alnwlsn/wc-80-archive/old-unknown/design-tables.xlsx

Sheet: io-addresses
Function | MEM | IO | 7 | 6 | 5 | 4 | 3 | 2 | 1 | 0 | 7 | 6 | 5 | 4 | 3 | 2 | 1 | 0 | value set on system reset boot
Disk Command/Status | 37EC | F0 |  |  |  |  |  |  |  |  |  |  |  |  |  |  |  |  | 0
Density Select | 37EC | F0 |  |  |  |  |  |  |  |  | 1 | 1 | 1 | 1 | 1 | x | x | DD | f8
Disk Track | 37ED | F1 |  |  |  |  |  |  |  |  |  |  |  |  |  |  |  |  | 0
Disk Sector | 37EE | F2 |  |  |  |  |  |  |  |  |  |  |  |  |  |  |  |  | 0
5/8 Select | 37EE | F2 |  |  |  |  |  |  |  |  | 1 | 8INCH | x | x | x | x | x | x | 80
Disk Data | 37EF | F3 |  |  |  |  |  |  |  |  |  |  |  |  |  |  |  |  | 0
Disk Select | 37E1 | F4 |  |  |  |  |  |  |  |  |  |  |  |  | DRV3 | DRV2 | DRV1 | DRV0 | 0
Model 3 Options | N/A | F4 |  |  |  |  |  |  |  |  | DD | x | WPRE | SIDE1 |  |  |  |  | 0
Interrupt Status | 37E0 | F6 | Clock | Disk |  |  |  |  |  |  |  |  |  |  |  |  |  |  | 0
WC80 Options | N/A | F6 |  |  |  |  |  |  |  |  |  |  |  |  | x | x | MOD3 | 2793 | 1
Printer | 37E8 | F8 |  |  |  |  |  |  |  |  |  |  |  |  |  |  |  |  | 0
mem bank 0 |  | 70 |  |  |  |  |  |  |  |  | !EXMEM 0000-3FFF |  | RAM !ROM
mem bank 1 |  | 71 |  |  |  |  |  |  |  |  | !EXMEM 4000-7FFF |  | RAM !ROM
mem bank 2 |  | 72 |  |  |  |  |  |  |  |  | !EXMEM 8000-BFFF |  | RAM !ROM
mem bank 3 |  | 73 |  |  |  |  |  |  |  |  | !EXMEM C000-FFFF |  | RAM !ROM
cpu display 4th char |  | 74
cpu display 3rd char |  | 75
cpu display 2nd char |  | 76
cpu display 1st char (left) |  | 77
sn76489 |  | a0 |  |  |  |  |  |  |  |  |  |  |  |  |  |  |  |  | 0
interrupt status |  | a0
ym2413 address |  | a2 |  |  |  |  |  |  |  |  |  |  |  |  |  |  |  |  | 1
ym2413 data |  | a3
ym2612 1-3 address |  | a4 |  |  |  |  |  |  |  |  |  |  |  |  |  |  |  |  | 2
ym2612 1-3 data |  | a5
ym2612 4-6 address |  | a6 |  |  |  |  |  |  |  |  |  |  |  |  |  |  |  |  | 3
ym2612 4-6 data |  | a7
ymf262 address0/status |  | a8 |  |  |  |  |  |  |  |  |  |  |  |  |  |  |  |  | 4
ymf262 data |  | a9
ymf262 address1 |  | aa |  |  |  |  |  |  |  |  |  |  |  |  |  |  |  |  | 5
orchestra 85 dac (!d7) |  | b5 |  |  |  |  |  |  |  |  |  |  |  |  |  |  |  |  | 0
orchestra 85 dac (!d7) |  | b9
orchestra 80 dac |  | bb
orchestra 80 dac |  | bc
sound options |  | bf
cassette port out |  | ff |  |  |  |  |  |  |  |  |  |  |  |  |  |  | v | v | 0
Keyboard option register |  | 78 |  |  |  |  |  |  |  |  | KEYM1 | KEYM0 | LED5 | LED4 | LED3 | LED2 | LED1 | LED0
CF card |  | 50
 |  | 51
 |  | 52
 |  | 53
 |  | 54
 |  | 55
 |  | 56
 |  | 57
vidstat |  | 5f |  |  |  |  | VS | HS | BTN | LPEN
vid options 1 |  | 5f |  |  |  |  |  |  |  |  | !RESET | DC2 | DC1 | DC0 | PL2 | PL1 | PL0 | CHIP | 0x72 reset | 0xf2 - 8x80 mode | 0xe6 - 64x6 mode
vid options 2 |  | 5e |  |  |  |  |  |  |  |  | ADR3 | ADR2 | ADR1 | ADR0 | MSK3 | MSK2 | MSK1 | MSK0
CRT controller data |  | 5d
CRT controller address |  | 5c
External hi-mem bank 0 |  | 7c
External hi-mem bank 1 |  | 7d
External hi-mem bank 2 |  | 7e
External hi-mem bank 3 |  | 7f
DSKY IO registers . . . |  | 60
. . . Read = key matrix |  | 61
. . . Write = display |  | 62
"" |  | 63
"" |  | 64
"" |  | 65
"" |  | 66
"" |  | 67
"" |  | 68
"" |  | 69
"" |  | 6a
"" |  | 6b
"" |  | 6c
"" |  | 6d
"" |  | 6e
* left most digit |  | 6f
KEYM = 0 keyboard | 3800-38ff
KEYM = 1 keyboard | ef00-efff
KEYM = 2 keyboard | f400-f4ff
KEYM = 3 keyboard | 7800-78ff

Sheet: memmap
Device |  | Main ROM / RAM | Keyboard Matrix | Arduino Board | Video Memory
 |  |  |  | Shared RAM and Extra RAM
IO Addr |  | 0x70-0x73 | 0x78 | 0x7c-0x7f | 0x5f
Memory Space | 0000 | Bank 0 0x70
 | 0400
 | 0800
 | 0C00
 | 1000
 | 1400
 | 1800
 | 1C00
 | 2000
 | 2400
 | 2800
 | 2C00
 | 3000 |  |  | 3000-33ff 1K dual port RAM
 | 3400
 | 3800 |  | 3800-38ff - TRS-80 model 1; KEYM = 0
 | 3C00 |  |  |  | IO 0x5e = 0x38 - TRS-80 64x16 Screen
 | 4000 | Bank 1 0x71
 | 4400
 | 4800
 | 4C00
 | 5000
 | 5400
 | 5800
 | 5C00
 | 6000
 | 6400
 | 6800
 | 6C00
 | 7000
 | 7400
 | 7800 |  | 7800-78ff - trs80 model 1 in slot 1; KEYM = 3
 | 7C00
 | 8000 | Bank 2 0x72 |  | HiMem Bank 0 0x7c
 | 8400
 | 8800
 | 8C00
 | 9000
 | 9400
 | 9800
 | 9C00
 | A000 |  |  | HiMem Bank 1 0x7d
 | A400
 | A800
 | AC00
 | B000
 | B400
 | B800
 | BC00
 | C000 | Bank 3 0x73 |  | HiMem Bank 2 0x7d
 | C400
 | C800
 | CC00
 | D000
 | D400
 | D800
 | DC00
 | E000 |  |  | HiMem Bank 3 0x7e
 | E400
 | E800
 | EC00 |  | EF00-EFFF; KEYM = 1
 | F000
 | F400 |  | F400-F4FF - trs-80 model 4; KEYM = 2
 | F800
 | FC00
Description/Notes |  | IO addresses 0x70-0x73 for each bank, select 1 of 32 banks in rom (0x00-0x20) or ram (0x20-0x40). 16K each | IO address 0x78 - Set bits 6:7 to select 1 of 4 keyboard memory locations | IO addresses 0x7c-0x7f for each bank, select 1 of 64 banks of RAM, 8K each | Ram can be aligned to any of the bold boxes above, and each of 4 1K sections can be masked or unmasked within.
 |  |  |  | If bit 7 is set on any of the 4 bank selections, the extra ram there will be removed and the address space open to be used by other devices | IO address 0x5e is used to set the location and mask: value = 0xam, where: nibble a is address location, and nibble m is the mask. Bits set to 0 will disable that section
 |  | EXMEM - clearing of bit 7 will enable other devices to override rom/ram in memory space |  | This HIMem area (0x8000 and above) corresponds to the memory stored in the Expansion Interface in a real TRS-80
 |  |  |  |  | example:
 |  |  |  |  | 0x38 - start at address 0x3000; mask all but section 3 (bit3 set) - provides 1K section at 0x3c00
 |  |  |  |  | 0x5F - start at address 0x5000, aand use all 4 sections provides 4K of ram at 0x5000-0x5fff

Sheet: memmap(old)
 |  | Main ROM / RAM | Keyboard Matrix | Hi-mem ram on Arduino board | Arduino Dual Port Shared RAM
 | IO Addr | 0x70-0x73 | 0x78 | 0x7c-0x7f
Memory Space | 0000 | Bank 0 0x70 |  |  |  | 1 | 1 | 100
 | 1000 |  |  |  |  | 2 | 2 | 200
 | 2000 |  |  |  |  | 3 | 3 | 300
 | 3000 |  | 3800-38ff - TRS-80 model 1 - KEYM = 0 | 3000-33ff 1K dual port RAM |  | 4 | 4 | 400
 | 4000 | Bank 1 0x71 |  |  |  | 5 | 5 | 500
 | 5000 |  |  |  |  | 6 | 6 | 600
 | 6000 |  |  |  |  | 7 | 7 | 700
 | 7000 |  | 7800-78ff - trs80 model 1 in slot 1 KEYM = 3 |  |  | 8 | 8 | 800
 | 8000 | Bank 2 0x72 |  | HiMem Bank 0 0x7c |  | 9 | 9 | 900
 | 9000 |  |  |  |  | 10 | A | A00
 | A000 |  |  | HiMem Bank 1 0x7d |  | 11 | B | B00
 | B000 |  |  |  |  | 12 | C | C00
 | C000 | Bank 3 0x73 |  | HiMem Bank 2 0x7d |  | 13 | D | D00
 | D000 |  |  |  |  | 14 | E | E00
 | E000 |  | EF00-EFFF KEYM = 1 | HiMem Bank 3 0x7e |  | 15 | F | F00
 | F000 |  | F400-F4FF - trs-80 model 4 KEYM = 2 |  |  | 16 | 10 | 1000
 |  |  |  |  |  | 17 | 11 | 1100
 |  |  |  |  |  | 18 | 12 | 1200
 |  | IO addresses 0x70-0x73 for each bank, select 1 of 32 banks in rom (0x00-0x20) or ram (0x20-0x40). 16K each | IO address 0x78 - Set bits 6:7 to select 1 of 4 keyboard memory locations | IO addresses 0x7c-0x7f for each bank, select 1 of 64 banks of RAM, 8K each |  | 19 | 13 | 1300
 |  |  |  | If bit 7 is set on any of the 4 bank selections, the extra ram there will be removed and the address space open to be used by other devices |  | 20 | 14 | 1400
 |  |  |  |  |  | 21 | 15 | 1500
 |  |  |  |  |  | 22 | 16 | 1600
 |  |  |  |  |  | 23 | 17 | 1700
 |  | EXMEM - clearing of bit 7 will enable other devices to override rom/ram in memory space |  | This HIMem area (0x8000 and above) corresponds to the memory stored in the Expansion Interface in a real TRS-80 |  | 24 | 18 | 1800
 |  |  |  |  |  | 25 | 19 | 1900
 |  |  |  |  |  | 26 | 1A | 1A00
 |  |  |  |  |  | 27 | 1B | 1B00
 |  |  |  |  |  | 28 | 1C | 1C00
 |  |  |  |  |  | 29 | 1D | 1D00
 |  |  |  |  |  | 30 | 1E | 1E00
 |  |  |  |  |  | 31 | 1F | 1F00
 |  |  |  |  |  | 32 | 20 | 2000
 |  |  |  |  |  | 33 | 21 | 2100
 |  |  |  |  |  | 34 | 22 | 2200
 |  |  |  |  |  | 35 | 23 | 2300
 |  |  |  |  |  | 36 | 24 | 2400
 |  |  |  |  |  | 37 | 25 | 2500
 |  |  |  |  |  | 38 | 26 | 2600
 |  |  |  |  |  | 39 | 27 | 2700
 |  |  |  |  |  | 40 | 28 | 2800
 |  |  |  |  |  | 41 | 29 | 2900
 |  |  |  |  |  | 42 | 2A | 2A00
 |  |  |  |  |  | 43 | 2B | 2B00
 |  |  |  |  |  | 44 | 2C | 2C00
 |  |  |  |  |  | 45 | 2D | 2D00
 |  |  |  |  |  | 46 | 2E | 2E00
 |  |  |  |  |  | 47 | 2F | 2F00
 |  |  |  |  |  | 48 | 30 | 3000
 |  |  |  |  |  | 49 | 31 | 3100
 |  |  |  |  |  | 50 | 32 | 3200
 |  |  |  |  |  | 51 | 33 | 3300
 |  |  |  |  |  | 52 | 34 | 3400
 |  |  |  |  |  | 53 | 35 | 3500
 |  |  |  |  |  | 54 | 36 | 3600
 |  |  |  |  |  | 55 | 37 | 3700
 |  |  |  |  |  | 56 | 38 | 3800
 |  |  |  |  |  | 57 | 39 | 3900
 |  |  |  |  |  | 58 | 3A | 3A00
 |  |  |  |  |  | 59 | 3B | 3B00
 |  |  |  |  |  | 60 | 3C | 3C00
 |  |  |  |  |  | 61 | 3D | 3D00
 |  |  |  |  |  | 62 | 3E | 3E00
 |  |  |  |  |  | 63 | 3F | 3F00
 |  |  |  |  |  | 64 | 40 | 4000
 |  |  |  |  |  | 65 | 41 | 4100
 |  |  |  |  |  | 66 | 42 | 4200
 |  |  |  |  |  | 67 | 43 | 4300
 |  |  |  |  |  | 68 | 44 | 4400
 |  |  |  |  |  | 69 | 45 | 4500
 |  |  |  |  |  | 70 | 46 | 4600
 |  |  |  |  |  | 71 | 47 | 4700
 |  |  |  |  |  | 72 | 48 | 4800
 |  |  |  |  |  | 73 | 49 | 4900
 |  |  |  |  |  | 74 | 4A | 4A00
 |  |  |  |  |  | 75 | 4B | 4B00
 |  |  |  |  |  | 76 | 4C | 4C00
 |  |  |  |  |  | 77 | 4D | 4D00
 |  |  |  |  |  | 78 | 4E | 4E00
 |  |  |  |  |  | 79 | 4F | 4F00
 |  |  |  |  |  | 80 | 50 | 5000
 |  |  |  |  |  | 81 | 51 | 5100
 |  |  |  |  |  | 82 | 52 | 5200
 |  |  |  |  |  | 83 | 53 | 5300
 |  |  |  |  |  | 84 | 54 | 5400
 |  |  |  |  |  | 85 | 55 | 5500
 |  |  |  |  |  | 86 | 56 | 5600
 |  |  |  |  |  | 87 | 57 | 5700
 |  |  |  |  |  | 88 | 58 | 5800
 |  |  |  |  |  | 89 | 59 | 5900
 |  |  |  |  |  | 90 | 5A | 5A00
 |  |  |  |  |  | 91 | 5B | 5B00
 |  |  |  |  |  | 92 | 5C | 5C00
 |  |  |  |  |  | 93 | 5D | 5D00
 |  |  |  |  |  | 94 | 5E | 5E00
 |  |  |  |  |  | 95 | 5F | 5F00
 |  |  |  |  |  | 96 | 60 | 6000
 |  |  |  |  |  | 97 | 61 | 6100
 |  |  |  |  |  | 98 | 62 | 6200
 |  |  |  |  |  | 99 | 63 | 6300
 |  |  |  |  |  | 100 | 64 | 6400
 |  |  |  |  |  | 101 | 65 | 6500
 |  |  |  |  |  | 102 | 66 | 6600
 |  |  |  |  |  | 103 | 67 | 6700
 |  |  |  |  |  | 104 | 68 | 6800
 |  |  |  |  |  | 105 | 69 | 6900
 |  |  |  |  |  | 106 | 6A | 6A00
 |  |  |  |  |  | 107 | 6B | 6B00
 |  |  |  |  |  | 108 | 6C | 6C00
 |  |  |  |  |  | 109 | 6D | 6D00
 |  |  |  |  |  | 110 | 6E | 6E00
 |  |  |  |  |  | 111 | 6F | 6F00
 |  |  |  |  |  | 112 | 70 | 7000
 |  |  |  |  |  | 113 | 71 | 7100
 |  |  |  |  |  | 114 | 72 | 7200
 |  |  |  |  |  | 115 | 73 | 7300
 |  |  |  |  |  | 116 | 74 | 7400
 |  |  |  |  |  | 117 | 75 | 7500
 |  |  |  |  |  | 118 | 76 | 7600
 |  |  |  |  |  | 119 | 77 | 7700
 |  |  |  |  |  | 120 | 78 | 7800
 |  |  |  |  |  | 121 | 79 | 7900
 |  |  |  |  |  | 122 | 7A | 7A00
 |  |  |  |  |  | 123 | 7B | 7B00
 |  |  |  |  |  | 124 | 7C | 7C00
 |  |  |  |  |  | 125 | 7D | 7D00
 |  |  |  |  |  | 126 | 7E | 7E00
 |  |  |  |  |  | 127 | 7F | 7F00
 |  |  |  |  |  | 128 | 80 | 8000
 |  |  |  |  |  | 129 | 81 | 8100
 |  |  |  |  |  | 130 | 82 | 8200
 |  |  |  |  |  | 131 | 83 | 8300
 |  |  |  |  |  | 132 | 84 | 8400
 |  |  |  |  |  | 133 | 85 | 8500
 |  |  |  |  |  | 134 | 86 | 8600
 |  |  |  |  |  | 135 | 87 | 8700
 |  |  |  |  |  | 136 | 88 | 8800
 |  |  |  |  |  | 137 | 89 | 8900
 |  |  |  |  |  | 138 | 8A | 8A00
 |  |  |  |  |  | 139 | 8B | 8B00
 |  |  |  |  |  | 140 | 8C | 8C00
 |  |  |  |  |  | 141 | 8D | 8D00
 |  |  |  |  |  | 142 | 8E | 8E00
 |  |  |  |  |  | 143 | 8F | 8F00
 |  |  |  |  |  | 144 | 90 | 9000
 |  |  |  |  |  | 145 | 91 | 9100
 |  |  |  |  |  | 146 | 92 | 9200
 |  |  |  |  |  | 147 | 93 | 9300
 |  |  |  |  |  | 148 | 94 | 9400
 |  |  |  |  |  | 149 | 95 | 9500
 |  |  |  |  |  | 150 | 96 | 9600
 |  |  |  |  |  | 151 | 97 | 9700
 |  |  |  |  |  | 152 | 98 | 9800
 |  |  |  |  |  | 153 | 99 | 9900
 |  |  |  |  |  | 154 | 9A | 9A00
 |  |  |  |  |  | 155 | 9B | 9B00
 |  |  |  |  |  | 156 | 9C | 9C00
 |  |  |  |  |  | 157 | 9D | 9D00
 |  |  |  |  |  | 158 | 9E | 9E00
 |  |  |  |  |  | 159 | 9F | 9F00
 |  |  |  |  |  | 160 | A0 | A000
 |  |  |  |  |  | 161 | A1 | A100
 |  |  |  |  |  | 162 | A2 | A200
 |  |  |  |  |  | 163 | A3 | A300
 |  |  |  |  |  | 164 | A4 | A400
 |  |  |  |  |  | 165 | A5 | A500
 |  |  |  |  |  | 166 | A6 | A600
 |  |  |  |  |  | 167 | A7 | A700
 |  |  |  |  |  | 168 | A8 | A800
 |  |  |  |  |  | 169 | A9 | A900
 |  |  |  |  |  | 170 | AA | AA00
 |  |  |  |  |  | 171 | AB | AB00
 |  |  |  |  |  | 172 | AC | AC00
 |  |  |  |  |  | 173 | AD | AD00
 |  |  |  |  |  | 174 | AE | AE00
 |  |  |  |  |  | 175 | AF | AF00
 |  |  |  |  |  | 176 | B0 | B000
 |  |  |  |  |  | 177 | B1 | B100
 |  |  |  |  |  | 178 | B2 | B200
 |  |  |  |  |  | 179 | B3 | B300
 |  |  |  |  |  | 180 | B4 | B400
 |  |  |  |  |  | 181 | B5 | B500
 |  |  |  |  |  | 182 | B6 | B600
 |  |  |  |  |  | 183 | B7 | B700
 |  |  |  |  |  | 184 | B8 | B800
 |  |  |  |  |  | 185 | B9 | B900
 |  |  |  |  |  | 186 | BA | BA00
 |  |  |  |  |  | 187 | BB | BB00
 |  |  |  |  |  | 188 | BC | BC00
 |  |  |  |  |  | 189 | BD | BD00
 |  |  |  |  |  | 190 | BE | BE00
 |  |  |  |  |  | 191 | BF | BF00
 |  |  |  |  |  | 192 | C0 | C000
 |  |  |  |  |  | 193 | C1 | C100
 |  |  |  |  |  | 194 | C2 | C200
 |  |  |  |  |  | 195 | C3 | C300
 |  |  |  |  |  | 196 | C4 | C400
 |  |  |  |  |  | 197 | C5 | C500
 |  |  |  |  |  | 198 | C6 | C600
 |  |  |  |  |  | 199 | C7 | C700
 |  |  |  |  |  | 200 | C8 | C800
 |  |  |  |  |  | 201 | C9 | C900
 |  |  |  |  |  | 202 | CA | CA00
 |  |  |  |  |  | 203 | CB | CB00
 |  |  |  |  |  | 204 | CC | CC00
 |  |  |  |  |  | 205 | CD | CD00
 |  |  |  |  |  | 206 | CE | CE00
 |  |  |  |  |  | 207 | CF | CF00
 |  |  |  |  |  | 208 | D0 | D000
 |  |  |  |  |  | 209 | D1 | D100
 |  |  |  |  |  | 210 | D2 | D200
 |  |  |  |  |  | 211 | D3 | D300
 |  |  |  |  |  | 212 | D4 | D400
 |  |  |  |  |  | 213 | D5 | D500
 |  |  |  |  |  | 214 | D6 | D600
 |  |  |  |  |  | 215 | D7 | D700
 |  |  |  |  |  | 216 | D8 | D800
 |  |  |  |  |  | 217 | D9 | D900
 |  |  |  |  |  | 218 | DA | DA00
 |  |  |  |  |  | 219 | DB | DB00
 |  |  |  |  |  | 220 | DC | DC00
 |  |  |  |  |  | 221 | DD | DD00
 |  |  |  |  |  | 222 | DE | DE00
 |  |  |  |  |  | 223 | DF | DF00
 |  |  |  |  |  | 224 | E0 | E000
 |  |  |  |  |  | 225 | E1 | E100
 |  |  |  |  |  | 226 | E2 | E200
 |  |  |  |  |  | 227 | E3 | E300
 |  |  |  |  |  | 228 | E4 | E400
 |  |  |  |  |  | 229 | E5 | E500
 |  |  |  |  |  | 230 | E6 | E600
 |  |  |  |  |  | 231 | E7 | E700
 |  |  |  |  |  | 232 | E8 | E800
 |  |  |  |  |  | 233 | E9 | E900
 |  |  |  |  |  | 234 | EA | EA00
 |  |  |  |  |  | 235 | EB | EB00
 |  |  |  |  |  | 236 | EC | EC00
 |  |  |  |  |  | 237 | ED | ED00
 |  |  |  |  |  | 238 | EE | EE00
 |  |  |  |  |  | 239 | EF | EF00
 |  |  |  |  |  | 240 | F0 | F000
 |  |  |  |  |  | 241 | F1 | F100
 |  |  |  |  |  | 242 | F2 | F200
 |  |  |  |  |  | 243 | F3 | F300
 |  |  |  |  |  | 244 | F4 | F400
 |  |  |  |  |  | 245 | F5 | F500
 |  |  |  |  |  | 246 | F6 | F600
 |  |  |  |  |  | 247 | F7 | F700
 |  |  |  |  |  | 248 | F8 | F800
 |  |  |  |  |  | 249 | F9 | F900
 |  |  |  |  |  | 250 | FA | FA00
 |  |  |  |  |  | 251 | FB | FB00
 |  |  |  |  |  | 252 | FC | FC00
 |  |  |  |  |  | 253 | FD | FD00
 |  |  |  |  |  | 254 | FE | FE00
 |  |  |  |  |  | 255 | FF | FF00

Sheet: bus-pinout
org | lu | ul | modi | pin | desc | TRS-80 EXP HEADER |  |  |  | TRS-80 EXP HEADER |  |  |  | TRS-80 PROTO HEADER |  |  |  | TRS-80 PROTO HEADER
 |  |  |  |  |  | M UP |  |  |  | F UP |  |  |  | M UP |  |  |  | F UP
1 | 0 | 0 | 2 | RAS* | Row Address Strobe output for 16 pin dynamic rams | SYSRES* | 1 | 2 | RAS* | RAS* | 2 | 1 | SYSRES* | vcc | 1 | 2 | vcc | vcc | 2 | 1 | vcc
3 | 0 | 0 | 4 | CAS* | Column Address Strobe output for 16 pin dynamic rams | A10 | 3 | 4 | CAS* | CAS* | 4 | 3 | A10 | gnd | 3 | 4 | gnd | gnd | 4 | 3 | gnd
5 | 0 | 0 | 6 | A12 | Address output | A13 | 5 | 6 | A12 | A12 | 6 | 5 | A13 | \memrq | 5 | 6 | \ioreq | \ioreq | 6 | 5 | \memrq
7 | 0 | 0 | 8 | A15 | Address output | GND | 7 | 8 | A15 | A15 | 8 | 7 | GND | \rd | 7 | 8 | \wr | \wr | 8 | 7 | \rd
9 | 0 | 0 | 10 | A11 | Address output | A14 | 9 | 10 | A11 | A11 | 10 | 9 | A14 | \inuse | 9 | 10 | \disable | \disable | 10 | 9 | \inuse
11 | 0 | 0 | 12 | A8 | Address output | OUT* | 11 | 12 | A8 | A8 | 12 | 11 | OUT* | d0 | 11 | 12 | d1 | d1 | 12 | 11 | d0
13 | 0 | 0 | 14 | WR* | Memory Write strobe output | INTAK* | 13 | 14 | WR* | WR* | 14 | 13 | INTAK* | d2 | 13 | 14 | d3 | d3 | 14 | 13 | d2
15 | 0 | 0 | 16 | RD* | Memory Read strobe output | MUX | 15 | 16 | RD* | RD* | 16 | 15 | MUX | d4 | 15 | 16 | d5 | d5 | 16 | 15 | d4
17 | 0 | 0 | 18 | A9 | Address output | D4 | 17 | 18 | A9 | A9 | 18 | 17 | D4 | d6 | 17 | 18 | d7 | d7 | 18 | 17 | d6
19 | 0 | 0 | 20 | IN* | Peripheral Read strobe output | D7 | 19 | 20 | IN* | IN* | 20 | 19 | D7 | a0 | 19 | 20 | a1 | a1 | 20 | 19 | a0
21 | 0 | 0 | 22 | INT* | Interrupt input (Maskable) | D1 | 21 | 22 | INT* | INT* | 22 | 21 | D1 | a2 | 21 | 22 | a3 | a3 | 22 | 21 | a2
23 | 0 | 0 | 24 | TEST* | A logic 0 on TEST* input tri-states A0-A15, D0-D7, WR*, RD*, IN*, OUT*, RAS*, CAS* and MUX*. | D6 | 23 | 24 | TEST* | TEST* | 24 | 23 | D6 | a4 | 23 | 24 | a5 | a5 | 24 | 23 | a4
25 | 0 | 0 | 26 | A0 | Address output | D3 | 25 | 26 | A0 | A0 | 26 | 25 | D3 | a6 | 25 | 26 | a7 | a7 | 26 | 25 | a6
27 | 0 | 0 | 28 | A1 | Address output | D5 | 27 | 28 | A1 | A1 | 28 | 27 | D5 | a8 | 27 | 28 | a9 | a9 | 28 | 27 | a8
29 | 0 | 0 | 30 | GND | Signal ground | D0 | 29 | 30 | GND | GND | 30 | 29 | D0 | a10 | 29 | 30 | a11 | a11 | 30 | 29 | a10
31 | 0 | 0 | 32 | A4 | Address output | D2 | 31 | 32 | A4 | A4 | 32 | 31 | D2 | a12 | 31 | 32 | a13 | a13 | 32 | 31 | a12
33 | 0 | 0 | 34 | WAIT* | Processor wait input, to allow for slow memory | A3 | 33 | 34 | WAIT* | WAIT* | 34 | 33 | A3 | a14 | 33 | 34 | a15 | a15 | 34 | 33 | a14
35 | 0 | 0 | 36 | A5 | Address output | A7 | 35 | 36 | A5 | A5 | 36 | 35 | A7 |  | 35 | 36 |  |  | 36 | 35
37 | 0 | 0 | 38 | GND | Signal ground | A6 | 37 | 38 | GND | GND | 38 | 37 | A6 |  | 37 | 38 |  |  | 38 | 37
39 | 0 | 0 | 40 | +5V | (limited current - Level I Model 1s only) | A2 | 39 | 40 | +5V | +5V | 40 | 39 | A2 |  | 39 | 40 |  |  | 40 | 39
2 | 1 | 1 | 1 | SYSRES* | System reset output. Low during power-up initialize or when the reset button is pressed
4 | 1 | 1 | 3 | A10 | Address output
6 | 1 | 1 | 5 | A13 | Address output | TRS-80 W HEADER |  |  |  | TRS-80 W HEADER
8 | 1 | 1 | 7 | GND | Signal Ground | M UP |  |  |  | F UP
10 | 1 | 1 | 9 | A14 | Address output | SYSRES* | 1 | 2 | RAS* | RAS* | 2 | 1 | SYSRES*
12 | 1 | 1 | 11 | OUT* | Peripheral Write strobe output | A10 | 3 | 4 | EXMEM* | EXMEM* | 4 | 3 | A10
14 | 1 | 1 | 13 | INTAK* | Interrupt Acknowledge output | A13 | 5 | 6 | A12 | A12 | 6 | 5 | A13
16 | 1 | 1 | 15 | MUX | Multiplexer Control output for 16 pin dynamic RAMs | GND | 7 | 8 | A15 | A15 | 8 | 7 | GND
18 | 1 | 1 | 17 | D4 | Bidirectional data bus | A14 | 9 | 10 | A11 | A11 | 10 | 9 | A14
20 | 1 | 1 | 19 | D7 | Bidirectional data bus | OUT* | 11 | 12 | A8 | A8 | 12 | 11 | OUT*
22 | 1 | 1 | 21 | D1 | Bidirectional data bus | INTAK* | 13 | 14 | WR* | WR* | 14 | 13 | INTAK*
24 | 1 | 1 | 23 | D6 | Bidirectional data bus | INUSE* | 15 | 16 | RD* | RD* | 16 | 15 | INUSE*
26 | 1 | 1 | 25 | D3 | Bidirectional data bus | D4 | 17 | 18 | A9 | A9 | 18 | 17 | D4
28 | 1 | 1 | 27 | D5 | Bidirectional data bus | D7 | 19 | 20 | IN* | IN* | 20 | 19 | D7
30 | 1 | 1 | 29 | D0 | Bidirectional data bus | D1 | 21 | 22 | INT* | INT* | 22 | 21 | D1
32 | 1 | 1 | 31 | D2 | Bidirectional data bus | D6 | 23 | 24 | CLK | CLK | 24 | 23 | D6
34 | 1 | 1 | 33 | A3 | Address output | D3 | 25 | 26 | A0 | A0 | 26 | 25 | D3 |  |  |  | e
36 | 1 | 1 | 35 | A7 | Address output | D5 | 27 | 28 | A1 | A1 | 28 | 27 | D5
38 | 1 | 1 | 37 | A6 | Address output | D0 | 29 | 30 | GND | GND | 30 | 29 | D0
40 | 1 | 1 | 39 | A2 | Address output | D2 | 31 | 32 | A4 | A4 | 32 | 31 | D2
 |  |  |  |  |  | A3 | 33 | 34 | WAIT* | WAIT* | 34 | 33 | A3
 |  |  |  |  |  | A7 | 35 | 36 | A5 | A5 | 36 | 35 | A7
 |  |  |  |  |  | A6 | 37 | 38 | GND | GND | 38 | 37 | A6
 |  |  |  |  |  | A2 | 39 | 40 | +5V | +5V | 40 | 39 | A2

Sheet: vtiming
Video Timing Calculator |  |  |  | pulse lengths xdotclock |  |  |  |  |  |  | Screen Resolutions (us/line) |  |  |  |  |  |  | Measurements
baseclock(mhz) | div | divf(mhz) | dotclk_p(ns) | 2 | 3 | 4 | 5 | 6 | 7 | 8 | 80x8 | 80x6 | 64x8 | 64x6 | 32x8 | 16x8 |  | active video | us | dots | ns/dot
30 | 2 | 15 | 66.66666667 | 133.3333333 | 200 | 266.6666667 | 333.3333333 | 400 | 466.6666667 | 533.3333333 | 42.66666667 | 32 | 34.13333333 | 25.6 | 17.06666667 | 8.533333333 |  | real trs-80 | 36 | 384 | 93.75
 | 3 | 10 | 100 | 200 | 300 | 400 | 500 | 600 | 700 | 800 | 64 | 48 | 51.2 | 38.4 | 25.6 | 12.8 | Highlighter | amber l-r | 41 | 640 | 64.0625
 | 4 | 7.5 | 133.3333333 | 266.6666667 | 400 | 533.3333333 | 666.6666667 | 800 | 933.3333333 | 1066.666667 | 85.33333333 | 64 | 68.26666667 | 51.2 | 34.13333333 | 17.06666667 | less | 7"bw l-r | 48
 | 5 | 6 | 166.6666667 | 333.3333333 | 500 | 666.6666667 | 833.3333333 | 1000 | 1166.666667 | 1333.333333 | 106.6666667 | 80 | 85.33333333 | 64 | 42.66666667 | 21.33333333 | 36 | sanyo | 44.6 | 640 | 69.6875
 | 6 | 5 | 200 | 400 | 600 | 800 | 1000 | 1200 | 1400 | 1600 | 128 | 96 | 102.4 | 76.8 | 51.2 | 25.6 | greater | green | 42.9 | 640 | 67.03125
 | 7 | 4.285714286 | 233.3333333 | 466.6666667 | 700 | 933.3333333 | 1166.666667 | 1400 | 1633.333333 | 1866.666667 | 149.3333333 | 112 | 119.4666667 | 89.6 | 59.73333333 | 29.86666667 | 43
 | 8 | 3.75 | 266.6666667 | 533.3333333 | 800 | 1066.666667 | 1333.333333 | 1600 | 1866.666667 | 2133.333333 | 170.6666667 | 128 | 136.5333333 | 102.4 | 68.26666667 | 34.13333333
 | 9 | 3.333333333 | 300 | 600 | 900 | 1200 | 1500 | 1800 | 2100 | 2400 | 192 | 144 | 153.6 | 115.2 | 76.8 | 38.4
 |  |  | dots/line |  |  |  |  |  |  |  | 640 | 480 | 512 | 384 | 256 | 128
LTC6903
OCT | 13 |  |  |  | 1101 |  |  | bitmask base (dec)
DAC | 831 |  |  |  | 00000000000000000000001100111111 |  |  | 160
f | 14323358.61 | 14320000 | 3358.606409
f mhz | 14.32335861
 |  |  | name | index | bit | val (d) | val (hex)
 |  | d15 | oct3 | 0 | 1 | 161
 |  | d14 | oct2 | 1 | 1 | 161
 |  | d13 | oct1 | 2 | 0 | 160
 |  | d12 | oct0 | 3 | 1 | 161
 |  | d11 | dac9 | 22 | 1 | 161
 |  | d10 | dac8 | 23 | 1 | 161
 |  | d9 | dac7 | 24 | 0 | 160
 |  | d8 | dac6 | 25 | 0 | 160
 |  | d7 | dac5 | 26 | 1 | 161
 |  | d6 | dac4 | 27 | 1 | 161
 |  | d5 | dac3 | 28 | 1 | 161
 |  | d4 | dac2 | 29 | 1 | 161
 |  | d3 | dac1 | 30 | 1 | 161
 |  | d2 | dac0 | 31 | 1 | 161
 |  | d1 | cnf1 |  | 0 | 160
 |  | d0 | cnf0 |  | 0 | 160
