alnwlsn/wc-80-archive/img/arduino-board.jpg

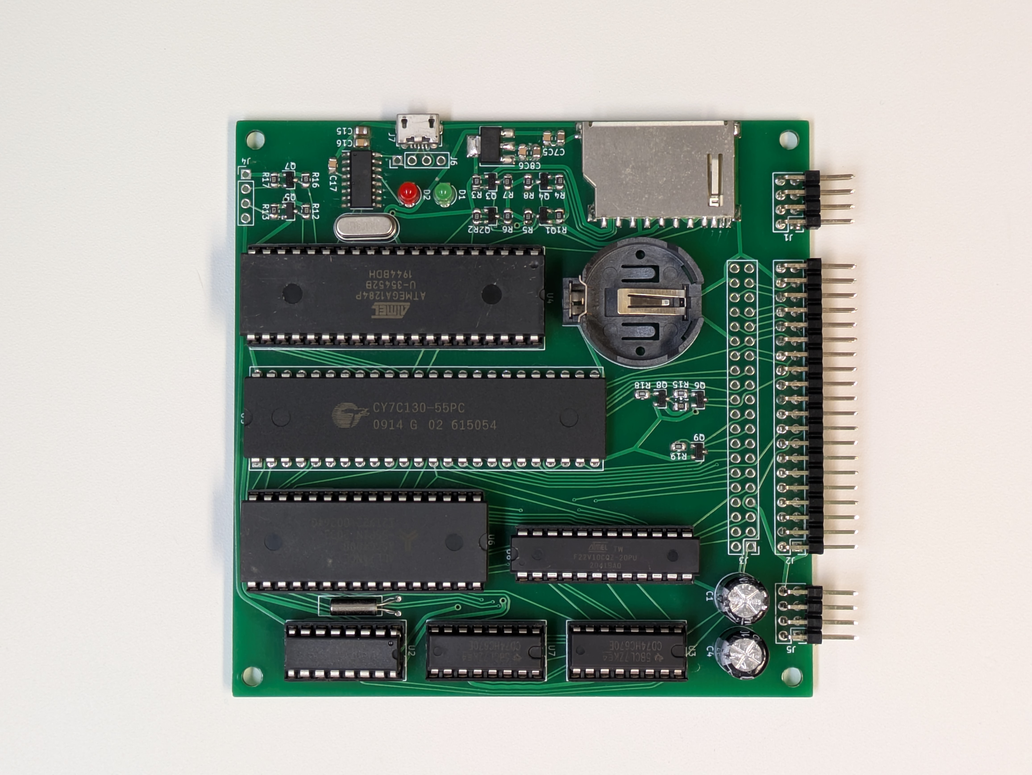
img/arduino-board.jpg
