alnwlsn/wc-80-archive/img/boot-menu.jpg

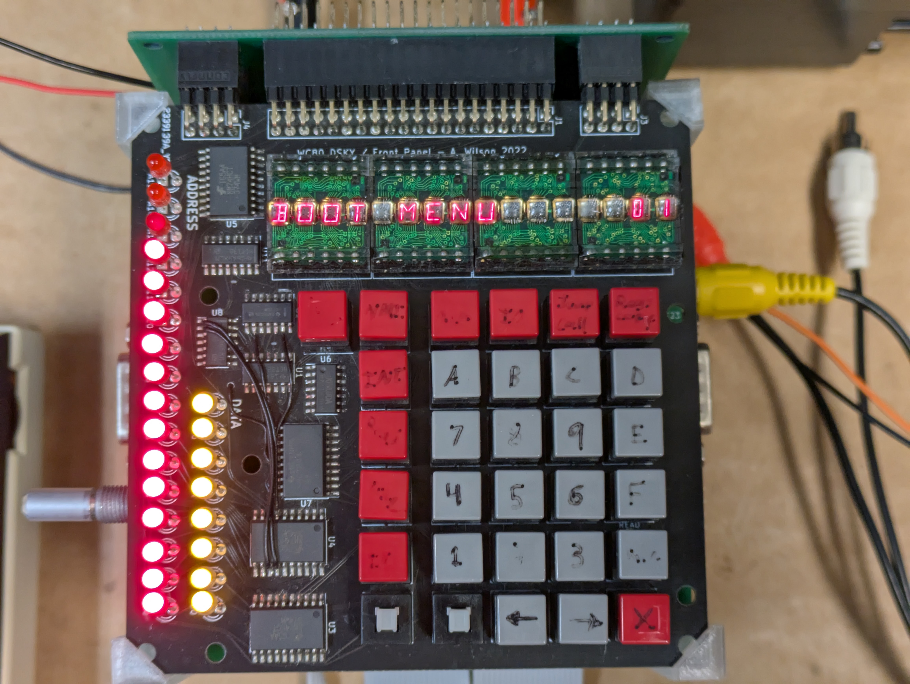
img/boot-menu.jpg
