alnwlsn/wc-80-archive/img/dsky.jpg

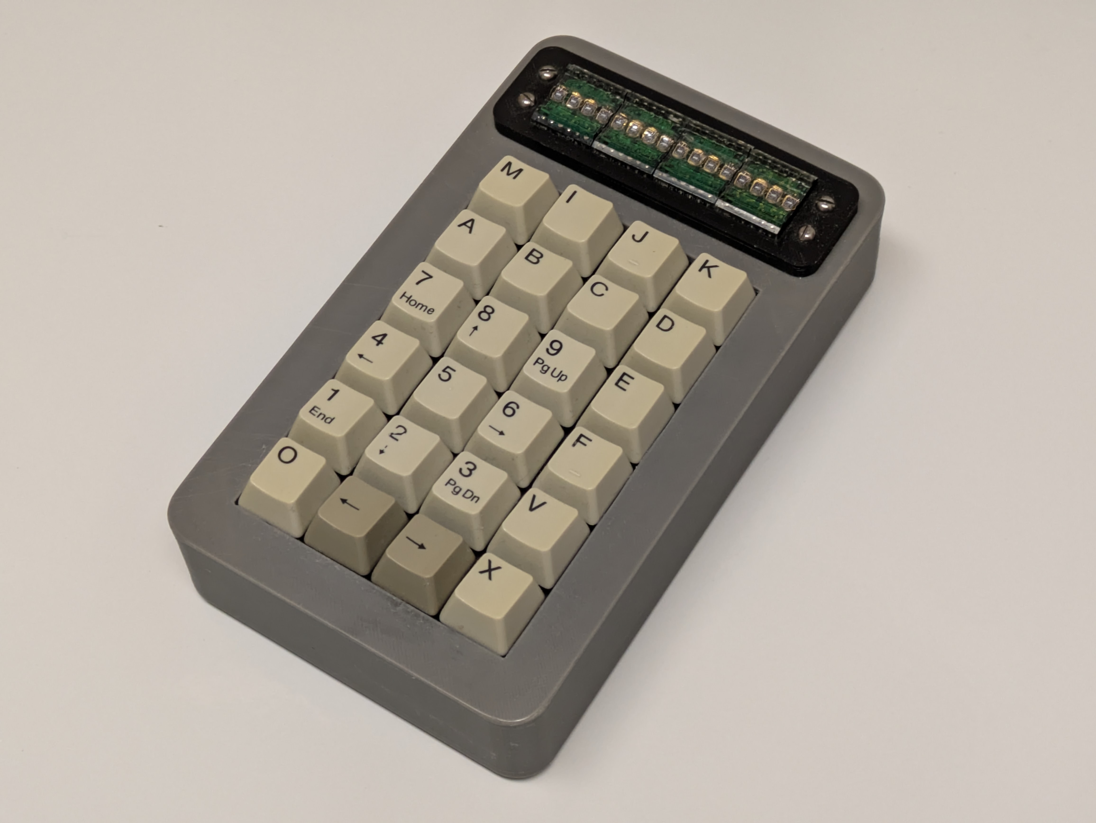
img/dsky.jpg
