alnwlsn/wc-80-archive/img/floppy-board.jpg

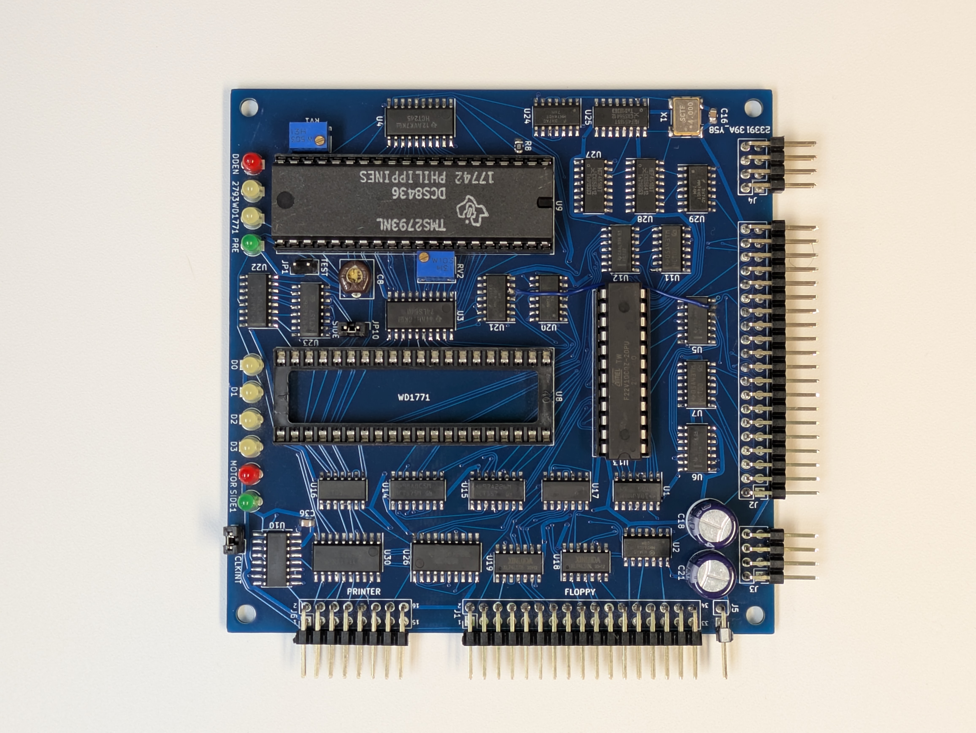
img/floppy-board.jpg
