alnwlsn/wc-80-archive/img/frehd-board.jpg

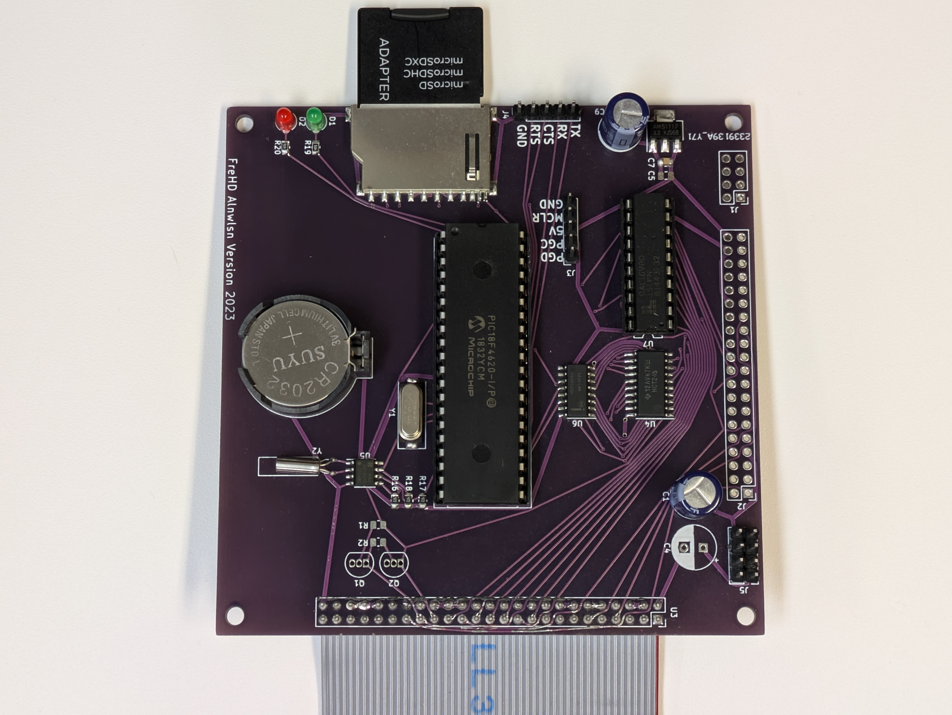
img/frehd-board.jpg
