alnwlsn/wc-80-archive/img/trs80map.png

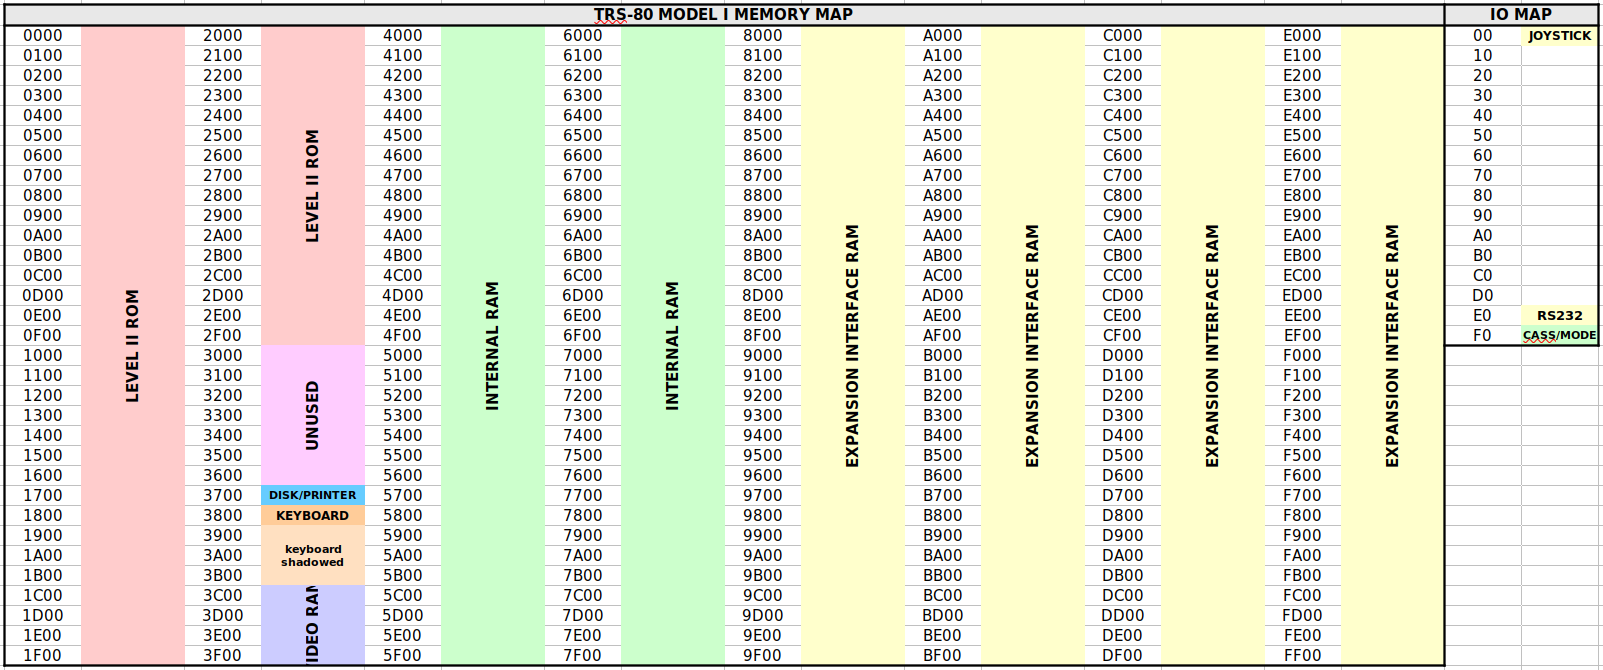
img/trs80map.png
