alnwlsn/wc-80-archive/img/trs-80-interface.jpg

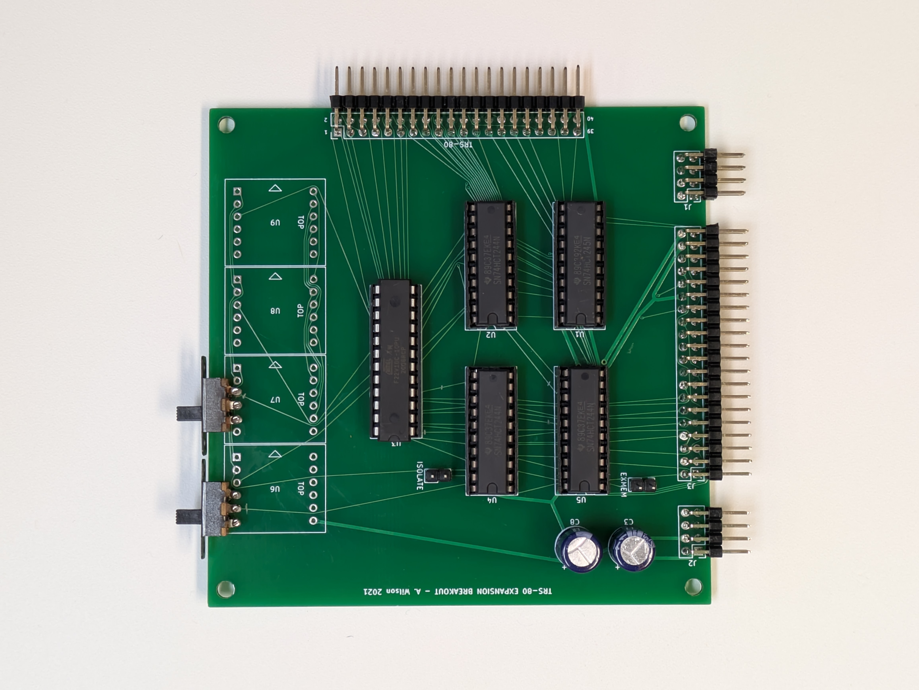
img/trs-80-interface.jpg
