alnwlsn/wc-80-archive/img/wc80map.png

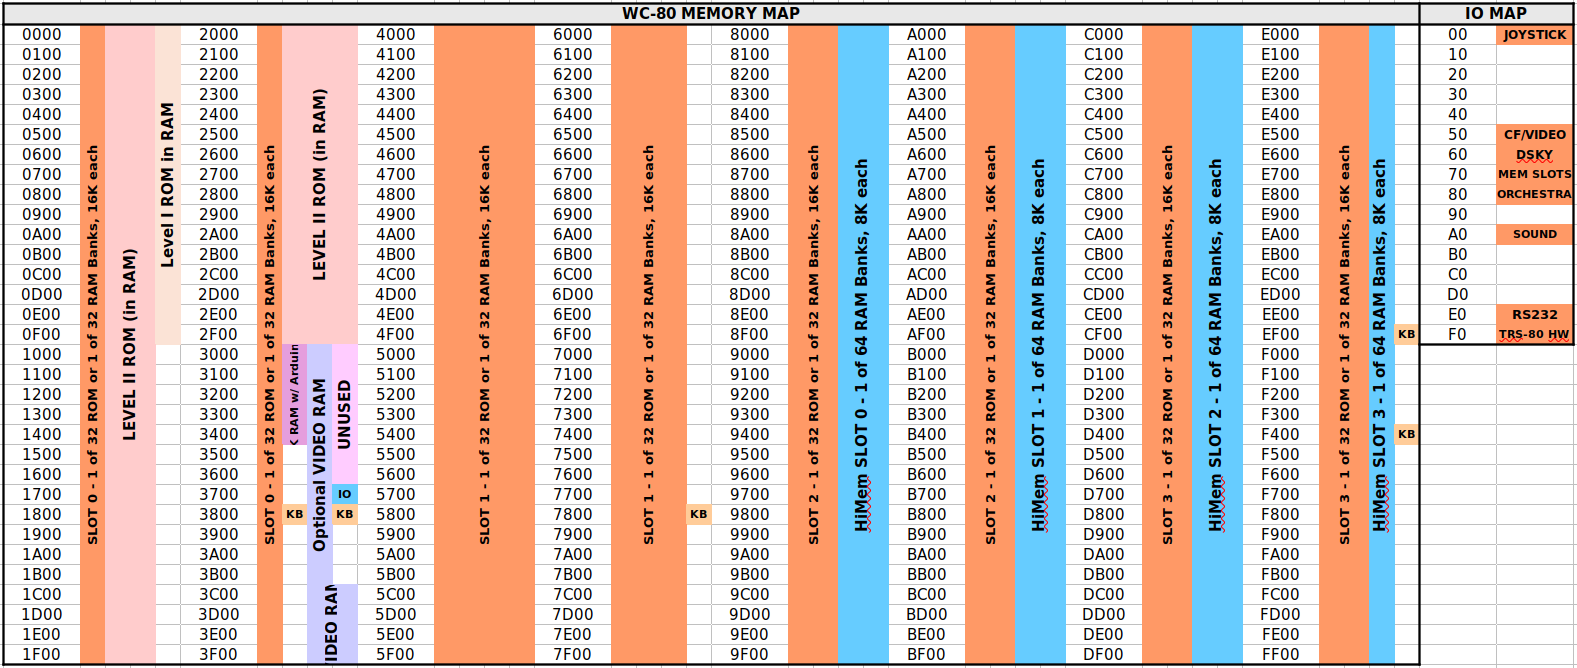
img/wc80map.png
