alnwlsn/wc-80-archive/keyboard-labels/keys/1.png

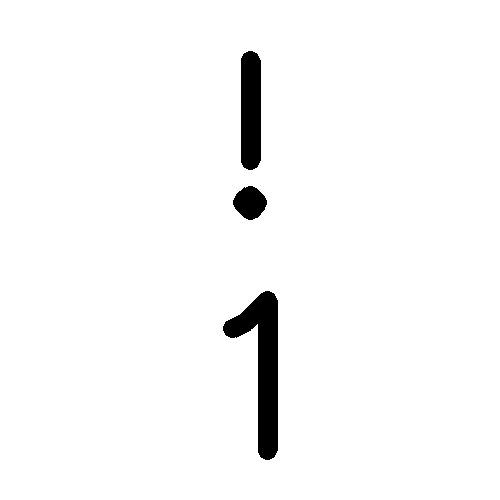
keyboard-labels/keys/1.png
