alnwlsn/wc-80-archive/keyboard-labels/keys/2.png

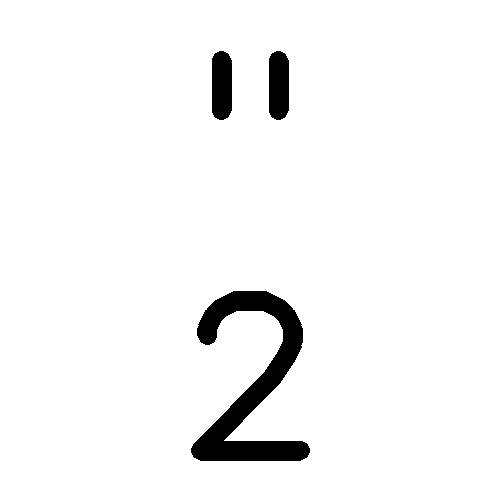
keyboard-labels/keys/2.png
