alnwlsn/wc-80-archive/keyboard-labels/keys/3.png

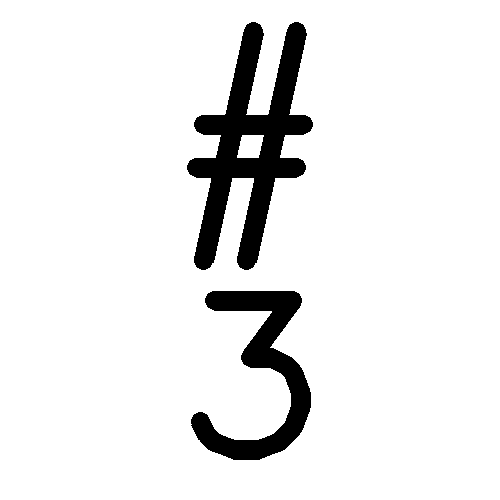
keyboard-labels/keys/3.png
