alnwlsn/wc-80-archive/keyboard-labels/keys/4.png

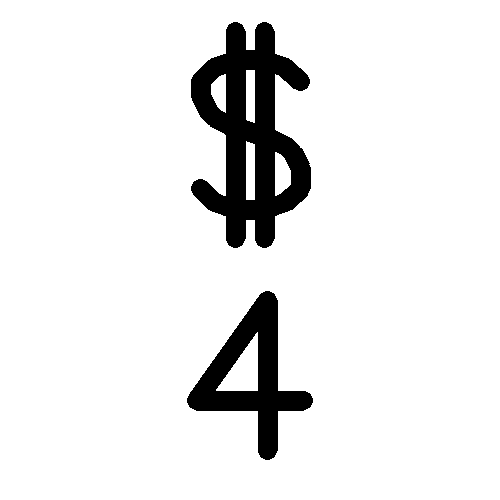
keyboard-labels/keys/4.png
