alnwlsn/wc-80-archive/keyboard-labels/keys/5.png

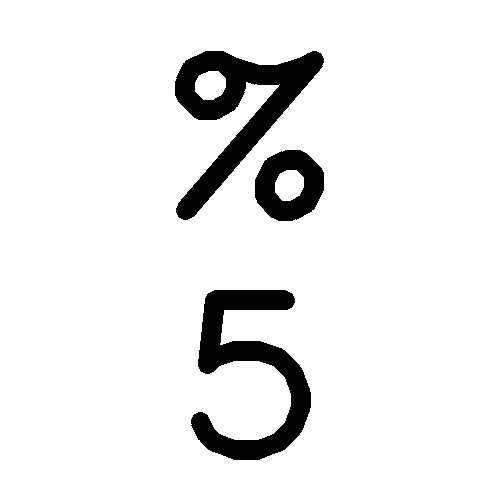
keyboard-labels/keys/5.png
