alnwlsn/wc-80-archive/keyboard-labels/keys/6.png

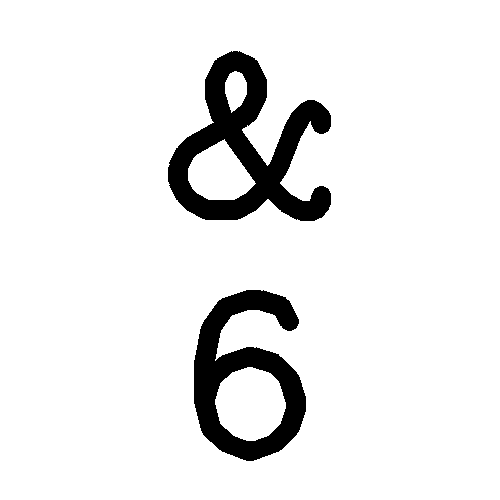
keyboard-labels/keys/6.png
