alnwlsn/wc-80-archive/keyboard-labels/keys/7.png

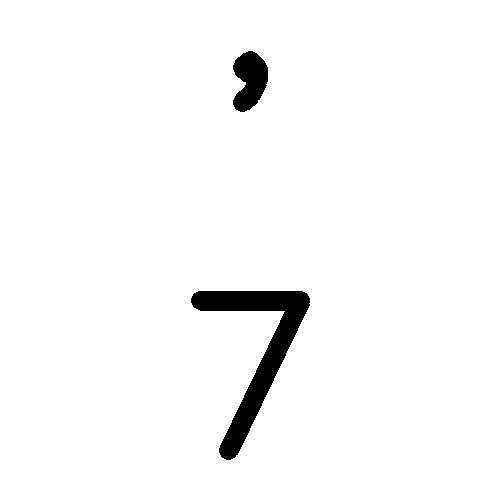
keyboard-labels/keys/7.png
