alnwlsn/wc-80-archive/keyboard-labels/keys/10.png

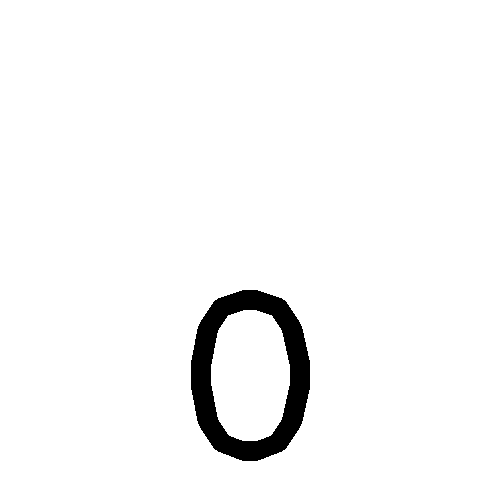
keyboard-labels/keys/10.png
