alnwlsn/wc-80-archive/keyboard-labels/keys/10b.png

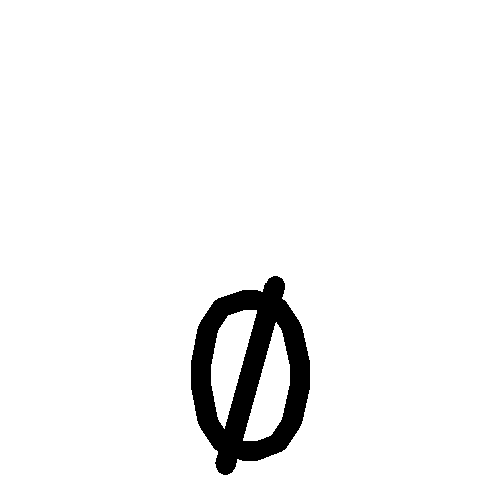
keyboard-labels/keys/10b.png
