alnwlsn/wc-80-archive/keyboard-labels/keys/12.png

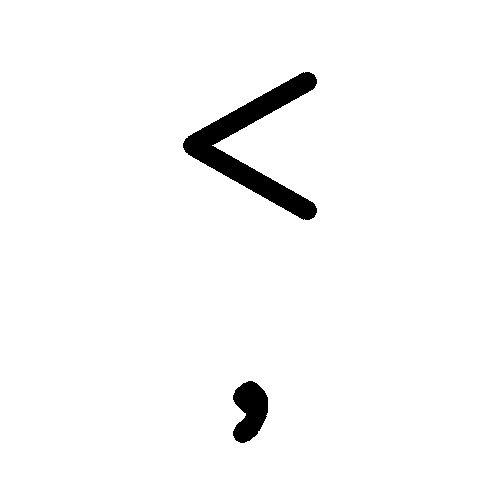
keyboard-labels/keys/12.png
