alnwlsn/wc-80-archive/keyboard-labels/keys/13.png

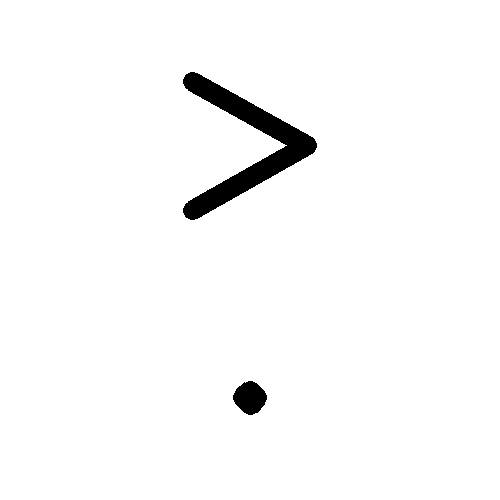
keyboard-labels/keys/13.png
