alnwlsn/wc-80-archive/keyboard-labels/keys/14.png

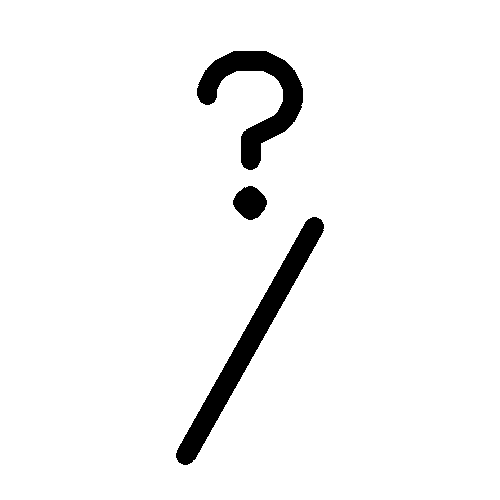
keyboard-labels/keys/14.png
