alnwlsn/wc-80-archive/keyboard-labels/keys/15.png

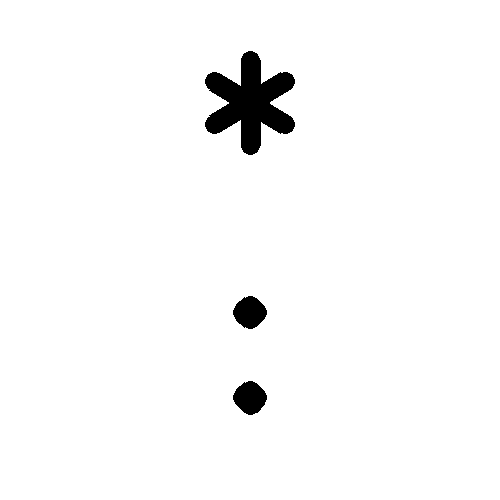
keyboard-labels/keys/15.png
