alnwlsn/wc-80-archive/keyboard-labels/keys/17.png

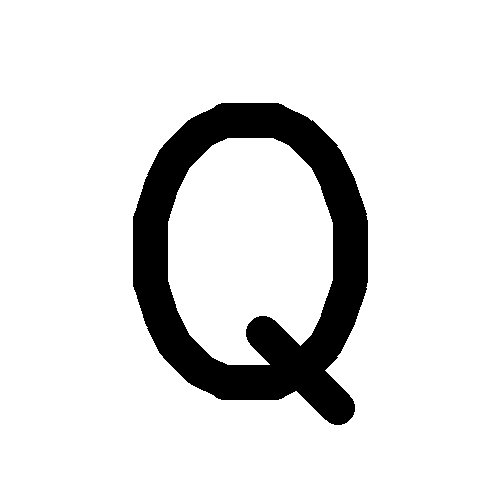
keyboard-labels/keys/17.png
