alnwlsn/wc-80-archive/keyboard-labels/keys/18.png

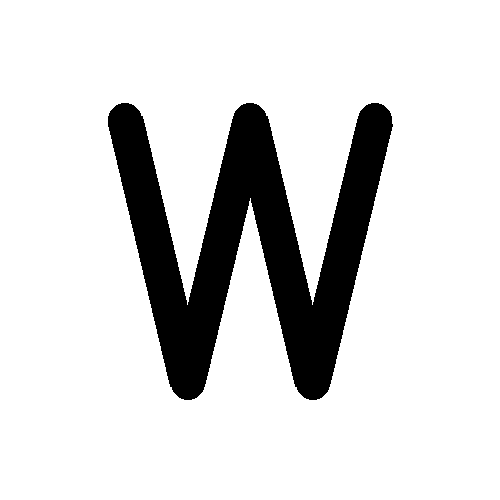
keyboard-labels/keys/18.png
