alnwlsn/wc-80-archive/keyboard-labels/keys/19.png

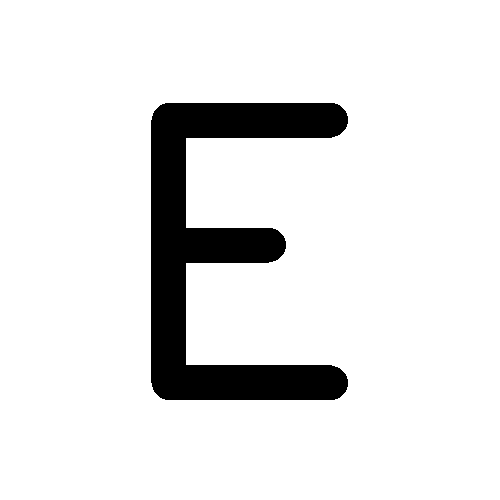
keyboard-labels/keys/19.png
