alnwlsn/wc-80-archive/keyboard-labels/keys/20.png

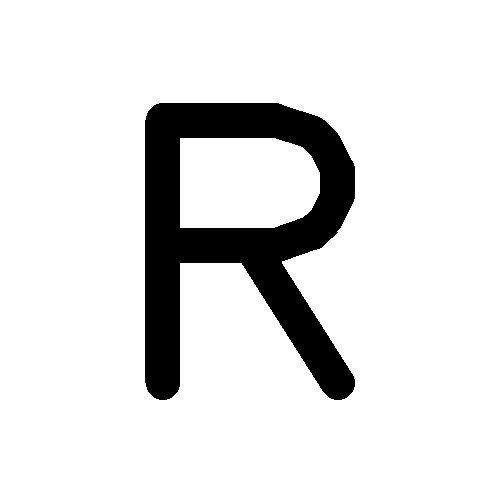
keyboard-labels/keys/20.png
