alnwlsn/wc-80-archive/keyboard-labels/keys/21.png

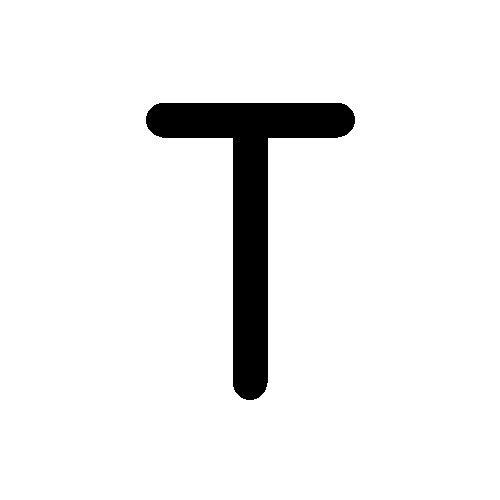
keyboard-labels/keys/21.png
