alnwlsn/wc-80-archive/keyboard-labels/keys/22.png

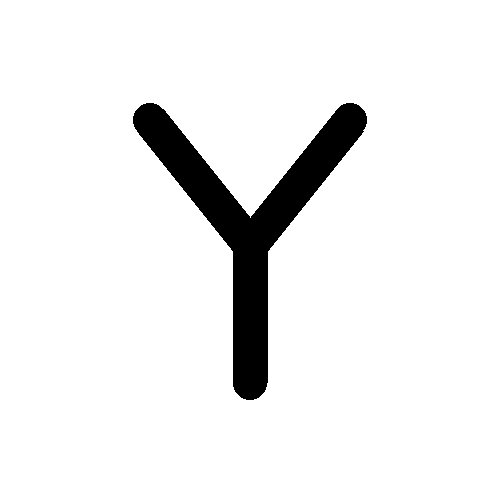
keyboard-labels/keys/22.png
