alnwlsn/wc-80-archive/keyboard-labels/keys/23.png

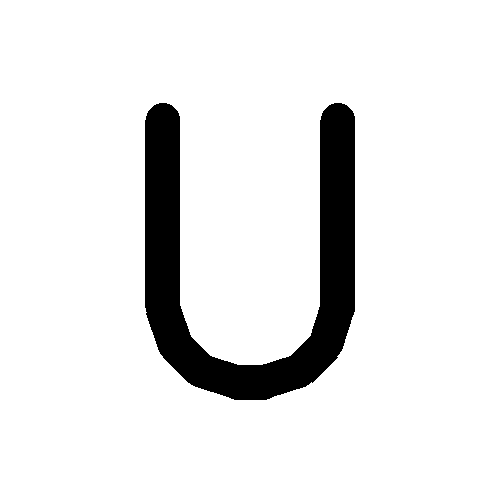
keyboard-labels/keys/23.png
