alnwlsn/wc-80-archive/keyboard-labels/keys/26.png

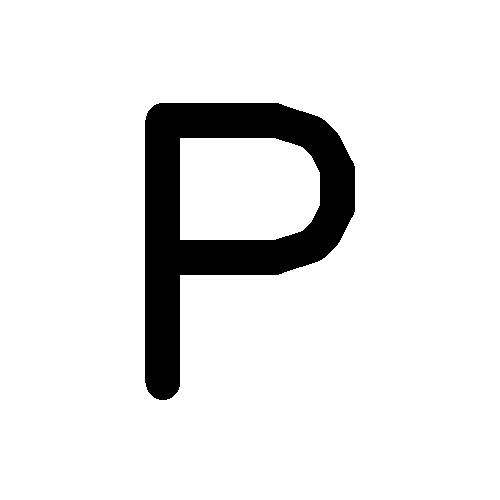
keyboard-labels/keys/26.png
