alnwlsn/wc-80-archive/keyboard-labels/keys/27.png

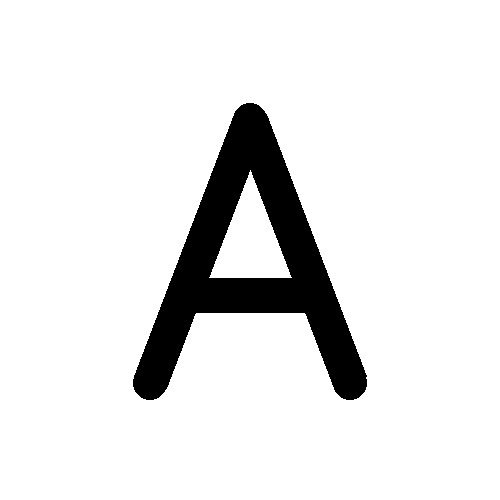
keyboard-labels/keys/27.png
