alnwlsn/wc-80-archive/keyboard-labels/keys/28.png

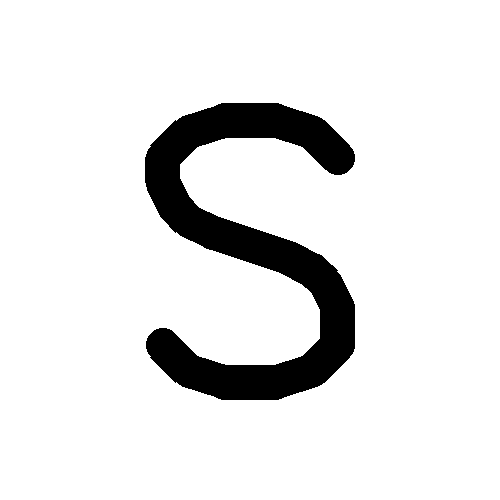
keyboard-labels/keys/28.png
