alnwlsn/wc-80-archive/keyboard-labels/keys/29.png

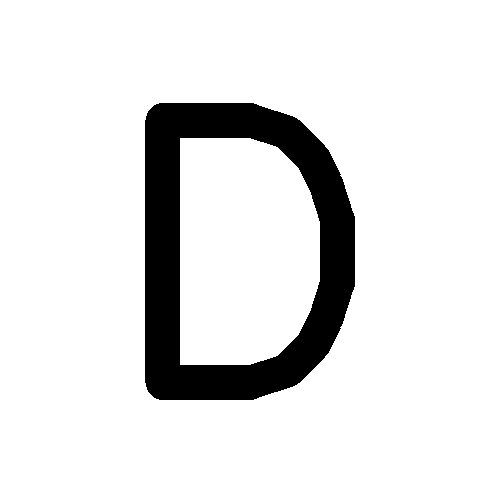
keyboard-labels/keys/29.png
