alnwlsn/wc-80-archive/keyboard-labels/keys/30.png

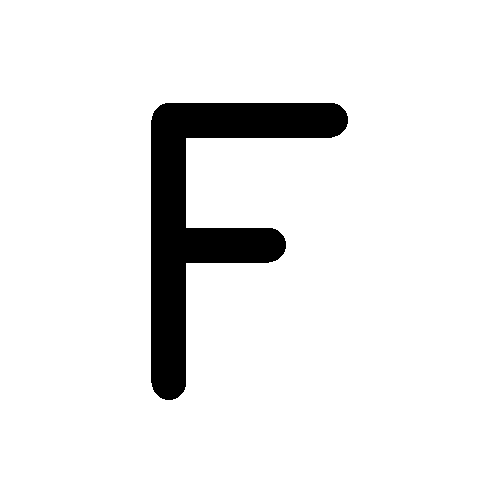
keyboard-labels/keys/30.png
