alnwlsn/wc-80-archive/keyboard-labels/keys/32.png

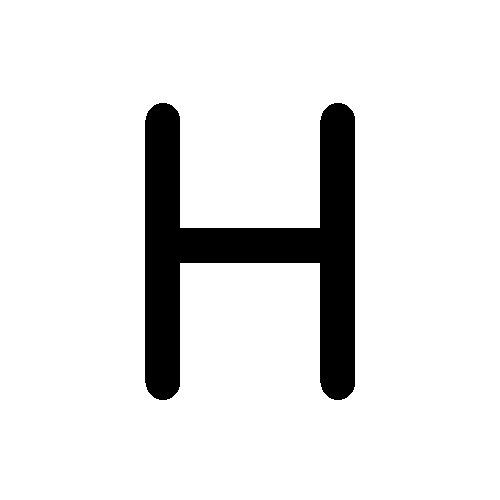
keyboard-labels/keys/32.png
