alnwlsn/wc-80-archive/keyboard-labels/keys/33.png

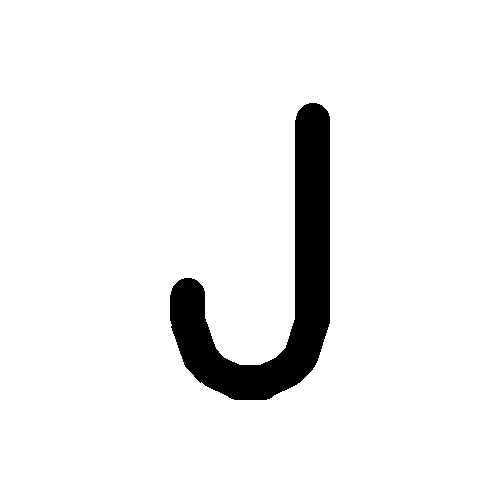
keyboard-labels/keys/33.png
