alnwlsn/wc-80-archive/keyboard-labels/keys/34.png

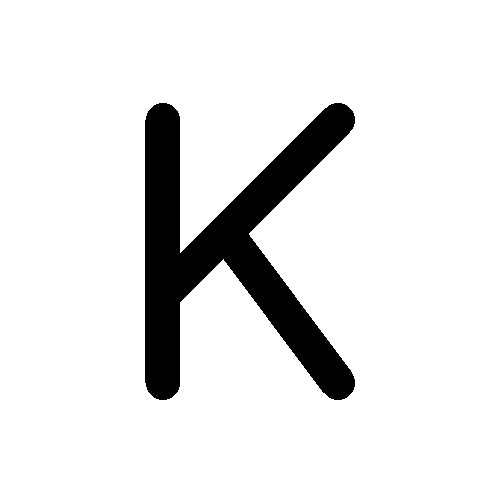
keyboard-labels/keys/34.png
