alnwlsn/wc-80-archive/keyboard-labels/keys/35.png

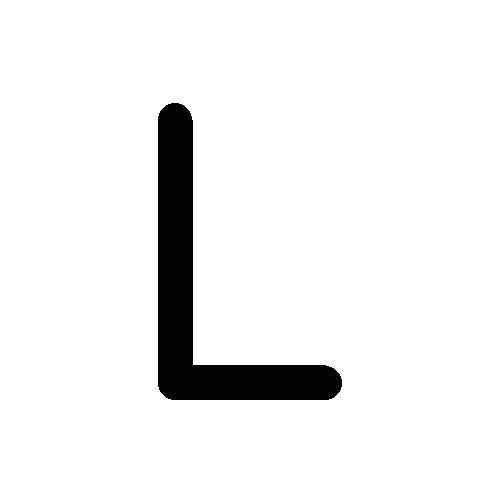
keyboard-labels/keys/35.png
