alnwlsn/wc-80-archive/keyboard-labels/keys/36.png

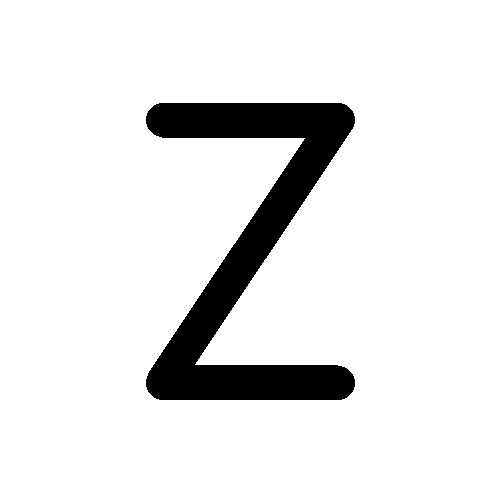
keyboard-labels/keys/36.png
