alnwlsn/wc-80-archive/keyboard-labels/keys/39.png

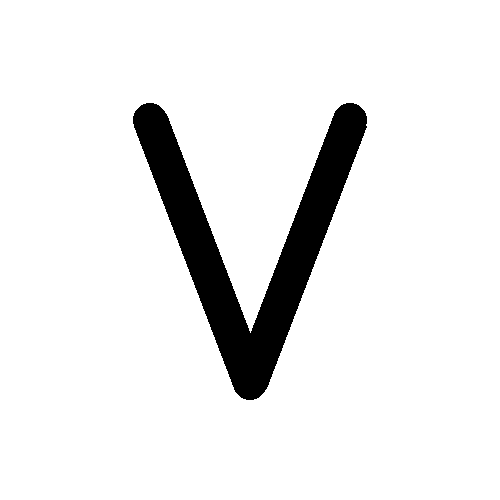
keyboard-labels/keys/39.png
