alnwlsn/wc-80-archive/keyboard-labels/keys/40.png

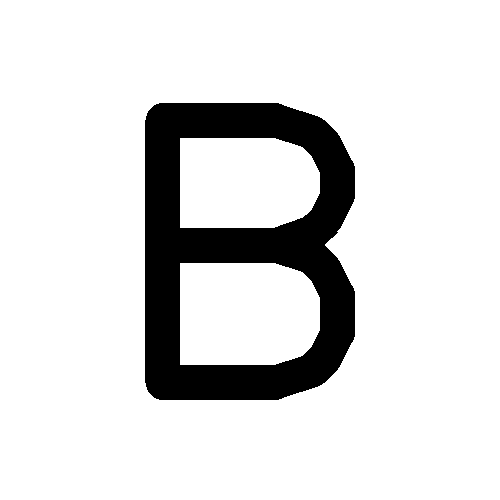
keyboard-labels/keys/40.png
