alnwlsn/wc-80-archive/keyboard-labels/keys/41.png

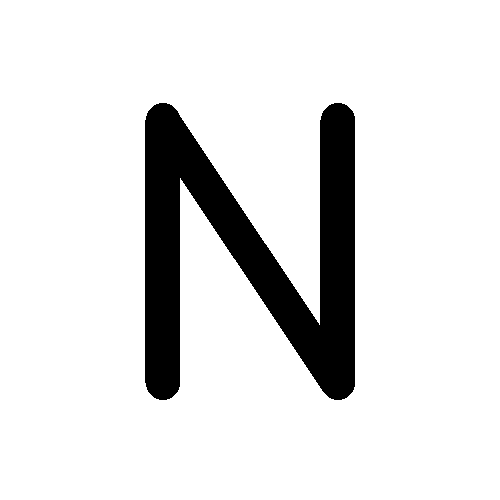
keyboard-labels/keys/41.png
