alnwlsn/wc-80-archive/keyboard-labels/keys/42.png

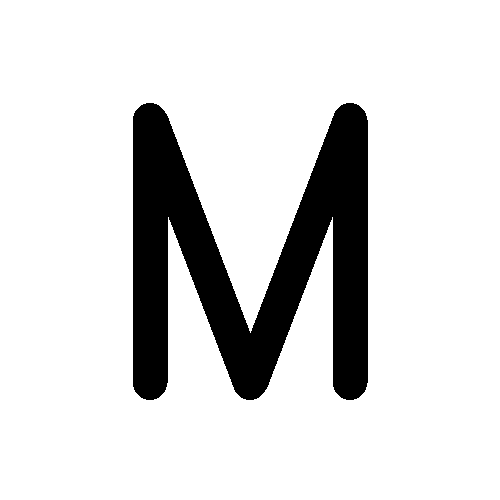
keyboard-labels/keys/42.png
