alnwlsn/wc-80-archive/keyboard-labels/keys/43.png

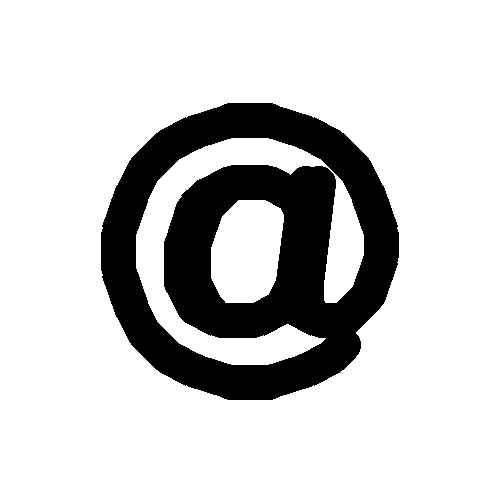
keyboard-labels/keys/43.png
