alnwlsn/wc-80-archive/keyboard-labels/keys/44.png

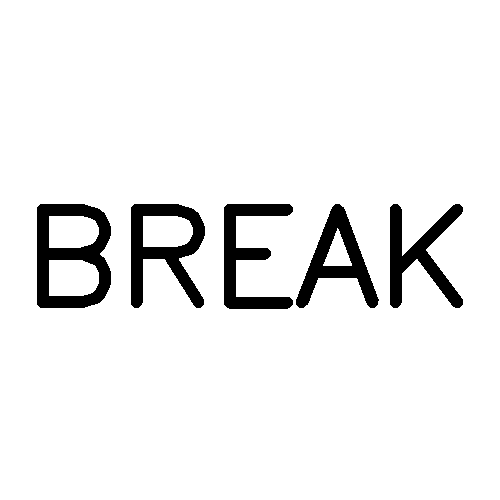
keyboard-labels/keys/44.png
