alnwlsn/wc-80-archive/keyboard-labels/keys/47.png

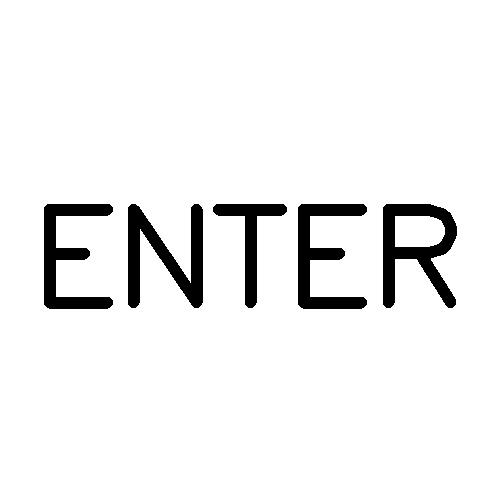
keyboard-labels/keys/47.png
