alnwlsn/wc-80-archive/keyboard-labels/keys/48.png

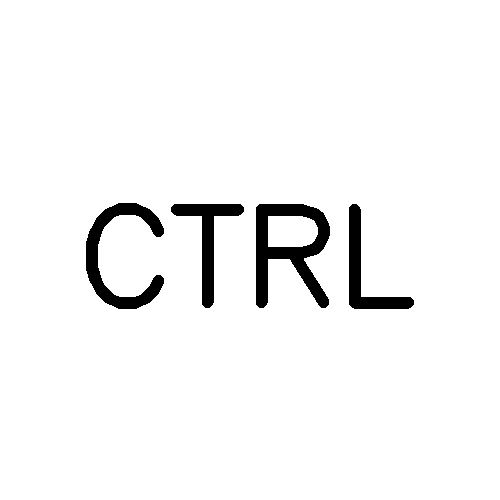
keyboard-labels/keys/48.png
