alnwlsn/wc-80-archive/keyboard-labels/keys/49.png

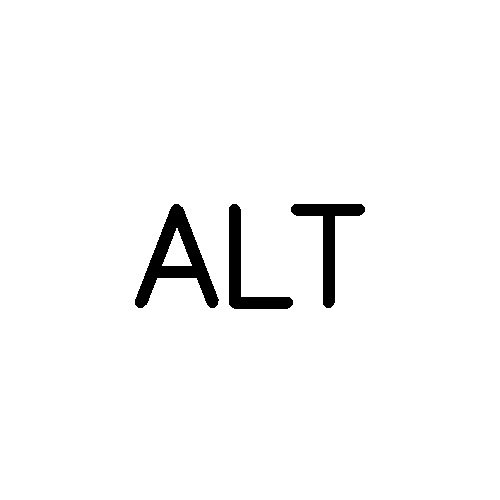
keyboard-labels/keys/49.png
