alnwlsn/wc-80-archive/keyboard-labels/keys/50.png

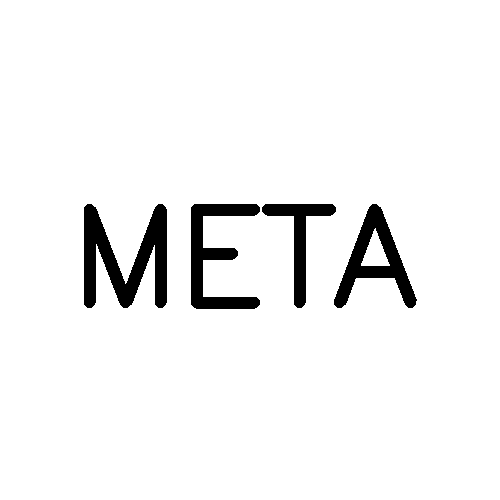
keyboard-labels/keys/50.png
