alnwlsn/wc-80-archive/keyboard-labels/keys/51.png

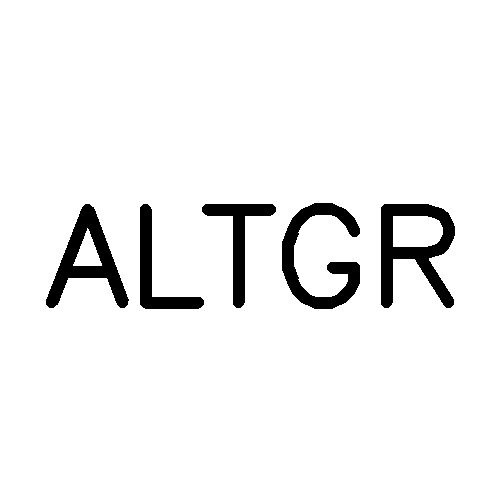
keyboard-labels/keys/51.png
