alnwlsn/wc-80-archive/keyboard-labels/keys/52.png

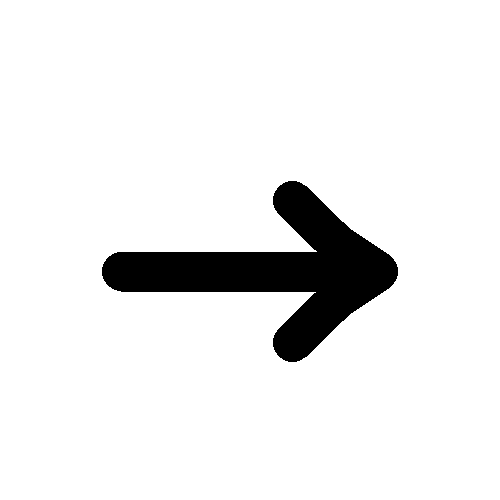
keyboard-labels/keys/52.png
