alnwlsn/wc-80-archive/keyboard-labels/keys/53.png

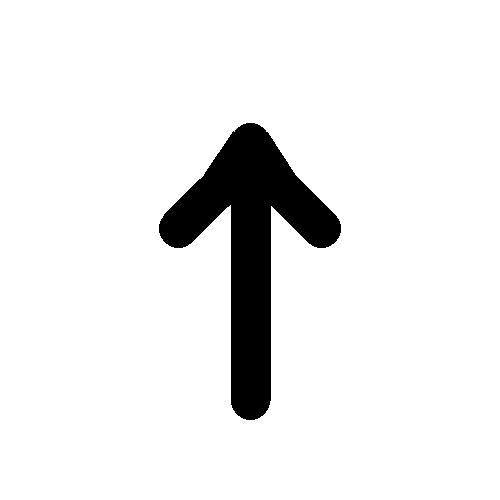
keyboard-labels/keys/53.png
