alnwlsn/wc-80-archive/keyboard-labels/keys/54.png

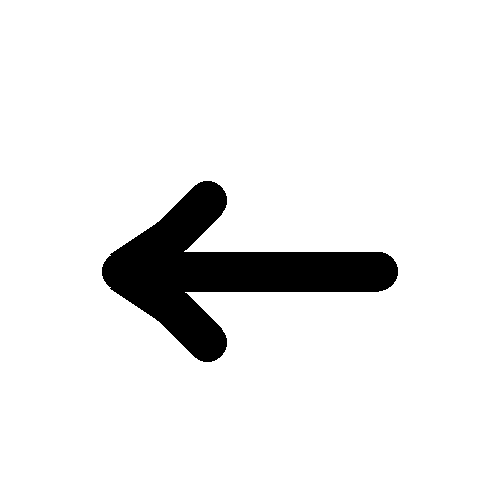
keyboard-labels/keys/54.png
