alnwlsn/wc-80-archive/keyboard-labels/keys/55.png

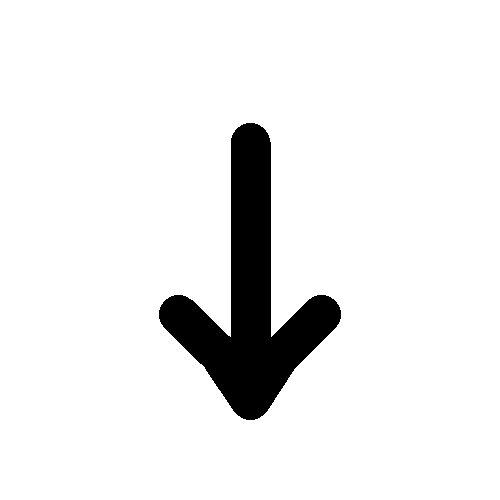
keyboard-labels/keys/55.png
