alnwlsn/wc-80-archive/keyboard-labels/keys/56.png

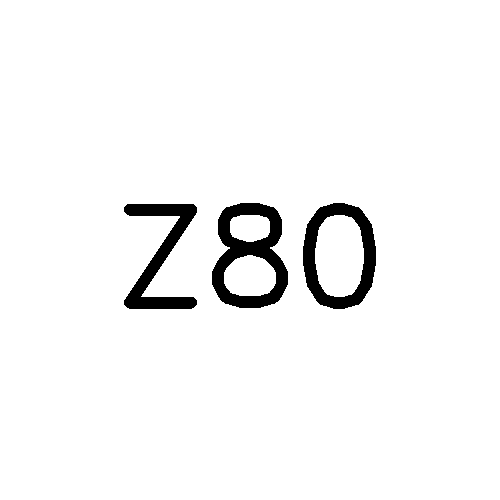
keyboard-labels/keys/56.png
