alnwlsn/wc-80-archive/keyboard-labels/keys/58.png

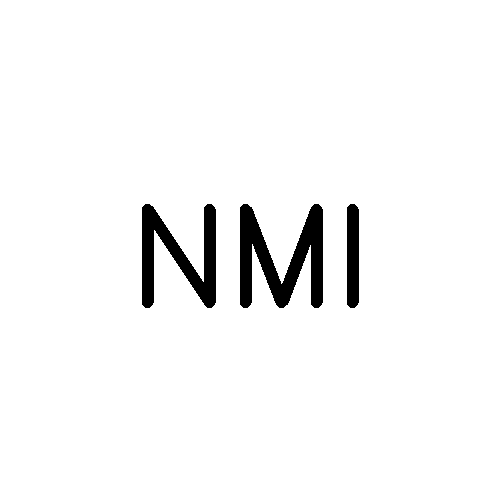
keyboard-labels/keys/58.png
