alnwlsn/wc-80-archive/keyboard-labels/keys/59.png

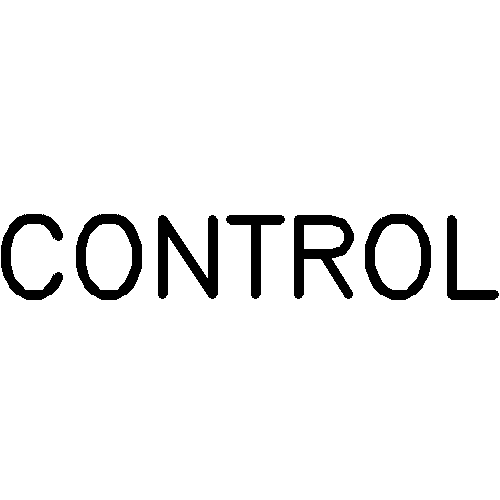
keyboard-labels/keys/59.png
