alnwlsn/wc-80-archive/keyboard-labels/keys/target.png

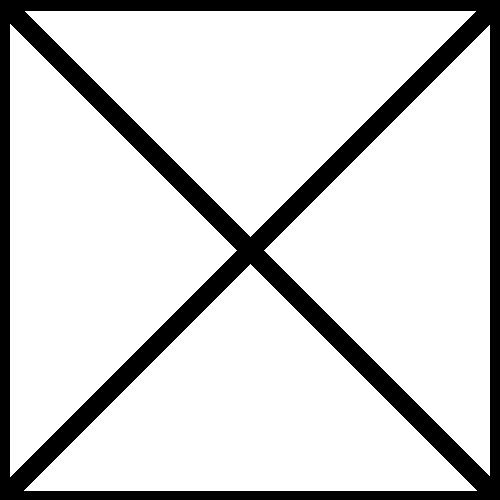
keyboard-labels/keys/target.png
