alnwlsn/wc-80-archive/boards/arduino/0old/rev1/main.kicad_pcb

## KiCad design boards/arduino/0old/rev1/main.kicad_pcb (2025-07-11, an earlier design)

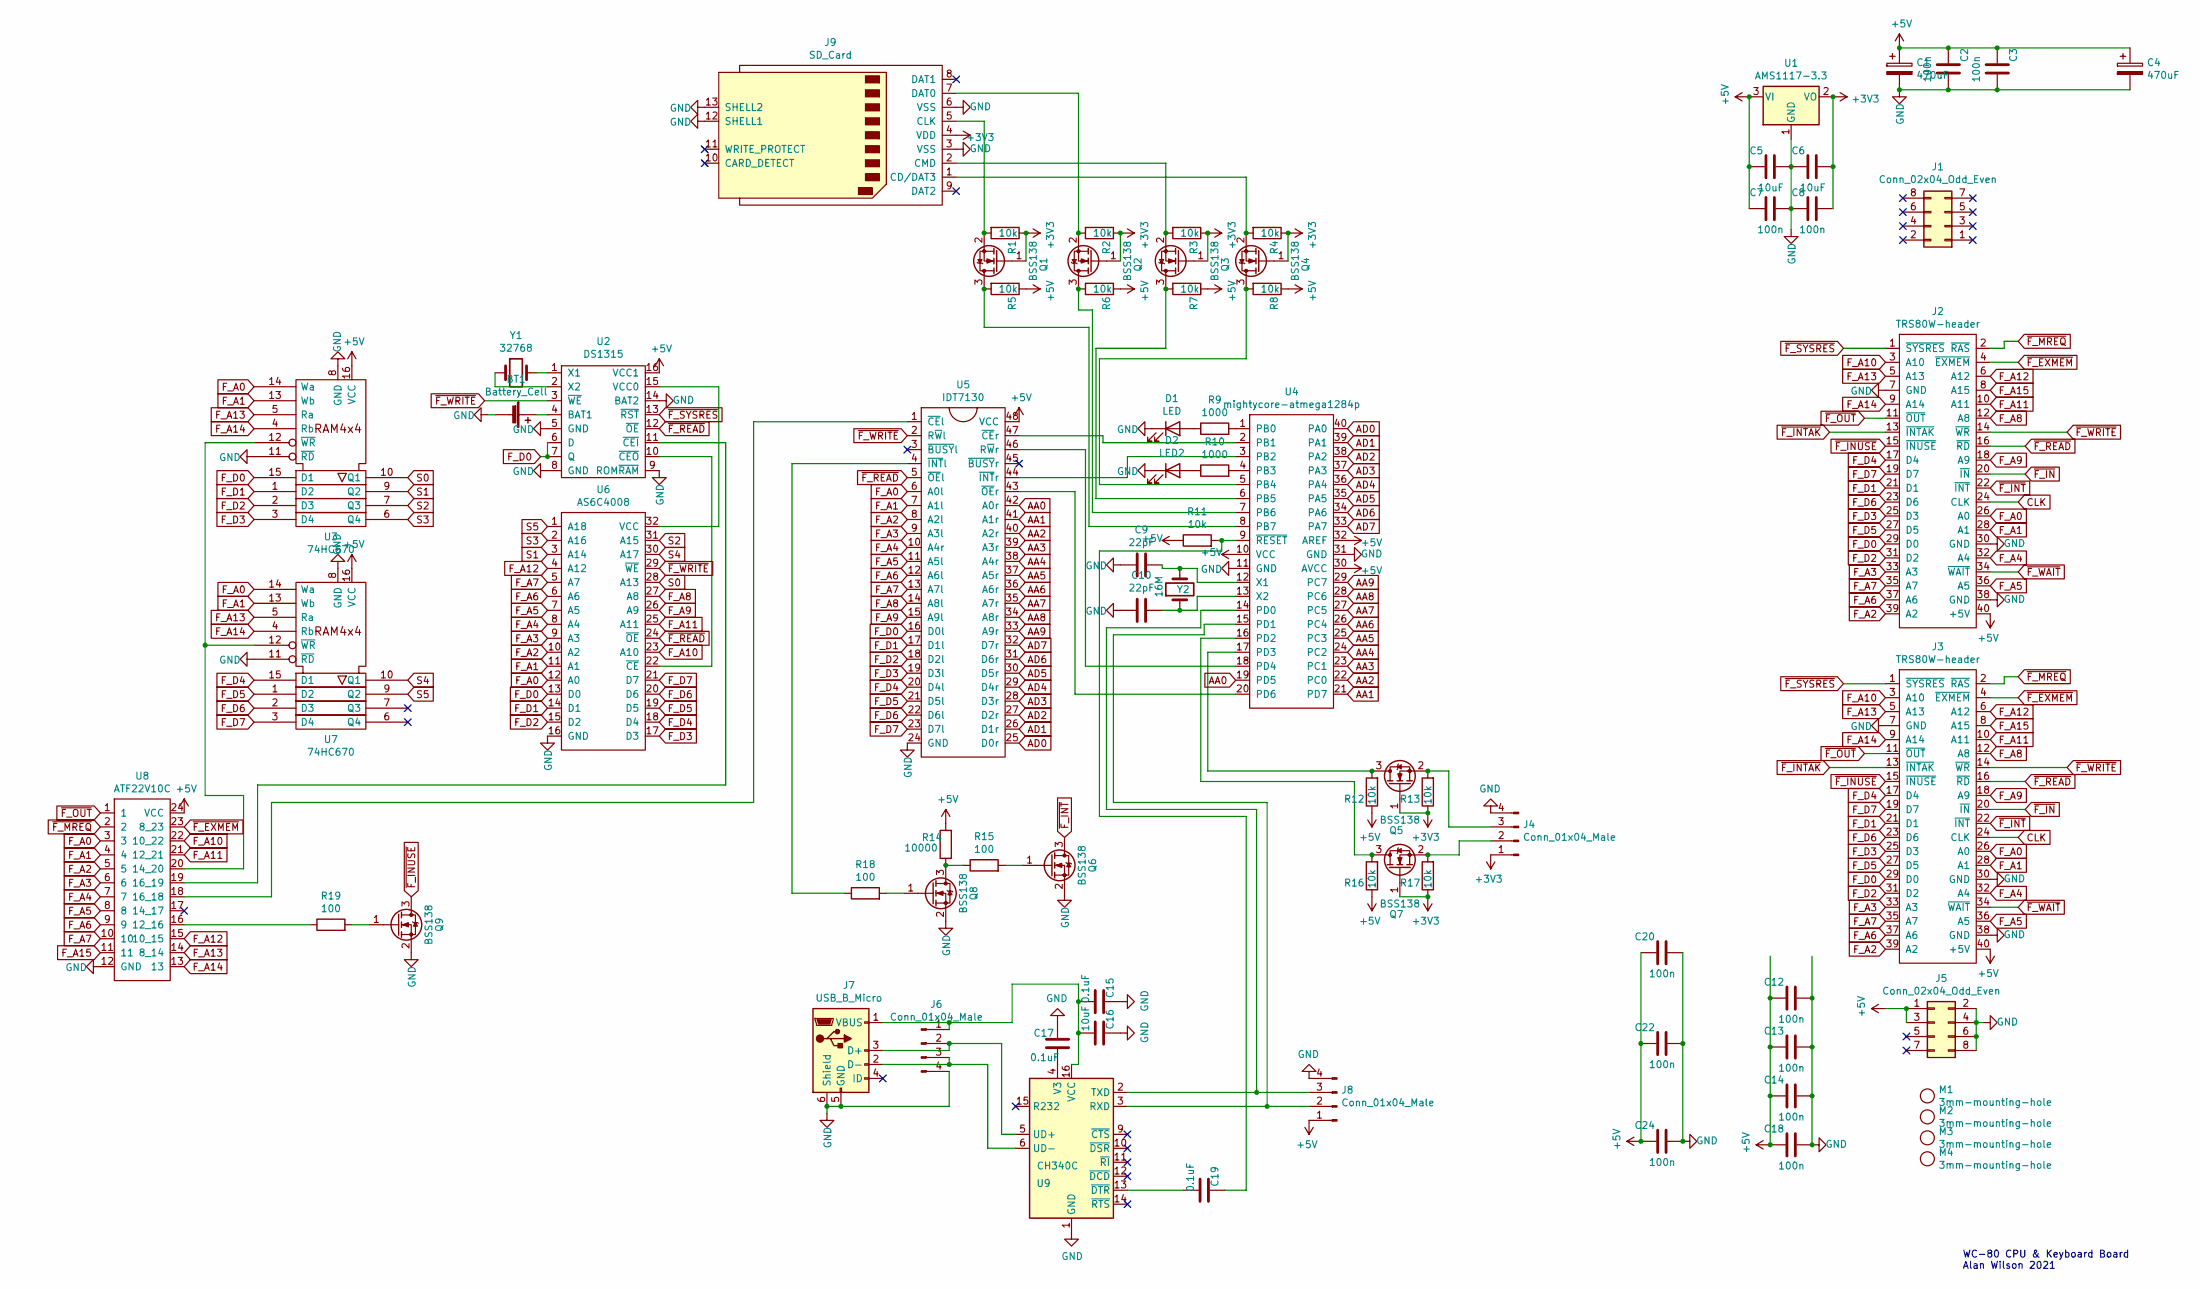
[picture p93: schematic main.sch]

Parts:
BT1: Battery_Cell; BS-01-A4CJ004
C1, C4: 470uF; CP_Radial_D8.0mm_P3.50mm
C2, C3, C7, C8, C12, C13, C14, C18, C20, C22, C24: 100n; C_0805_2012Metric
C5, C6, C16: 10uF; C_0805_2012Metric
C9, C10: 22pF; C_0805_2012Metric
C15, C17, C19: 0.1uF; C_0805_2012Metric
D1: LED; LED_D3.0mm
D2: LED2; LED_D3.0mm
J1, J5: Conn_02x04_Odd_Even; PinHeader_2x04_P2.54mm_Vertical
J2, J3: TRS80W-header; PinHeader_2x20_P2.54mm_Vertical
J4, J6, J8: Conn_01x04_Male; PinHeader_1x04_P2.54mm_Vertical
J7: USB_B_Micro; USB_Micro-B_Molex-105017-0001
J9: SD_Card; SD_Card_ XUNPU_SD-101
M1, M2, M3, M4: 3mm-mounting-hole; MountingHole_3.2mm_M3_DIN965
Q1, Q2, Q3, Q4, Q5, Q6, Q7, Q8, Q9: BSS138; SOT-23
R1, R2, R3, R4, R5, R6, R7, R8, R11, R12, R13, R16, R17: 10k; R_0805_2012Metric
R9, R10: 1000; R_0805_2012Metric
R14: 10000; R_0805_2012Metric
R15, R18, R19: 100; R_0805_2012Metric
U1: AMS1117-3.3; SOT-223-3_TabPin2
U2: DS1315; DIP-16_W7.62mm_Socket
U3, U7: 74HC670; DIP-16_W7.62mm_Socket
U4: mightycore-atmega1284p; DIP-40_W15.24mm_Socket
U5: IDT7130; DIP-48_W15.24mm_Socket
U6: AS6C4008; DIP-32_W15.24mm
U8: ATF22V10C; DIP-24_W7.62mm
U9: CH340C; SOIC-16_3.9x9.9mm_P1.27mm
Y1: 32768; Crystal_AT310_D3.0mm_L10.0mm_Horizontal
Y2: 16M; Crystal_HC49-U_Vertical

Connections:
+3V3: C6.2, C8.2, J4.1, J9.4 (VDD), Q1.1 (G), Q2.1 (G), Q3.1 (G), Q4.1 (G), Q5.1 (G), Q7.1 (G), R1.1, R2.1, R3.1, R4.1, R13.1, R17.1, U1.2 (VO)
+5V: C1.1, C2.1, C3.1, C4.1, C5.1, C7.1, C12.1, C13.1, C14.1, C18.1, C20.1, C22.1, C24.1, J2.40 (+5V), J3.40 (+5V), J5.1, J5.3, J8.1, R5.1, R6.1, R7.1, R8.1, R11.1, R12.1, R14.2, R16.1, U1.3 (VI), U2.16 (VCC1), U3.16 (VCC), U4.10 (VCC), U4.30 (AVCC), U4.32 (AREF), U5.48 (VCC), U7.16 (VCC), U8.24 (VCC)
AA0: U4.19 (PD5), U5.42 (A0r)
AA1: U4.21 (PD7), U5.41 (A1r)
AA2: U4.22 (PC0), U5.40 (A2r)
AA3: U4.23 (PC1), U5.39 (A3r)
AA4: U4.24 (PC2), U5.38 (A4r)
AA5: U4.25 (PC3), U5.37 (A5r)
AA6: U4.26 (PC4), U5.36 (A6r)
AA7: U4.27 (PC5), U5.35 (A7r)
AA8: U4.28 (PC6), U5.34 (A8r)
AA9: U4.29 (PC7), U5.33 (A9r)
AD0: U4.40 (PA0), U5.25 (D0r)
AD1: U4.39 (PA1), U5.26 (D1r)
AD2: U4.38 (PA2), U5.27 (D2r)
AD3: U4.37 (PA3), U5.28 (D3r)
AD4: U4.36 (PA4), U5.29 (D4r)
AD5: U4.35 (PA5), U5.30 (D5r)
AD6: U4.34 (PA6), U5.31 (D6r)
AD7: U4.33 (PA7), U5.32 (D7r)
CLK: J2.24 (CLK), J3.24 (CLK)
F_A0: J2.26 (A0), J3.26 (A0), U3.14 (Wa), U5.6 (A0l), U6.12 (A0), U7.14 (Wa), U8.3
F_A1: J2.28 (A1), J3.28 (A1), U3.13 (Wb), U5.7 (A1l), U6.11 (A1), U7.13 (Wb), U8.4
F_A2: J2.39 (A2), J3.39 (A2), U5.8 (A2l), U6.10 (A2), U8.5
F_A3: J2.33 (A3), J3.33 (A3), U5.9 (A3l), U6.9 (A3), U8.6
F_A4: J2.32 (A4), J3.32 (A4), U5.10 (A4r), U6.8 (A4), U8.7
F_A5: J2.36 (A5), J3.36 (A5), U5.11 (A5l), U6.7 (A5), U8.8
F_A6: J2.37 (A6), J3.37 (A6), U5.12 (A6l), U6.6 (A6), U8.9
F_A7: J2.35 (A7), J3.35 (A7), U5.13 (A7l), U6.5 (A7), U8.10
F_A8: J2.12 (A8), J3.12 (A8), U5.14 (A8l), U6.27 (A8)
F_A9: J2.18 (A9), J3.18 (A9), U5.15 (A9l), U6.26 (A9)
F_A10: J2.3 (A10), J3.3 (A10), U6.23 (A10), U8.22 (10_22)
F_A11: J2.10 (A11), J3.10 (A11), U6.25 (A11), U8.21 (12_21)
F_A12: J2.6 (A12), J3.6 (A12), U6.4 (A12), U8.15 (10_15)
F_A13: J2.5 (A13), J3.5 (A13), U3.5 (Ra), U7.5 (Ra), U8.14 (8_14)
F_A14: J2.9 (A14), J3.9 (A14), U3.4 (Rb), U7.4 (Rb), U8.13
F_A15: J2.8 (A15), J3.8 (A15), U8.11
F_D0: J2.29 (D0), J3.29 (D0), U2.6 (D), U2.7 (Q), U3.15 (D1), U5.16 (D0l), U6.13 (D0)
F_D1: J2.21 (D1), J3.21 (D1), U3.1 (D2), U5.17 (D1l), U6.14 (D1)
F_D2: J2.31 (D2), J3.31 (D2), U3.2 (D3), U5.18 (D2l), U6.15 (D2)
F_D3: J2.25 (D3), J3.25 (D3), U3.3 (D4), U5.19 (D3l), U6.17 (D3)
F_D4: J2.17 (D4), J3.17 (D4), U5.20 (D4l), U6.18 (D4), U7.15 (D1)
F_D5: J2.27 (D5), J3.27 (D5), U5.21 (D5l), U6.19 (D5), U7.1 (D2)
F_D6: J2.23 (D6), J3.23 (D6), U5.22 (D6l), U6.20 (D6), U7.2 (D3)
F_D7: J2.19 (D7), J3.19 (D7), U5.23 (D7l), U6.21 (D7), U7.3 (D4)
GND: BT1.2 (-), C1.2, C2.2, C3.2, C4.2, C5.2, C6.1, C7.2, C8.1, C9.2, C10.2, C12.2, C13.2, C14.2, C15.2, C16.2, C17.2, C18.2, C20.2, C22.2, C24.2, D1.1 (K), D2.1 (K), J2.7 (GND), J2.30 (GND), J2.38 (GND), J3.7 (GND), J3.30 (GND), J3.38 (GND), J4.4, J5.2, J5.4, J5.6, J5.8, J6.4, J7.5 (GND), J7.6 (Shield), J8.4, J9.3 (VSS), J9.6 (VSS), J9.12 (SHELL1), J9.13 (SHELL2), Q6.2 (S), Q8.2 (S), Q9.2 (S), U1.1 (GND), U2.5 (GND), U2.8 (GND), U2.9 (ROM~RAM~), U2.14 (BAT2), U3.8 (GND), U3.11 (~RD), U4.11 (GND), U4.31 (GND), U5.24 (GND), U6.16 (GND), U7.8 (GND), U7.11 (~RD), U8.12 (GND), U9.1 (GND)
unnamed: BT1.1 (+), U2.4 (BAT1)
unnamed: C9.1, U4.12 (X1), Y2.2
unnamed: C10.1, U4.13 (X2), Y2.1
unnamed: C15.1, C16.1, J6.1, J7.1 (VBUS), U9.16 (VCC)
unnamed: C17.1, U9.4 (V3)
unnamed: C19.1, U9.13 (~DTR)
unnamed: C19.2, R11.2, U4.9 (~RESET~)
unnamed: D1.2 (A), R9.1
unnamed: D2.2 (A), R10.1
unnamed: J4.2, Q7.2 (S), R17.2
unnamed: J4.3, Q5.2 (S), R13.2
unnamed: J6.2, J7.3 (D+), U9.5 (UD+)
unnamed: J6.3, J7.2 (D-), U9.6 (UD-)
unnamed: J8.2, U4.15 (PD1), U9.3 (RXD)
unnamed: J8.3, U4.14 (PD0), U9.2 (TXD)
unnamed: J9.1 (CD/DAT3), Q4.2 (S), R4.2
unnamed: J9.2 (CMD), Q3.2 (S), R3.2
unnamed: J9.5 (CLK), Q1.2 (S), R1.2
unnamed: J9.7 (DAT0), Q2.2 (S), R2.2
unnamed: Q1.3 (D), R5.2, U4.8 (PB7)
unnamed: Q2.3 (D), R6.2, U4.7 (PB6)
unnamed: Q3.3 (D), R7.2, U4.6 (PB5)
unnamed: Q4.3 (D), R8.2, U4.5 (PB4)
unnamed: Q5.3 (D), R12.2, U4.17 (PD3)
unnamed: Q6.1 (G), R15.2
unnamed: Q7.3 (D), R16.2, U4.16 (PD2)
unnamed: Q8.1 (G), R18.2
unnamed: Q8.3 (D), R14.1, R15.1
unnamed: Q9.1 (G), R19.2
unnamed: R9.2, U4.1 (PB0)
unnamed: R10.2, U4.4 (PB3)
unnamed: R18.1, U5.4 (~INT~l)
unnamed: R19.1, U8.16 (12_16)
unnamed: U2.1 (X1), Y1.2
unnamed: U2.2 (X2), Y1.1
unnamed: U2.10 (~CEO~), U6.22 (~CE~)
unnamed: U2.11 (~CEI~), U8.19 (16_19)
unnamed: U2.15 (VCC0), U6.32 (VCC)
unnamed: U3.12 (~WR), U7.12 (~WR), U8.20 (14_20)
unnamed: U4.2 (PB1), U5.47 (~CE~r)
unnamed: U4.3 (PB2), U5.44 (~INT~r)
unnamed: U4.18 (PD4), U5.46 (R~W~r)
unnamed: U4.20 (PD6), U5.43 (~OE~r)
unnamed: U5.1 (~CE~l), U8.18 (16_18)
S0: U3.10 (Q1), U6.28 (A13)
S1: U3.9 (Q2), U6.3 (A14)
S2: U3.7 (Q3), U6.31 (A15)
S3: U3.6 (Q4), U6.2 (A16)
S4: U6.30 (A17), U7.10 (Q1)
S5: U6.1 (A18), U7.9 (Q2)
~F_EXMEM~: J2.4 (~EXMEM~), J3.4 (~EXMEM~), U8.23 (8_23)
~F_INTAK~: J2.13 (~INTAK~), J3.13 (~INTAK~)
~F_INT~: J2.22 (~INT~), J3.22 (~INT~), Q6.3 (D)
~F_INUSE~: J2.15 (~INUSE~), J3.15 (~INUSE~), Q9.3 (D)
~F_IN~: J2.20 (~IN~), J3.20 (~IN~)
~F_MREQ~: J2.2 (~RAS~), J3.2 (~RAS~), U8.2
~F_OUT~: J2.11 (~OUT~), J3.11 (~OUT~), U8.1
~F_READ~: J2.16 (~RD~), J3.16 (~RD~), U2.12 (~OE~), U5.5 (~OE~l), U6.24 (~OE~)
~F_SYSRES~: J2.1 (~SYSRES~), J3.1 (~SYSRES~), U2.13 (~RST~)
~F_WAIT~: J2.34 (~WAIT~), J3.34 (~WAIT~)
~F_WRITE~: J2.14 (~WR~), J3.14 (~WR~), U2.3 (~WE~), U5.2 (R~W~l), U6.29 (~WE~)

Notes on the sheet:
WC-80 CPU & Keyboard Board Alan Wilson 2021

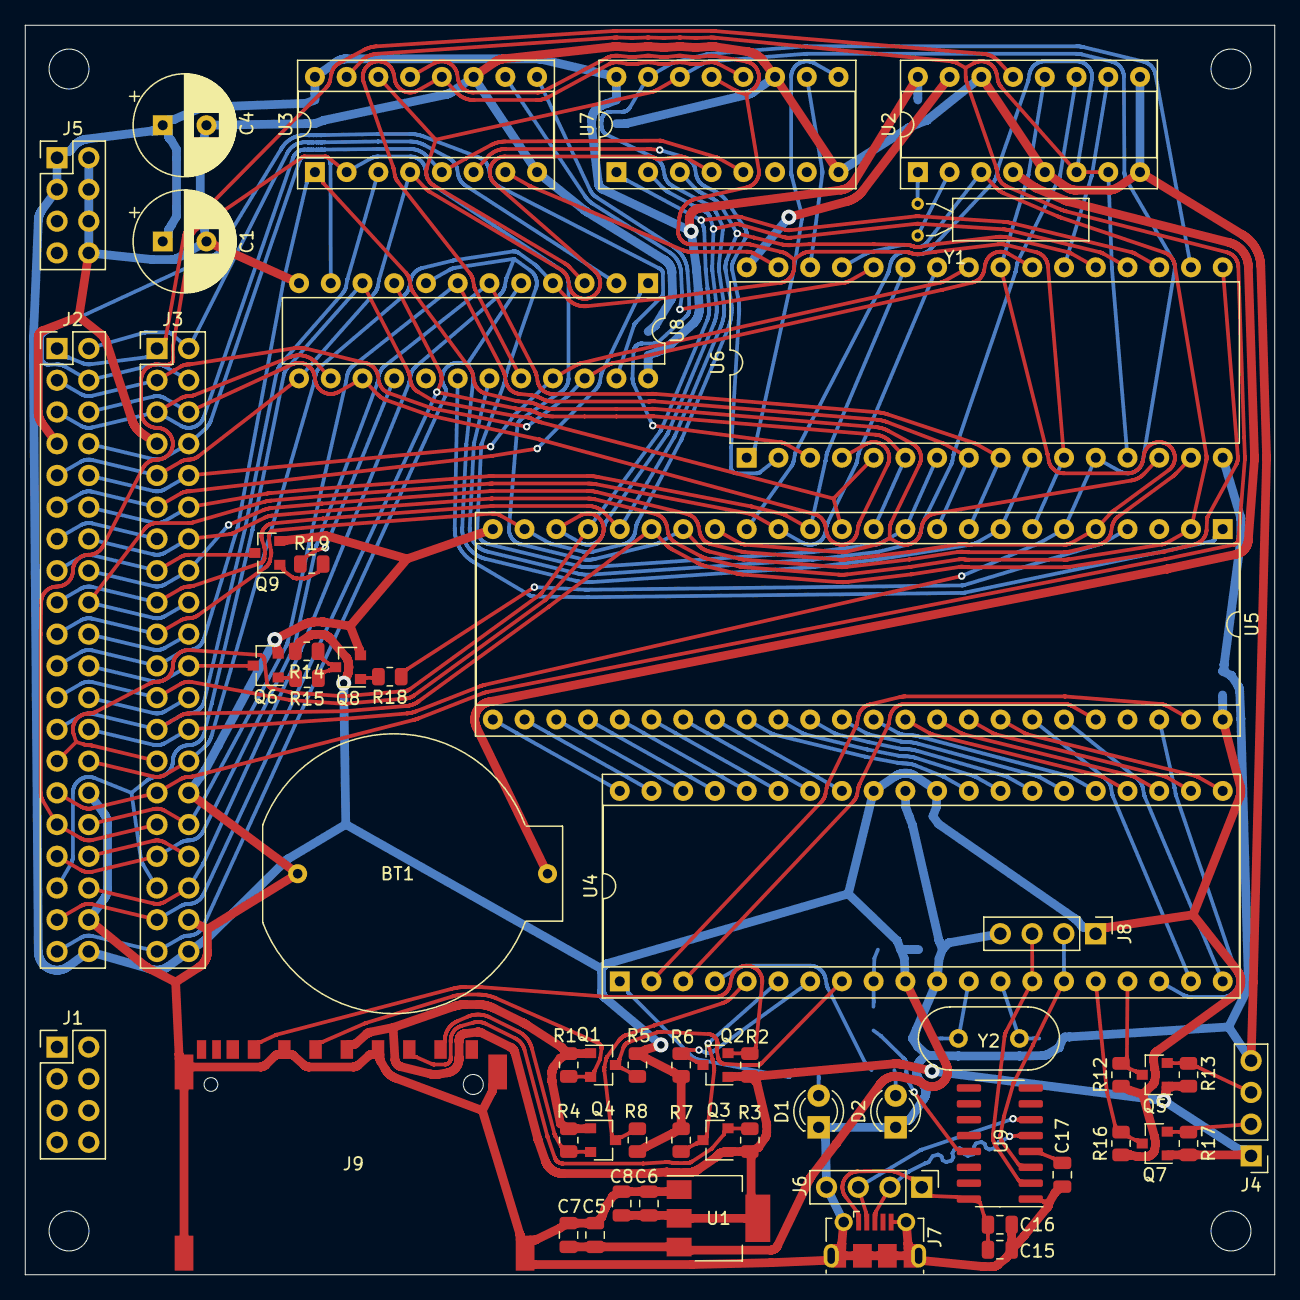
[picture p94: board boards/arduino/0old/rev1/main.kicad_pcb from above]

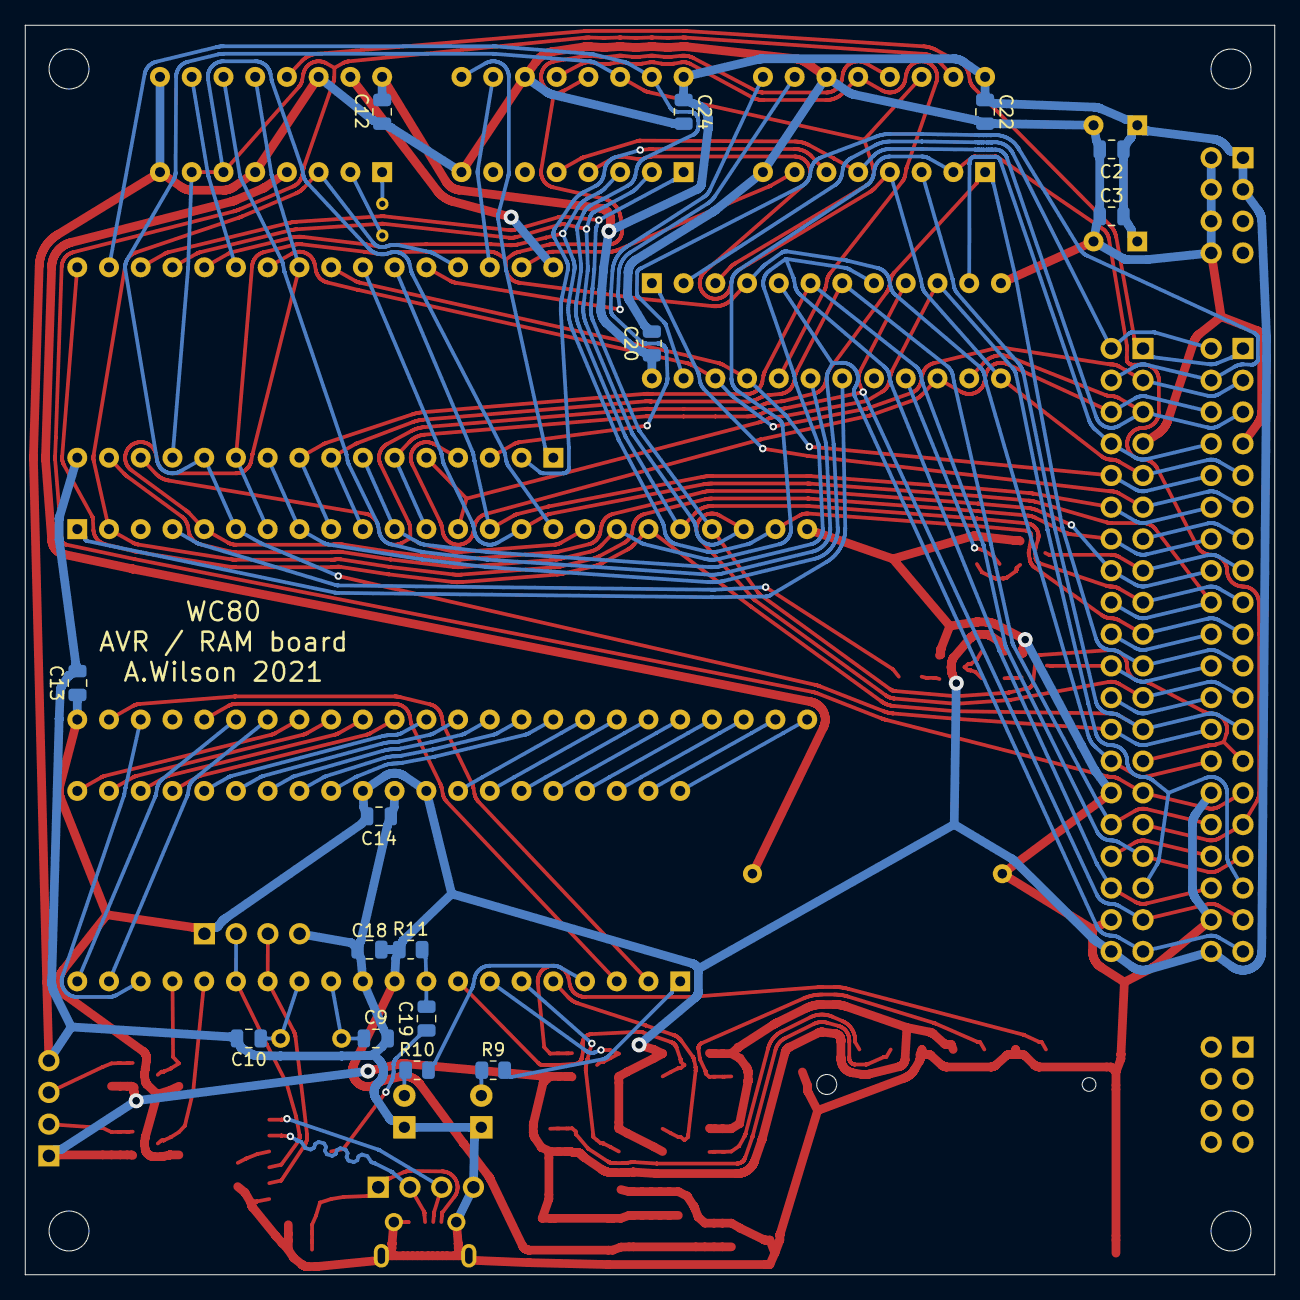
[picture p95: board boards/arduino/0old/rev1/main.kicad_pcb from below]

Board: 2 copper layers, 100.0 x 100.0 mm, 76 parts (15 on the bottom side), 107 nets.
