alnwlsn/wc-80-archive/boards/0old/cpu4/cpu2/cpu2.kicad_pcb

## KiCad design boards/0old/cpu4/cpu2/cpu2.kicad_pcb (2025-07-11, an earlier design)

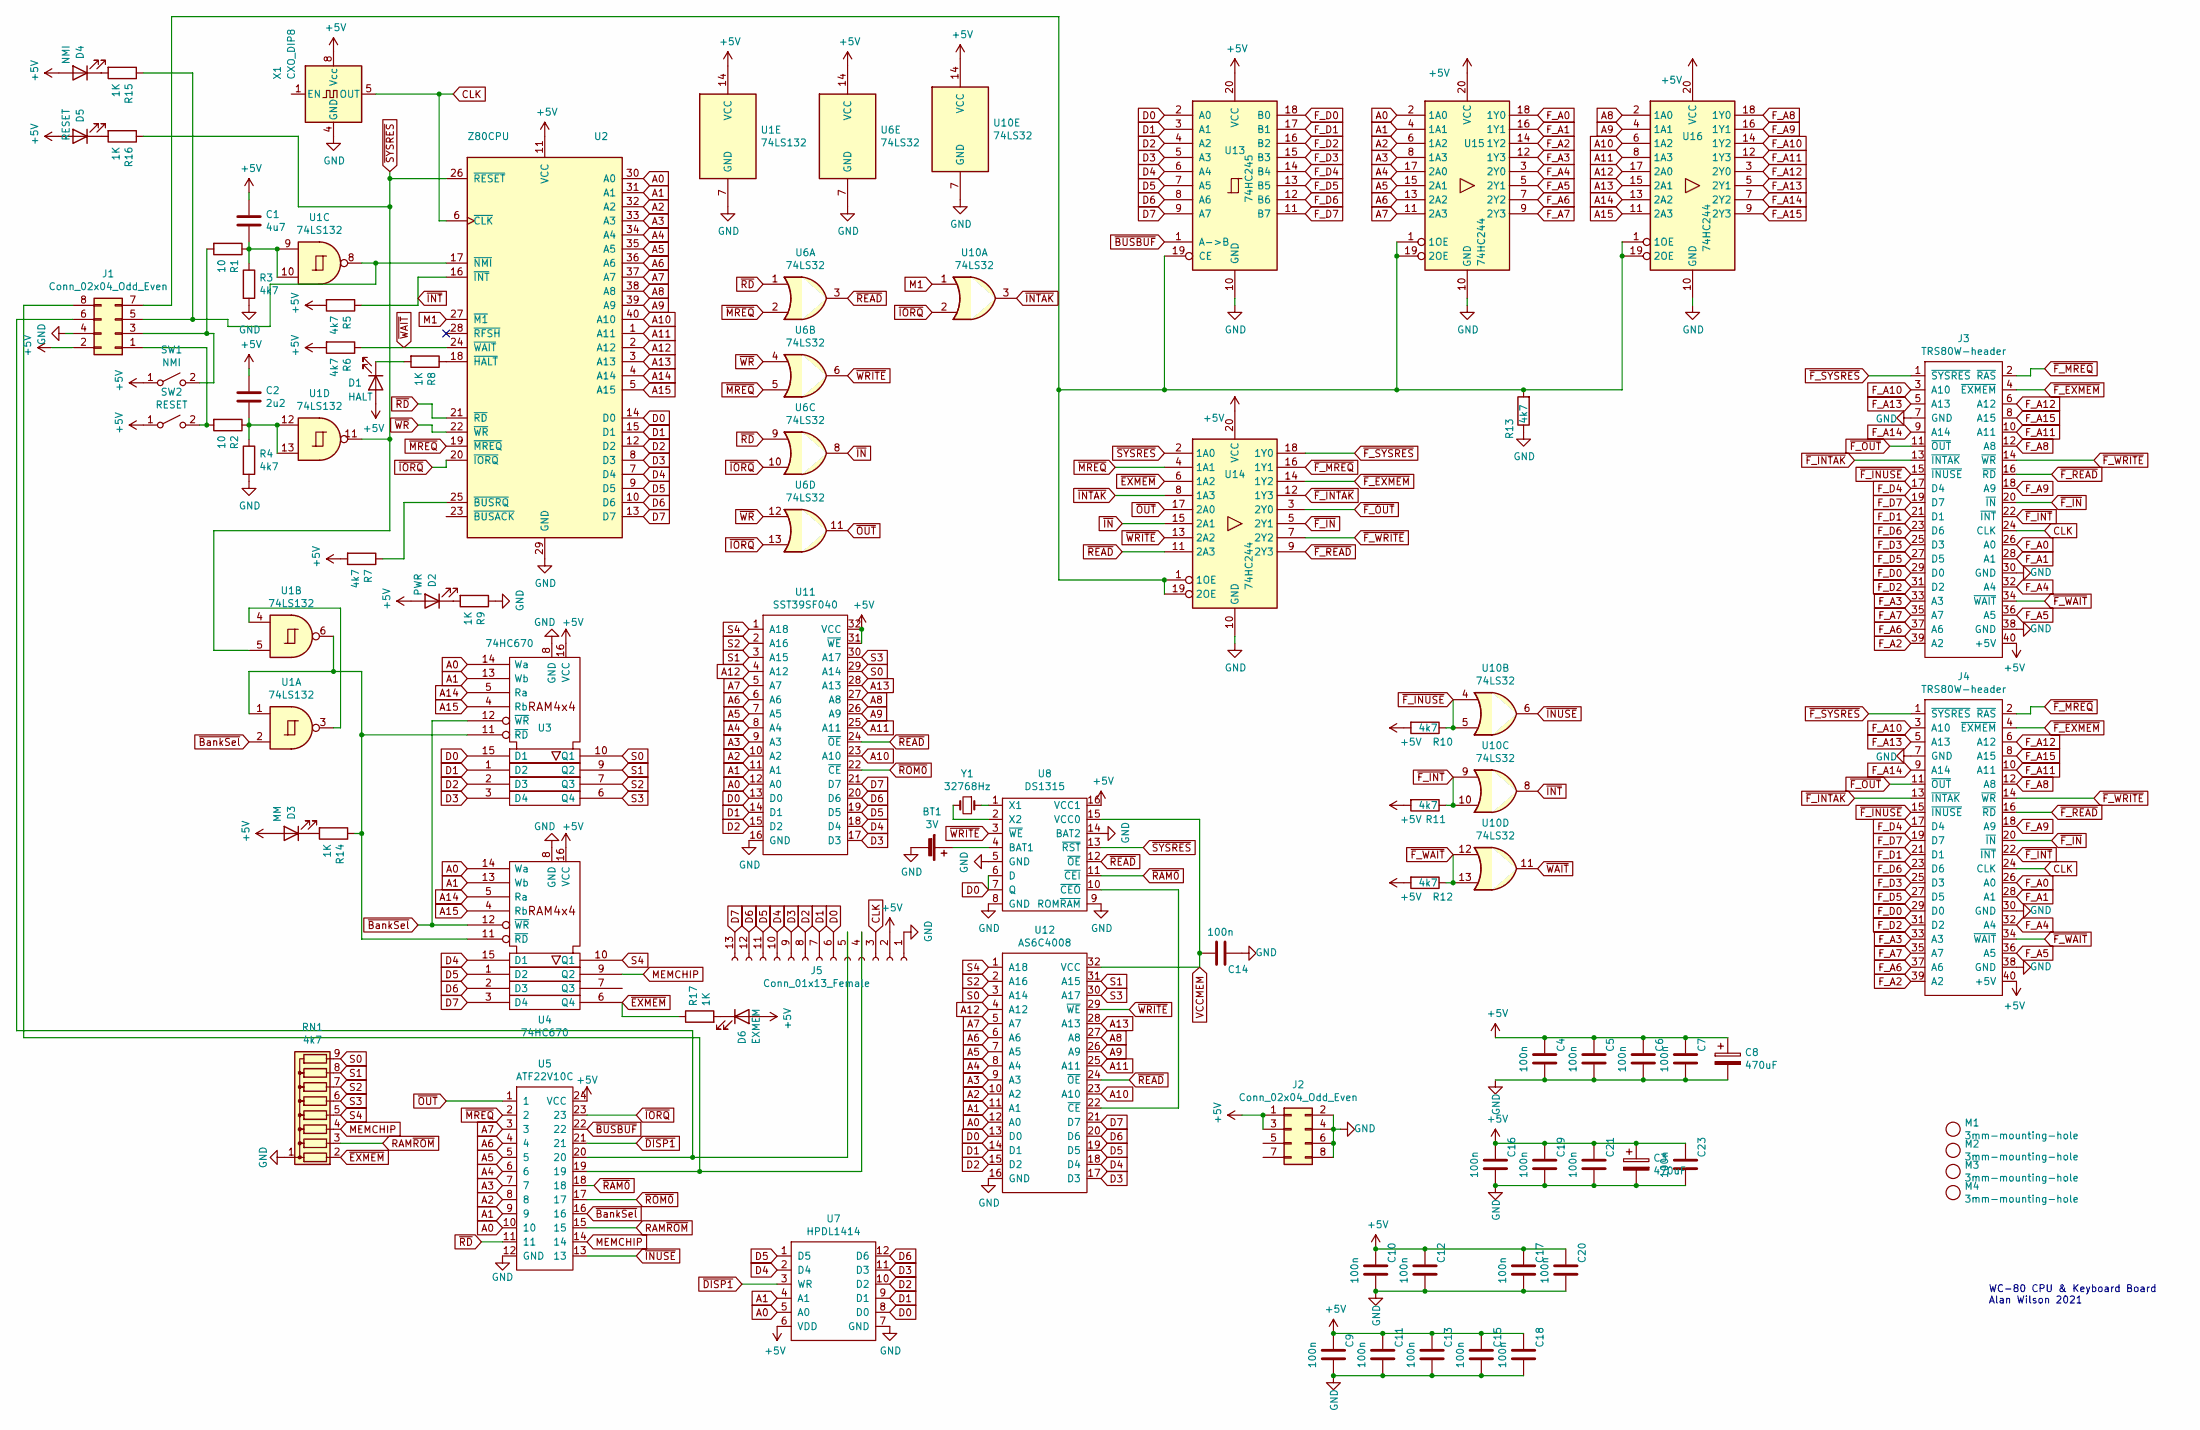
[picture p99: schematic cpu2.sch]

Parts:
BT1: 3V; BS-01-A4CJ004
C1: 4u7; C_0805_2012Metric
C2: 2u2; C_0805_2012Metric
C3, C8: 470uF; CP_Radial_D8.0mm_P3.50mm
C4, C5, C6, C7, C9, C10, C11, C12, C13, C14, C15, C16, C17, C18, C19, C20, C21, C23: 100n; C_0805_2012Metric
D1: HALT; LED_D3.0mm_FlatTop
D2: PWR; LED_D3.0mm_FlatTop
D3: MM; LED_D3.0mm_FlatTop
D4: NMI; LED_D3.0mm_FlatTop
D5: RESET; LED_D3.0mm_FlatTop
D6: EXMEM; LED_D3.0mm_FlatTop
J1, J2: Conn_02x04_Odd_Even; PinHeader_2x04_P2.54mm_Vertical
J3, J4: TRS80W-header; PinHeader_2x20_P2.54mm_Vertical
J5: Conn_01x13_Female; PinHeader_1x13_P2.54mm_Vertical
M1, M2, M3, M4: 3mm-mounting-hole; MountingHole_3.2mm_M3_DIN965_Pad
R1, R2: 10; R_0805_2012Metric
R3, R4, R5, R6, R7, R10, R11, R12, R13: 4k7; R_0805_2012Metric
R8, R9, R14, R15, R16, R17: 1K; R_0805_2012Metric
RN1: 4k7; R_Array_SIP9
SW1: NMI; SW_PUSH_6mm
SW2: RESET; SW_PUSH_6mm
U1: 74LS132; DIP-14_W7.62mm_Socket
U2: Z80CPU; DIP-40_W15.24mm_Socket
U3, U4: 74HC670; DIP-16_W7.62mm_Socket
U5: ATF22V10C; DIP-24_W7.62mm_Socket
U6, U10: 74LS32; DIP-14_W7.62mm_Socket
U7: HPDL1414; DIP-24_W15.24mm_Socket
U8: DS1315; DIP-16_W7.62mm_Socket
U11: SST39SF040; DIP-32_W15.24mm_Socket
U12: AS6C4008; DIP-32_W15.24mm_Socket
U13: 74HC245; DIP-20_W7.62mm_Socket
U14, U15, U16: 74HC244; DIP-20_W7.62mm_Socket
X1: CXO_DIP8; Oscillator_DIP-8
Y1: 32768Hz; Crystal_AT310_D3.0mm_L10.0mm_Horizontal

Connections:
+5V: C1.1, C2.1, C3.1, C4.1, C5.1, C6.1, C7.1, C8.1, C9.1, C10.1, C11.1, C12.1, C13.1, C15.1, C16.1, C17.1, C18.1, C19.1, C20.1, C21.1, C23.1, D1.2 (A), D2.2 (A), D3.2 (A), D4.2 (A), D5.2 (A), D6.2 (A), J1.2, J2.1, J2.3, J3.40 (+5V), J4.40 (+5V), J5.2, R5.2, R6.2, R7.2, R10.2, R11.2, R12.2, SW1.1 (A), SW2.1 (A), U1.14 (VCC), U2.11 (VCC), U3.16 (VCC), U4.16 (VCC), U5.24 (VCC), U6.14 (VCC), U7.6 (VDD), U8.16 (VCC1), U10.14 (VCC), U11.31 (~WE~), U11.32 (VCC), U13.20 (VCC), U14.20 (VCC), U15.20 (VCC), U16.20 (VCC), X1.8 (Vcc)
A0: U2.30 (A0), U3.14 (Wa), U4.14 (Wa), U5.10, U7.5 (A0), U11.12 (A0), U12.12 (A0), U15.2 (1A0)
A1: U2.31 (A1), U3.13 (Wb), U4.13 (Wb), U5.9, U7.4 (A1), U11.11 (A1), U12.11 (A1), U15.4 (1A1)
A2: U2.32 (A2), U5.8, U11.10 (A2), U12.10 (A2), U15.6 (1A2)
A3: U2.33 (A3), U5.7, U11.9 (A3), U12.9 (A3), U15.8 (1A3)
A4: U2.34 (A4), U5.6, U11.8 (A4), U12.8 (A4), U15.17 (2A0)
A5: U2.35 (A5), U5.5, U11.7 (A5), U12.7 (A5), U15.15 (2A1)
A6: U2.36 (A6), U5.4, U11.6 (A6), U12.6 (A6), U15.13 (2A2)
A7: U2.37 (A7), U5.3, U11.5 (A7), U12.5 (A7), U15.11 (2A3)
A8: U2.38 (A8), U11.27 (A8), U12.27 (A8), U16.2 (1A0)
A9: U2.39 (A9), U11.26 (A9), U12.26 (A9), U16.4 (1A1)
A10: U2.40 (A10), U11.23 (A10), U12.23 (A10), U16.6 (1A2)
A11: U2.1 (A11), U11.25 (A11), U12.25 (A11), U16.8 (1A3)
A12: U2.2 (A12), U11.4 (A12), U12.4 (A12), U16.17 (2A0)
A13: U2.3 (A13), U11.28 (A13), U12.28 (A13), U16.15 (2A1)
A14: U2.4 (A14), U3.5 (Ra), U4.5 (Ra), U16.13 (2A2)
A15: U2.5 (A15), U3.4 (Rb), U4.4 (Rb), U16.11 (2A3)
CLK: J3.24 (CLK), J4.24 (CLK), J5.3, U2.6 (~CLK~), X1.5 (OUT)
D0: J5.6, U2.14 (D0), U3.15 (D1), U7.8 (D0), U8.6 (D), U8.7 (Q), U11.13 (D0), U12.13 (D0), U13.2 (A0)
D1: J5.7, U2.15 (D1), U3.1 (D2), U7.9 (D1), U11.14 (D1), U12.14 (D1), U13.3 (A1)
D2: J5.8, U2.12 (D2), U3.2 (D3), U7.10 (D2), U11.15 (D2), U12.15 (D2), U13.4 (A2)
D3: J5.9, U2.8 (D3), U3.3 (D4), U7.11 (D3), U11.17 (D3), U12.17 (D3), U13.5 (A3)
D4: J5.10, U2.7 (D4), U4.15 (D1), U7.2 (D4), U11.18 (D4), U12.18 (D4), U13.6 (A4)
D5: J5.11, U2.9 (D5), U4.1 (D2), U7.1 (D5), U11.19 (D5), U12.19 (D5), U13.7 (A5)
D6: J5.12, U2.10 (D6), U4.2 (D3), U7.12 (D6), U11.20 (D6), U12.20 (D6), U13.8 (A6)
D7: J5.13, U2.13 (D7), U4.3 (D4), U11.21 (D7), U12.21 (D7), U13.9 (A7)
F_A0: J3.26 (A0), J4.26 (A0), U15.18 (1Y0)
F_A1: J3.28 (A1), J4.28 (A1), U15.16 (1Y1)
F_A2: J3.39 (A2), J4.39 (A2), U15.14 (1Y2)
F_A3: J3.33 (A3), J4.33 (A3), U15.12 (1Y3)
F_A4: J3.32 (A4), J4.32 (A4), U15.3 (2Y0)
F_A5: J3.36 (A5), J4.36 (A5), U15.5 (2Y1)
F_A6: J3.37 (A6), J4.37 (A6), U15.7 (2Y2)
F_A7: J3.35 (A7), J4.35 (A7), U15.9 (2Y3)
F_A8: J3.12 (A8), J4.12 (A8), U16.18 (1Y0)
F_A9: J3.18 (A9), J4.18 (A9), U16.16 (1Y1)
F_A10: J3.3 (A10), J4.3 (A10), U16.14 (1Y2)
F_A11: J3.10 (A11), J4.10 (A11), U16.12 (1Y3)
F_A12: J3.6 (A12), J4.6 (A12), U16.3 (2Y0)
F_A13: J3.5 (A13), J4.5 (A13), U16.5 (2Y1)
F_A14: J3.9 (A14), J4.9 (A14), U16.7 (2Y2)
F_A15: J3.8 (A15), J4.8 (A15), U16.9 (2Y3)
F_D0: J3.29 (D0), J4.29 (D0), U13.18 (B0)
F_D1: J3.21 (D1), J4.21 (D1), U13.17 (B1)
F_D2: J3.31 (D2), J4.31 (D2), U13.16 (B2)
F_D3: J3.25 (D3), J4.25 (D3), U13.15 (B3)
F_D4: J3.17 (D4), J4.17 (D4), U13.14 (B4)
F_D5: J3.27 (D5), J4.27 (D5), U13.13 (B5)
F_D6: J3.23 (D6), J4.23 (D6), U13.12 (B6)
F_D7: J3.19 (D7), J4.19 (D7), U13.11 (B7)
GND: BT1.2 (-), C3.2, C4.2, C5.2, C6.2, C7.2, C8.2, C9.2, C10.2, C11.2, C12.2, C13.2, C14.1, C15.2, C16.2, C17.2, C18.2, C19.2, C20.2, C21.2, C23.2, J1.4, J2.2, J2.4, J2.6, J2.8, J3.7 (GND), J3.30 (GND), J3.38 (GND), J4.7 (GND), J4.30 (GND), J4.38 (GND), J5.1, R3.2, R4.2, R9.1, R13.1, RN1.1 (common), U1.7 (GND), U2.29 (GND), U3.8 (GND), U4.8 (GND), U5.12 (GND), U6.7 (GND), U7.7 (GND), U8.5 (GND), U8.8 (GND), U8.9 (ROM~RAM~), U8.14 (BAT2), U10.7 (GND), U11.16 (GND), U12.16 (GND), U13.10 (GND), U14.10 (GND), U15.10 (GND), U16.10 (GND), X1.4 (GND)
M1: U2.27 (~M1~), U10.1
MEMCHIP: RN1.4 (R3), U4.9 (Q2), U5.14
unnamed: BT1.1 (+), U8.4 (BAT1)
unnamed: C1.2, R1.1, R3.1, U1.9, U1.10
unnamed: C2.2, R2.1, R4.1, U1.12, U1.13
unnamed: D1.1 (K), R8.2
unnamed: D2.1 (K), R9.2
unnamed: D3.1 (K), R14.2
unnamed: D4.1 (K), R15.2
unnamed: D5.1 (K), R16.2
unnamed: D6.1 (K), R17.2
unnamed: J1.1, R2.2, SW2.2 (B)
unnamed: J1.3, R1.2, SW1.2 (B)
unnamed: J1.5, R15.1, U1.8, U2.17 (~NMI~)
unnamed: J1.6, J5.5, U5.20
unnamed: J1.7, R13.2, U13.19 (CE), U14.1 (1OE), U14.19 (2OE), U15.1 (1OE), U15.19 (2OE), U16.1 (1OE), U16.19 (2OE)
unnamed: J1.8, J5.4, U5.19
unnamed: R7.1, U2.25 (~BUSRQ~)
unnamed: R8.1, U2.18 (~HALT~)
unnamed: R14.1, U1.1, U1.6, U3.11 (~RD), U4.11 (~RD)
unnamed: U1.3, U1.4
unnamed: U8.1 (X1), Y1.1
unnamed: U8.2 (X2), Y1.2
unnamed: U8.10 (~CEO~), U12.22 (~CE~)
RAM~ROM~: RN1.3 (R2), U5.15
S0: RN1.9 (R8), U3.10 (Q1), U11.29 (A14), U12.3 (A14)
S1: RN1.8 (R7), U3.9 (Q2), U11.3 (A15), U12.31 (A15)
S2: RN1.7 (R6), U3.7 (Q3), U11.2 (A16), U12.2 (A16)
S3: RN1.6 (R5), U3.6 (Q4), U11.30 (A17), U12.30 (A17)
S4: RN1.5 (R4), U4.10 (Q1), U11.1 (A18), U12.1 (A18)
VCCMEM: C14.2, U8.15 (VCC0), U12.32 (VCC)
~BUSBUF~: U5.22, U13.1 (A->B)
~BankSel~: U1.2, U3.12 (~WR), U4.12 (~WR), U5.16
~DISP1~: U5.21, U7.3 (WR)
~EXMEM~: R17.1, RN1.2 (R1), U4.6 (Q4), U14.6 (1A2)
~F_EXMEM~: J3.4 (~EXMEM~), J4.4 (~EXMEM~), U14.14 (1Y2)
~F_INTAK~: J3.13 (~INTAK~), J4.13 (~INTAK~), U14.12 (1Y3)
~F_INT~: J3.22 (~INT~), J4.22 (~INT~), R11.1, U10.9, U10.10
~F_INUSE~: J3.15 (~INUSE~), J4.15 (~INUSE~), R10.1, U10.4, U10.5
~F_IN~: J3.20 (~IN~), J4.20 (~IN~), U14.5 (2Y1)
~F_MREQ~: J3.2 (~RAS~), J4.2 (~RAS~), U14.16 (1Y1)
~F_OUT~: J3.11 (~OUT~), J4.11 (~OUT~), U14.3 (2Y0)
~F_READ~: J3.16 (~RD~), J4.16 (~RD~), U14.9 (2Y3)
~F_SYSRES~: J3.1 (~SYSRES~), J4.1 (~SYSRES~), U14.18 (1Y0)
~F_WAIT~: J3.34 (~WAIT~), J4.34 (~WAIT~), R12.1, U10.12, U10.13
~F_WRITE~: J3.14 (~WR~), J4.14 (~WR~), U14.7 (2Y2)
~INTAK~: U10.3, U14.8 (1A3)
~INT~: R5.1, U2.16 (~INT~), U10.8
~INUSE~: U5.13, U10.6
~IN~: U6.8, U14.15 (2A1)
~IORQ~: U2.20 (~IORQ~), U5.23, U6.10, U6.13, U10.2
~MREQ~: U2.19 (~MREQ~), U5.2, U6.2, U6.5, U14.4 (1A1)
~OUT~: U5.1, U6.11, U14.17 (2A0)
~RAM0~: U5.18, U8.11 (~CEI~)
~RD~: U2.21 (~RD~), U5.11, U6.1, U6.9
~READ~: U6.3, U8.12 (~OE~), U11.24 (~OE~), U12.24 (~OE~), U14.11 (2A3)
~ROM0~: U5.17, U11.22 (~CE~)
~SYSRES~: R16.1, U1.5, U1.11, U2.26 (~RESET~), U8.13 (~RST~), U14.2 (1A0)
~WAIT~: R6.1, U2.24 (~WAIT~), U10.11
~WRITE~: U6.6, U8.3 (~WE~), U12.29 (~WE~), U14.13 (2A2)
~WR~: U2.22 (~WR~), U6.4, U6.12

Notes on the sheet:
WC-80 CPU & Keyboard Board Alan Wilson 2021

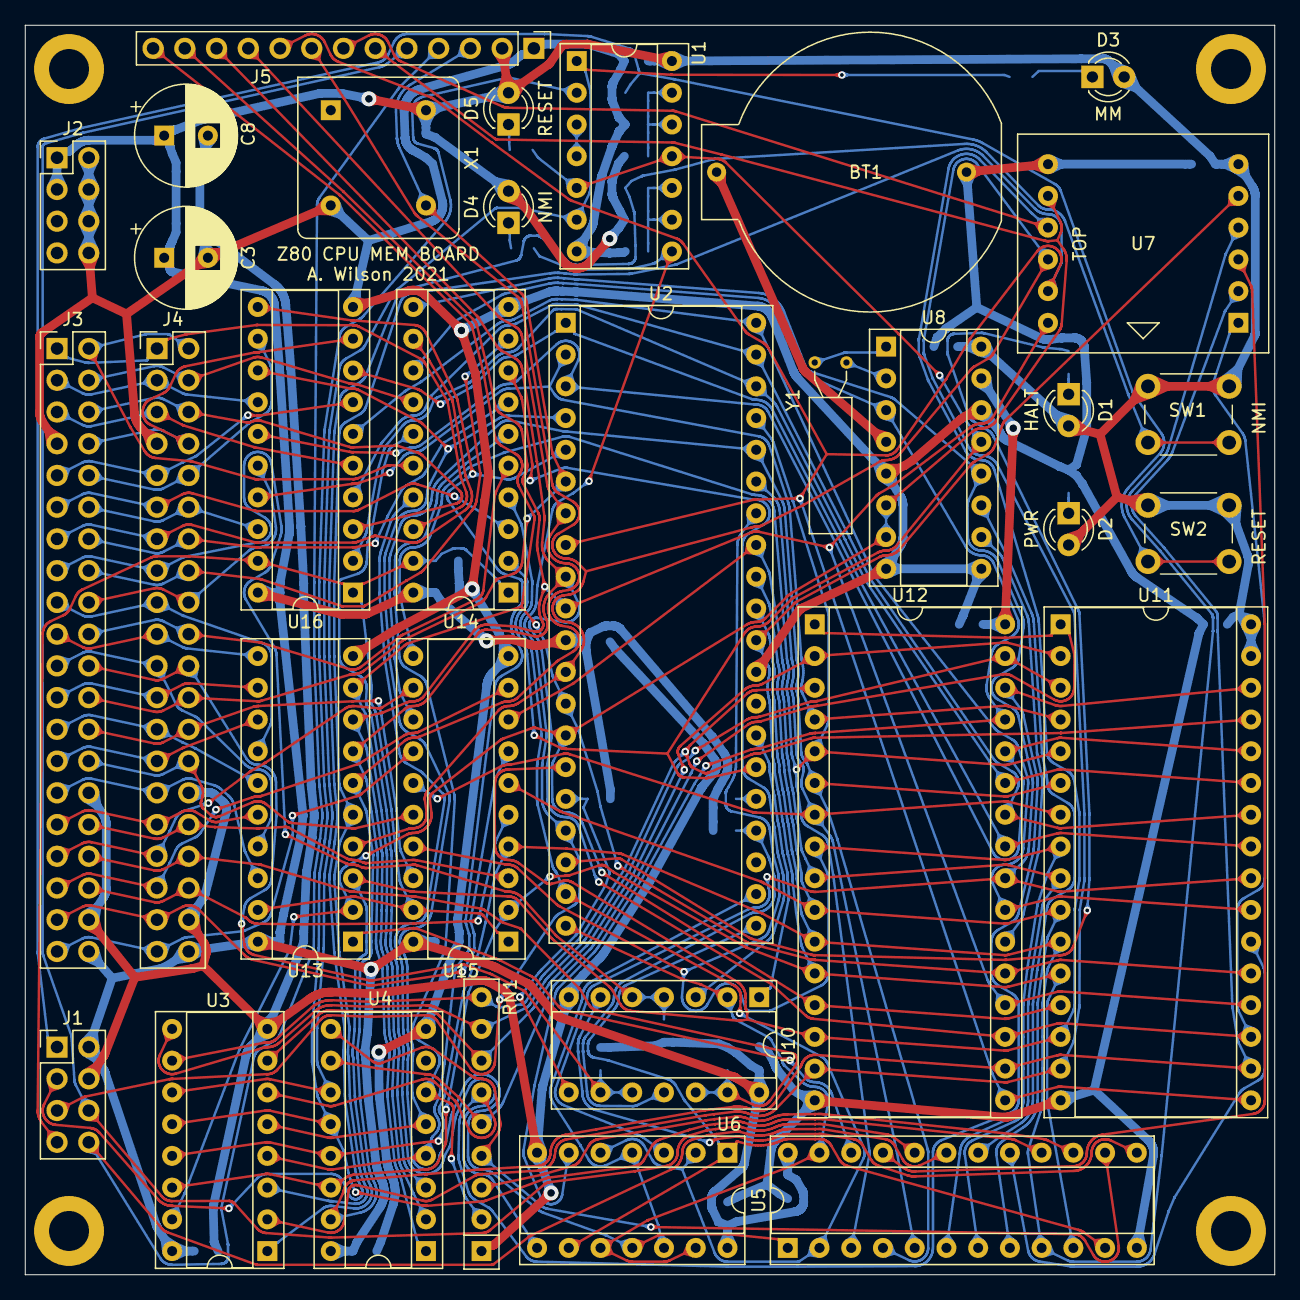
[picture p100: board cpu2.kicad_pcb from above]

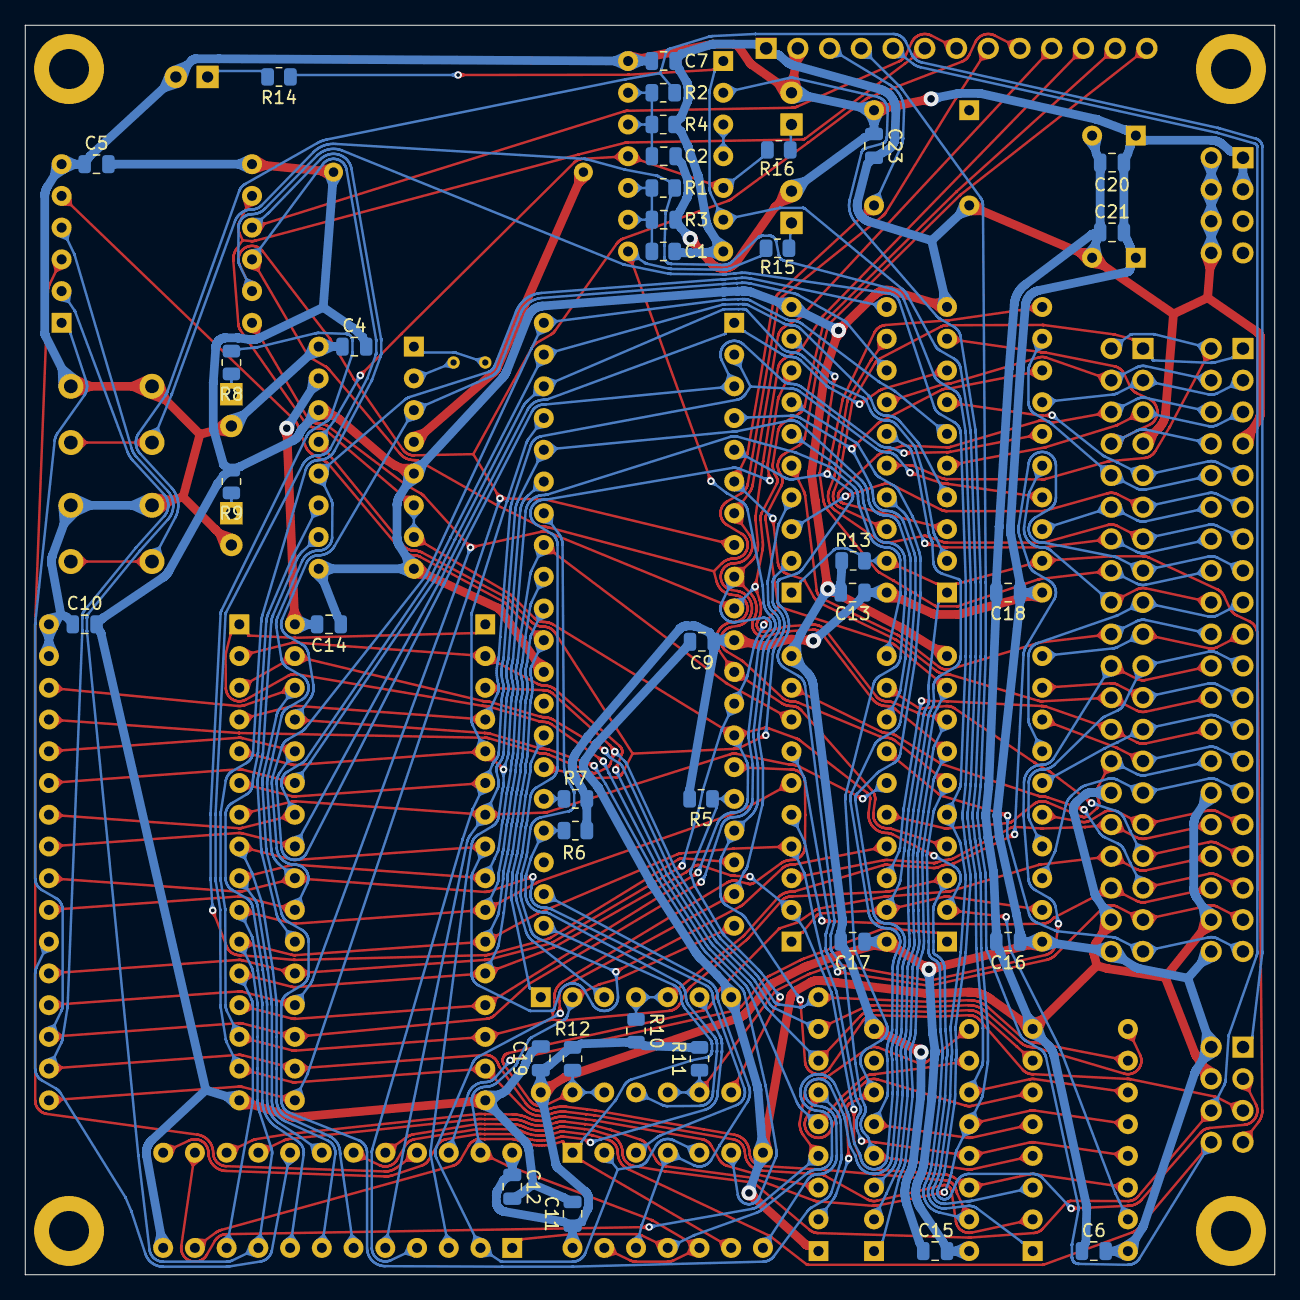
[picture p101: board cpu2.kicad_pcb from below]

Board: 2 copper layers, 100.0 x 100.0 mm, 73 parts (36 on the bottom side), 111 nets.
