alnwlsn/wc-80-archive/boards/0old/ledboard22/v1/main.kicad_pcb

## KiCad design boards/0old/ledboard22/v1/main.kicad_pcb (2025-07-11, an earlier design)

Schematic: main.sch

Parts:
C1, C2, C3, C4, C6, C8, C14: 100n; C_0805_2012Metric
C5, C9: 470uF; CP_Radial_D8.0mm_P3.50mm
D1: D0; LED_D3.0mm_FlatTop
D2: D2; LED_D3.0mm_FlatTop
D3: D4; LED_D3.0mm_FlatTop
D4: D6; LED_D3.0mm_FlatTop
D5: D7; LED_D3.0mm_FlatTop
D6: D5; LED_D3.0mm_FlatTop
D7: D3; LED_D3.0mm_FlatTop
D8: D1; LED_D3.0mm_FlatTop
D9: A0; LED_D3.0mm_FlatTop
D10: A2; LED_D3.0mm_FlatTop
D11: A4; LED_D3.0mm_FlatTop
D12: A6; LED_D3.0mm_FlatTop
D13: A7; LED_D3.0mm_FlatTop
D14: A5; LED_D3.0mm_FlatTop
D15: A3; LED_D3.0mm_FlatTop
D16: A1; LED_D3.0mm_FlatTop
D17: A8; LED_D3.0mm_FlatTop
D18: A10; LED_D3.0mm_FlatTop
D19: A12; LED_D3.0mm_FlatTop
D20: A14; LED_D3.0mm_FlatTop
D21: A15; LED_D3.0mm_FlatTop
D22: A13; LED_D3.0mm_FlatTop
D23: A11; LED_D3.0mm_FlatTop
D24: A9; LED_D3.0mm_FlatTop
D25: IN; LED_D3.0mm_FlatTop
D26: OUT; LED_D3.0mm_FlatTop
D27: READ; LED_D3.0mm_FlatTop
D28: WRITE; LED_D3.0mm_FlatTop
H1, H2, H3, H4: MountingHole; MountingHole_3.2mm_M3_DIN965
J1, J2: TRS80W-header; PinHeader_2x20_P2.54mm_Vertical
J3, J4: Conn_02x04_Odd_Even; PinHeader_2x04_P2.54mm_Vertical
R1, R2, R3, R4: 4.7K; R_0805_2012Metric
R5, R6, R7, R8: 470; R_0805_2012Metric
RN1, RN2, RN3: 470; R_Array_SIP9
SW1: IN; PinHeader_1x03_P2.54mm_Vertical
SW2: OUT; PinHeader_1x03_P2.54mm_Vertical
SW3: READ; PinHeader_1x03_P2.54mm_Vertical
SW4: WRITE; PinHeader_1x03_P2.54mm_Vertical
U1: 74LS32; DIP-14_W7.62mm_Socket
U2: 74LS20; DIP-14_W7.62mm_Socket
U3, U4, U5: 74LS374; DIP-20_W7.62mm_Socket

Connections:
+5V: C1.1, C2.1, C3.1, C4.1, C5.1, C6.1, C8.1, C9.1, C14.1, J1.40 (+5V), J2.40 (+5V), J3.1, J3.3, J4.2, R1.1, R2.1, R3.1, R4.1, R5.1, R6.1, R7.1, R8.1, U1.14 (VCC), U2.14 (VCC), U3.20 (VCC), U4.20 (VCC), U5.20 (VCC)
CLK: J1.24 (CLK), J2.24 (CLK)
F_A0: J1.26 (A0), J2.26 (A0), U4.3 (D0)
F_A1: J1.28 (A1), J2.28 (A1), U4.18 (D7)
F_A2: J1.39 (A2), J2.39 (A2), U4.4 (D1)
F_A3: J1.33 (A3), J2.33 (A3), U4.17 (D6)
F_A4: J1.32 (A4), J2.32 (A4), U4.7 (D2)
F_A5: J1.36 (A5), J2.36 (A5), U4.14 (D5)
F_A6: J1.37 (A6), J2.37 (A6), U4.8 (D3)
F_A7: J1.35 (A7), J2.35 (A7), U4.13 (D4)
F_A8: J1.12 (A8), J2.12 (A8), U5.3 (D0)
F_A9: J1.18 (A9), J2.18 (A9), U5.18 (D7)
F_A10: J1.3 (A10), J2.3 (A10), U5.4 (D1)
F_A11: J1.10 (A11), J2.10 (A11), U5.17 (D6)
F_A12: J1.6 (A12), J2.6 (A12), U5.7 (D2)
F_A13: J1.5 (A13), J2.5 (A13), U5.14 (D5)
F_A14: J1.9 (A14), J2.9 (A14), U5.8 (D3)
F_A15: J1.8 (A15), J2.8 (A15), U5.13 (D4)
F_D0: J1.29 (D0), J2.29 (D0), U3.3 (D0)
F_D1: J1.21 (D1), J2.21 (D1), U3.18 (D7)
F_D2: J1.31 (D2), J2.31 (D2), U3.4 (D1)
F_D3: J1.25 (D3), J2.25 (D3), U3.17 (D6)
F_D4: J1.17 (D4), J2.17 (D4), U3.7 (D2)
F_D5: J1.27 (D5), J2.27 (D5), U3.14 (D5)
F_D6: J1.23 (D6), J2.23 (D6), U3.8 (D3)
F_D7: J1.19 (D7), J2.19 (D7), U3.13 (D4)
GND: C1.2, C2.2, C3.2, C4.2, C5.2, C6.2, C8.2, C9.2, C14.2, J1.7 (GND), J1.30 (GND), J1.38 (GND), J2.7 (GND), J2.30 (GND), J2.38 (GND), J3.2, J3.4, J3.6, J3.8, J4.4, RN1.1, RN2.1, RN3.1, SW1.1, SW2.1, SW3.1, SW4.1, U1.7 (GND), U2.7 (GND), U3.1 (OE), U3.10 (GND), U4.1 (OE), U4.10 (GND), U5.1 (OE), U5.10 (GND)
unnamed: D1.1 (K), RN1.9
unnamed: D1.2 (A), U3.2 (O0)
unnamed: D2.1 (K), RN1.7
unnamed: D2.2 (A), U3.5 (O1)
unnamed: D3.1 (K), RN1.5
unnamed: D3.2 (A), U3.6 (O2)
unnamed: D4.1 (K), RN1.3
unnamed: D4.2 (A), U3.9 (O3)
unnamed: D5.1 (K), RN1.2
unnamed: D5.2 (A), U3.12 (O4)
unnamed: D6.1 (K), RN1.4
unnamed: D6.2 (A), U3.15 (O5)
unnamed: D7.1 (K), RN1.6
unnamed: D7.2 (A), U3.16 (O6)
unnamed: D8.1 (K), RN1.8
unnamed: D8.2 (A), U3.19 (O7)
unnamed: D9.1 (K), RN2.9
unnamed: D9.2 (A), U4.2 (O0)
unnamed: D10.1 (K), RN2.7
unnamed: D10.2 (A), U4.5 (O1)
unnamed: D11.1 (K), RN2.5
unnamed: D11.2 (A), U4.6 (O2)
unnamed: D12.1 (K), RN2.3
unnamed: D12.2 (A), U4.9 (O3)
unnamed: D13.1 (K), RN2.2
unnamed: D13.2 (A), U4.12 (O4)
unnamed: D14.1 (K), RN2.4
unnamed: D14.2 (A), U4.15 (O5)
unnamed: D15.1 (K), RN2.6
unnamed: D15.2 (A), U4.16 (O6)
unnamed: D16.1 (K), RN2.8
unnamed: D16.2 (A), U4.19 (O7)
unnamed: D17.1 (K), RN3.2
unnamed: D17.2 (A), U5.2 (O0)
unnamed: D18.1 (K), RN3.4
unnamed: D18.2 (A), U5.5 (O1)
unnamed: D19.1 (K), RN3.6
unnamed: D19.2 (A), U5.6 (O2)
unnamed: D20.1 (K), RN3.8
unnamed: D20.2 (A), U5.9 (O3)
unnamed: D21.1 (K), RN3.9
unnamed: D21.2 (A), U5.12 (O4)
unnamed: D22.1 (K), RN3.7
unnamed: D22.2 (A), U5.15 (O5)
unnamed: D23.1 (K), RN3.5
unnamed: D23.2 (A), U5.16 (O6)
unnamed: D24.1 (K), RN3.3
unnamed: D24.2 (A), U5.19 (O7)
unnamed: D25.1 (K), U1.3, U2.1
unnamed: D25.2 (A), R5.2
unnamed: D26.1 (K), U1.6, U2.2
unnamed: D26.2 (A), R6.2
unnamed: D27.1 (K), U1.8, U2.4
unnamed: D27.2 (A), R7.2
unnamed: D28.1 (K), U1.11, U2.5
unnamed: D28.2 (A), R8.2
unnamed: R1.2, SW1.2, U1.2
unnamed: R2.2, SW2.2, U1.5
unnamed: R3.2, SW3.2, U1.10
unnamed: R4.2, SW4.2, U1.13
unnamed: U2.8, U3.11 (Cp), U4.11 (Cp), U5.11 (Cp)
unnamed: U2.6, U2.9, U2.10, U2.12, U2.13
~F_EXMEM~: J1.4 (~EXMEM~), J2.4 (~EXMEM~)
~F_INTAK~: J1.13 (~INTAK~), J2.13 (~INTAK~)
~F_INT~: J1.22 (~INT~), J2.22 (~INT~)
~F_INUSE~: J1.15 (~INUSE~), J2.15 (~INUSE~)
~F_IN~: J1.20 (~IN~), J2.20 (~IN~), U1.1
~F_MREQ~: J1.2 (~RAS~), J2.2 (~RAS~)
~F_OUT~: J1.11 (~OUT~), J2.11 (~OUT~), U1.4
~F_READ~: J1.16 (~RD~), J2.16 (~RD~), U1.9
~F_SYSRES~: J1.1 (~SYSRES~), J2.1 (~SYSRES~)
~F_WAIT~: J1.34 (~WAIT~), J2.34 (~WAIT~)
~F_WRITE~: J1.14 (~WR~), J2.14 (~WR~), U1.12

Notes on the sheet:
WC-80 Z80 Computer Project Alan Wilson 2021

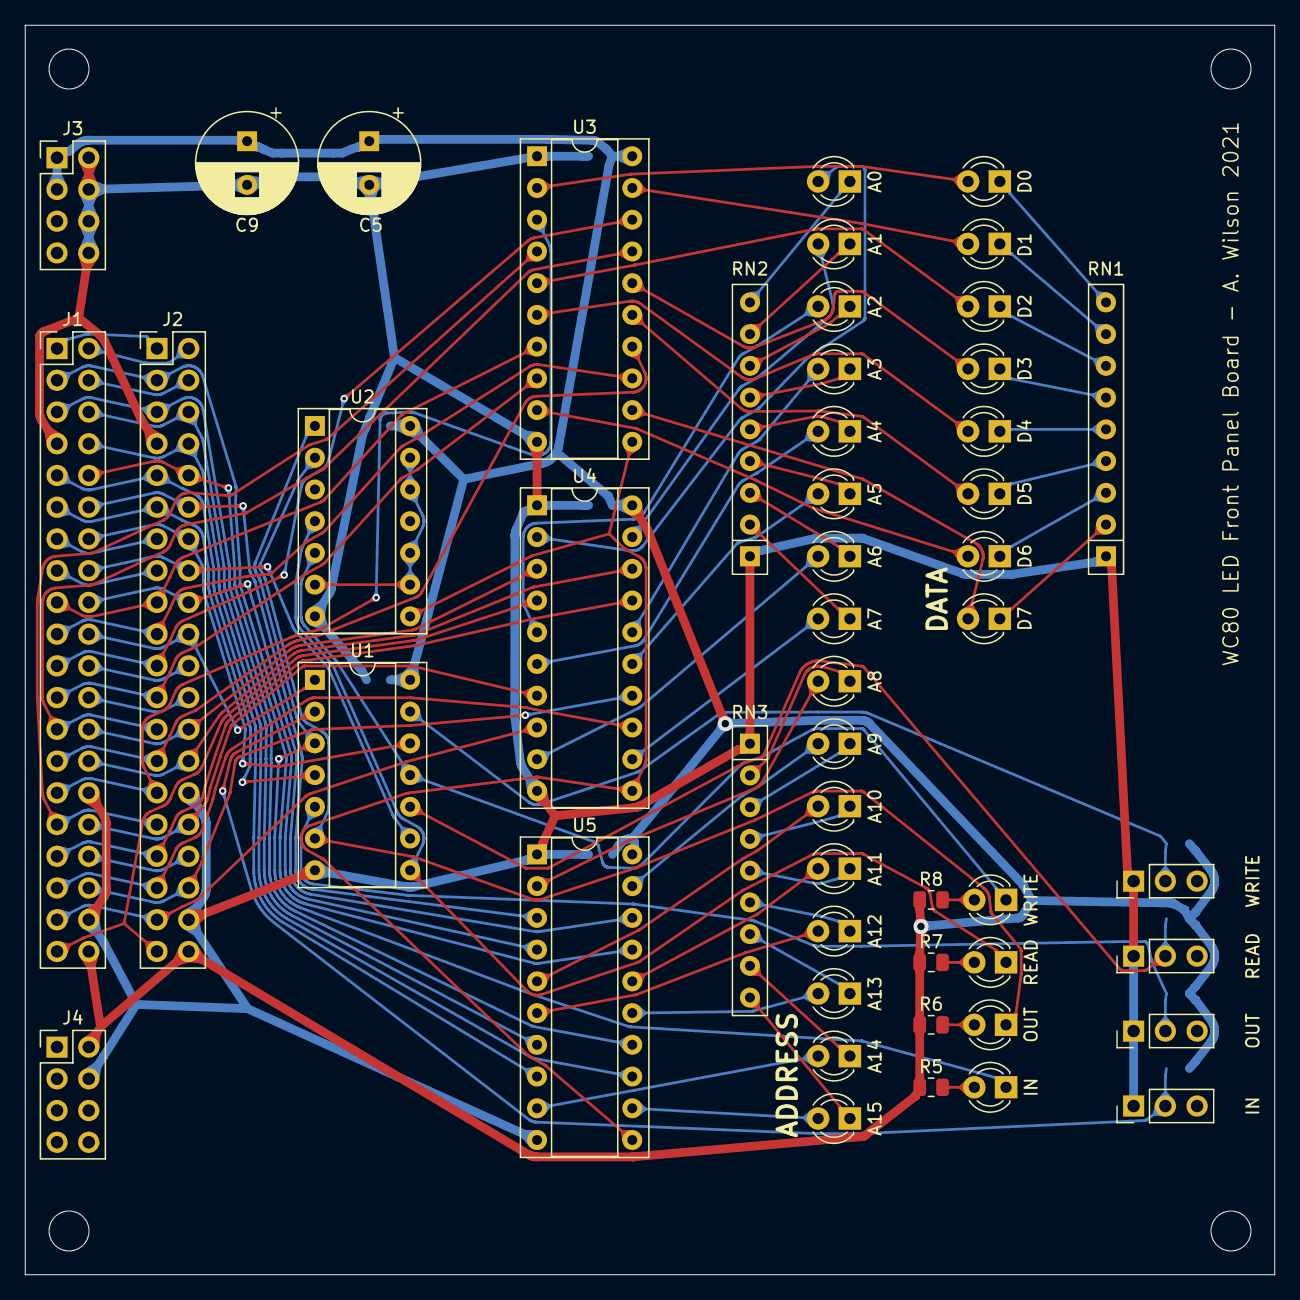
[picture p102: board boards/0old/ledboard22/v1/main.kicad_pcb from above]

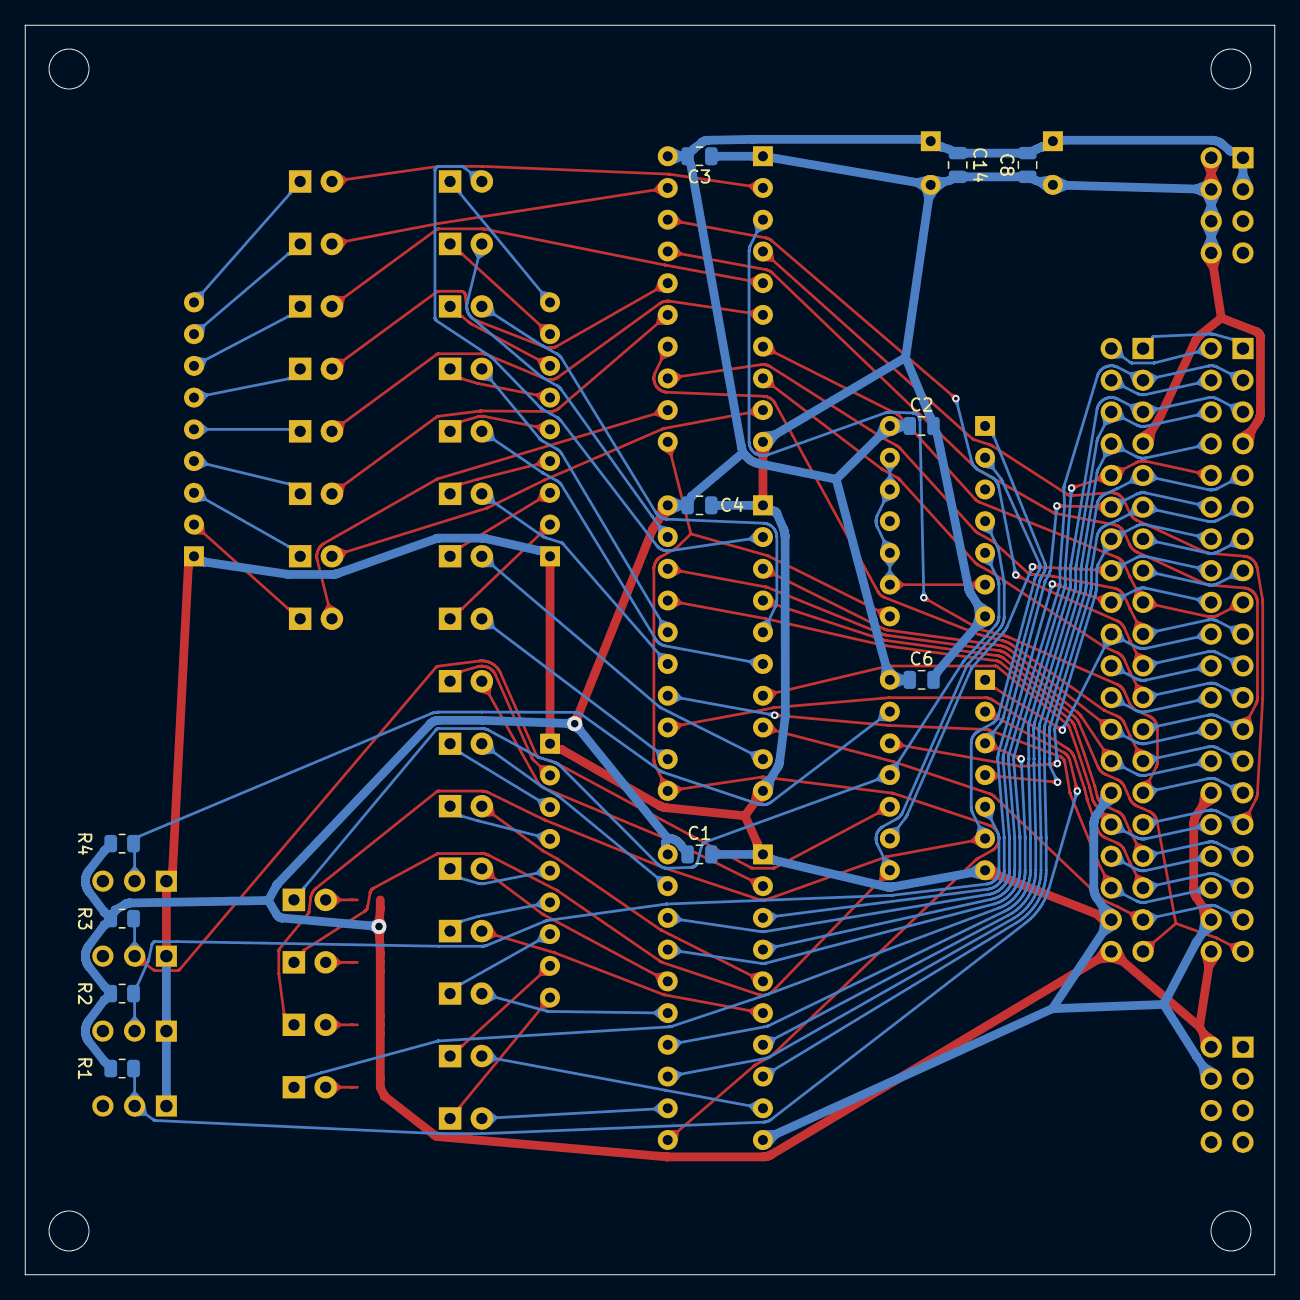
[picture p103: board boards/0old/ledboard22/v1/main.kicad_pcb from below]

Board: 2 copper layers, 100.0 x 100.0 mm, 65 parts (11 on the bottom side), 100 nets.
