alnwlsn/wc-80-archive/boards/0old/cpu/cpu.kicad_pcb

## KiCad design boards/0old/cpu/cpu.kicad_pcb (2025-07-11, an earlier design)

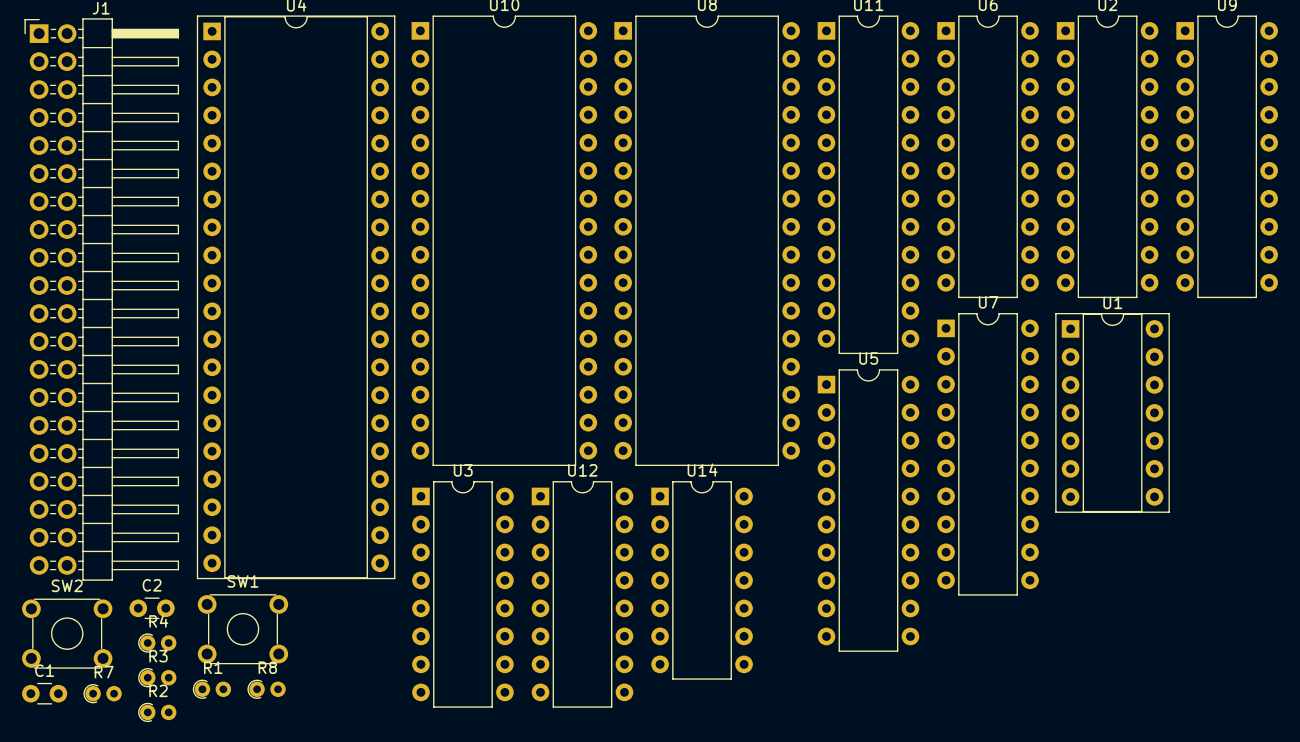
[picture p104: board cpu.kicad_pcb from above]

Board: 2 copper layers, 24 parts (0 on the bottom side), 87 nets, no tracks yet.

Parts:
C1, C2: 1uF; C_Disc_D3.0mm_W1.6mm_P2.50mm
J1: Z80-BUS; PinHeader_2x20_P2.54mm_Horizontal
R1, R3: 100; R_Axial_DIN0204_L3.6mm_D1.6mm_P1.90mm_Vertical
R2, R4: 4k7; R_Axial_DIN0204_L3.6mm_D1.6mm_P1.90mm_Vertical
R7, R8: 330; R_Axial_DIN0204_L3.6mm_D1.6mm_P1.90mm_Vertical
SW1: RESET; SW_TH_Tactile_Omron_B3F-10xx
SW2: NMI; SW_TH_Tactile_Omron_B3F-10xx
U1: SN74HCT32N; DIP-14_W7.62mm_Socket
U2: SN74HCT244N; DIP-20_W7.62mm
U3, U12: 74LS670N; DIP-16_W7.62mm
U4: Z80CPU; DIP-40_W15.24mm_Socket
U5, U6: SN74HCT32N; DIP-20_W7.62mm
U7: 74HCT245N; DIP-20_W7.62mm
U8: 628128_DIP32_SSOP32; DIP-32_W15.24mm
U9: 74HCT273; DIP-20_W7.62mm
U10: SST39SF040; DIP-32_W15.24mm
U11: GAL22V10; DIP-24_W7.62mm
U14: 74LS132N; DIP-14_W7.62mm

Connections:
*CPUMEM: J1.10, U9.19
*EXTMEM: J1.9, U11.13
+5V: J1.1, J1.3, R2.2, R4.2, U1.14, U2.20, U4.11, U5.20, U6.20, U7.20, U8.30, U8.32, U9.20, U10.31, U10.32, U11.24
/ramAltHigh: U9.16, U11.15
/ramAltLow: U9.15, U11.16
/~rom~ram: U9.12, U11.14
BIOL: U9.11, U11.23
GND: C1.2, C2.2, J1.2, J1.4, SW1.1, SW2.1, U1.7, U2.10, U2.19, U4.29, U5.10, U6.10, U7.10, U8.16, U9.10, U10.16, U11.12
unnamed: C1.1, R1.1, R2.1, U14.1, U14.2
unnamed: C2.1, R3.1, R4.1, U14.4, U14.5
unnamed: R1.2, SW1.2
unnamed: R3.2, SW2.2
unnamed: R7.2, U14.3
unnamed: R8.2, U14.6
unnamed: U1.1, U1.13, U4.19
unnamed: U1.2, U1.5, U4.21, U7.1
unnamed: U1.3, U2.2
unnamed: U1.4, U1.9, U4.20
unnamed: U1.6, U2.6
unnamed: U1.8, U2.8
unnamed: U1.10, U1.12, U4.22
unnamed: U1.11, U2.4
unnamed: U2.1, U5.1, U5.19, U6.1, U6.19, U7.19
unnamed: U2.7, U4.24
unnamed: U2.9, U4.16
unnamed: U4.1, U6.8
unnamed: U4.2, U6.11
unnamed: U4.3, U6.13
unnamed: U4.4, U6.15
unnamed: U4.5, U6.17
unnamed: U4.7, U7.6
unnamed: U4.8, U7.5
unnamed: U4.9, U7.7
unnamed: U4.10, U7.8
unnamed: U4.12, U7.4
unnamed: U4.13, U7.9
unnamed: U4.14, U7.2
unnamed: U4.15, U7.3
unnamed: U4.30, U5.2
unnamed: U4.31, U5.4
unnamed: U4.32, U5.6
unnamed: U4.33, U5.8
unnamed: U4.34, U5.11
unnamed: U4.35, U5.13
unnamed: U4.36, U5.15
unnamed: U4.37, U5.17
unnamed: U4.38, U6.2
unnamed: U4.39, U6.4
unnamed: U4.40, U6.6
unnamed: U9.9, U10.1
unnamed: U9.5, U10.2
unnamed: U9.2, U10.3
unnamed: U9.6, U10.30
RAMA15: U8.31, U11.18
RAMA16: U8.2, U11.19
ZA0: J1.19, U8.12, U10.12, U11.9
ZA1: J1.20, U8.11, U10.11, U11.8
ZA2: J1.21, U8.10, U10.10, U11.7
ZA3: J1.22, U8.9, U10.9, U11.6
ZA4: J1.23, U8.8, U10.8, U11.5
ZA5: J1.24, U8.7, U10.7, U11.4
ZA6: J1.25, U8.6, U10.6, U11.3
ZA7: J1.26, U8.5, U10.5, U11.2
ZA8: J1.27, U8.27, U10.27
ZA9: J1.28, U8.26, U10.26
ZA10: J1.29, U8.23, U10.23
ZA11: J1.30, U8.25, U10.25
ZA12: J1.31, U8.4, U10.4
ZA13: J1.32, U8.28, U10.28
ZA14: J1.33, U8.3, U10.29
ZA15: J1.34, U11.17
ZD0: J1.11, U8.13, U9.3, U10.13
ZD1: J1.12, U8.14, U9.4, U10.14
ZD2: J1.13, U8.15, U9.7, U10.15
ZD3: J1.14, U8.17, U9.8, U10.17
ZD4: J1.15, U8.18, U9.13, U10.18
ZD5: J1.16, U8.19, U9.14, U10.19
ZD6: J1.17, U8.20, U9.17, U10.20
ZD7: J1.18, U8.21, U9.18, U10.21
ZIORQ: J1.6, U11.11
ZMREQ: J1.5, U11.1
ZNMI: J1.35, U4.17
ZRD: J1.7, U8.24, U10.24
ZRESET: J1.40, U4.26, U9.1
ZWR: J1.8, U8.29, U11.10
\RAMCS: U8.22, U11.21
\ROMCS: U10.22, U11.20
