alnwlsn/wc-80-archive/boards/floppy/rev1-2/main.kicad_pcb

## KiCad design boards/floppy/rev1-2/main.kicad_pcb (2025-07-11)

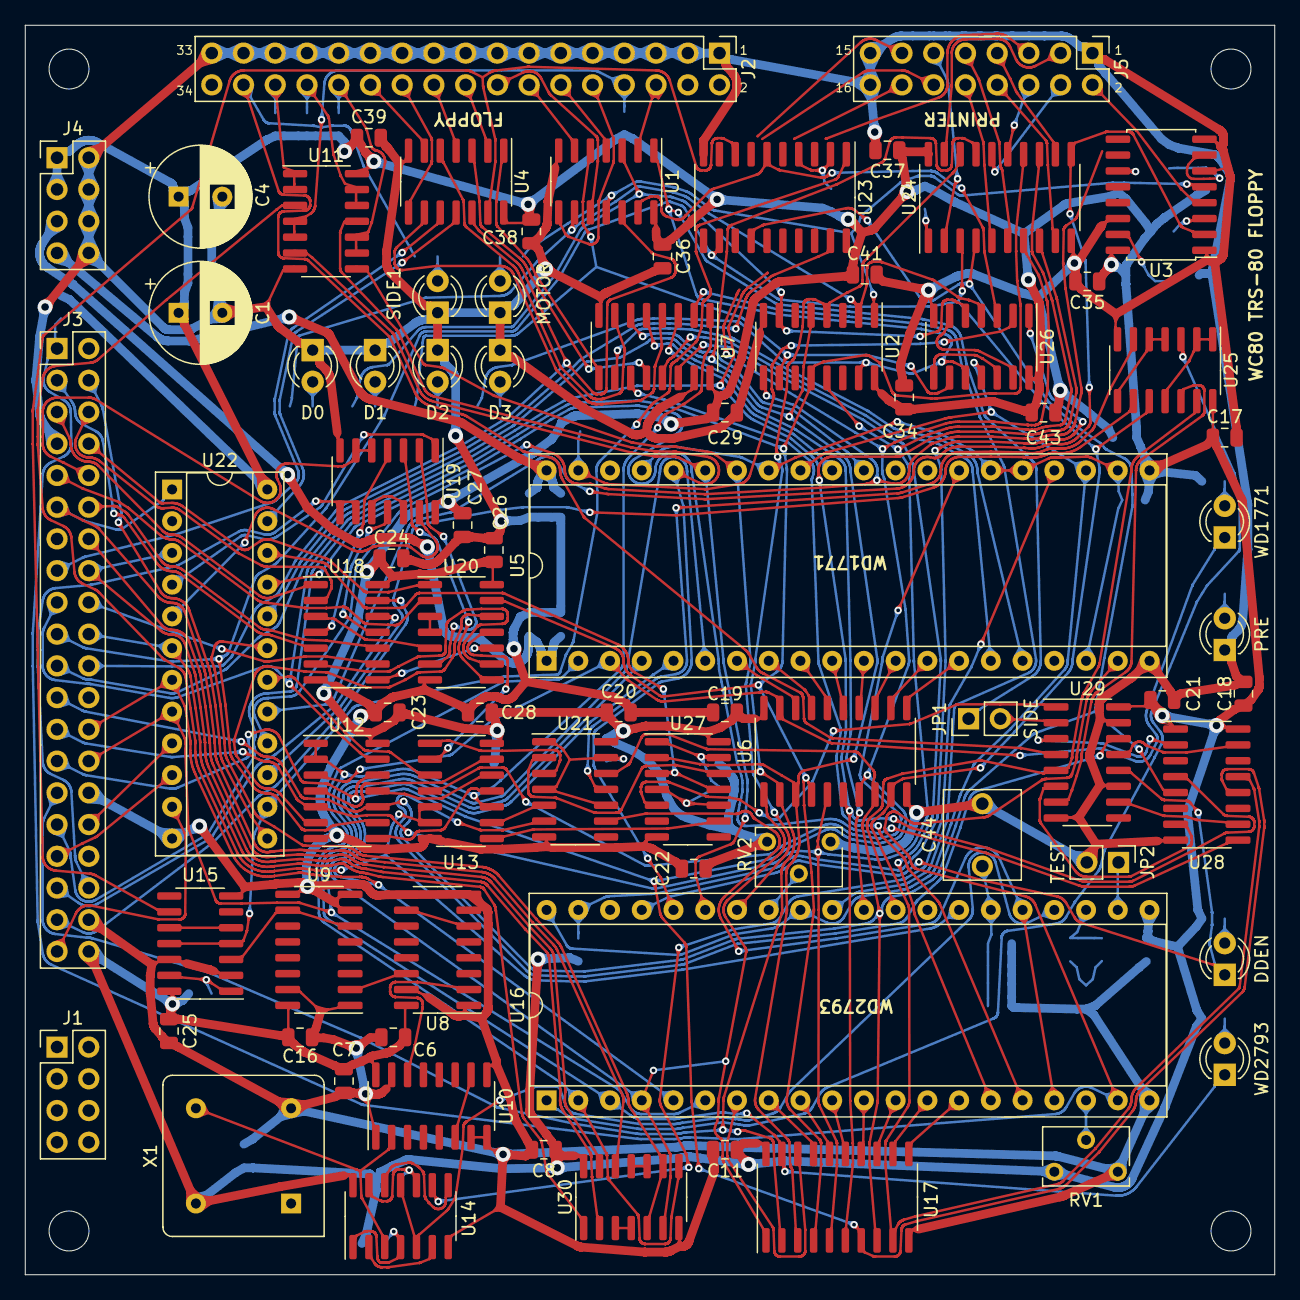
[picture p105: board boards/floppy/rev1-2/main.kicad_pcb from above]

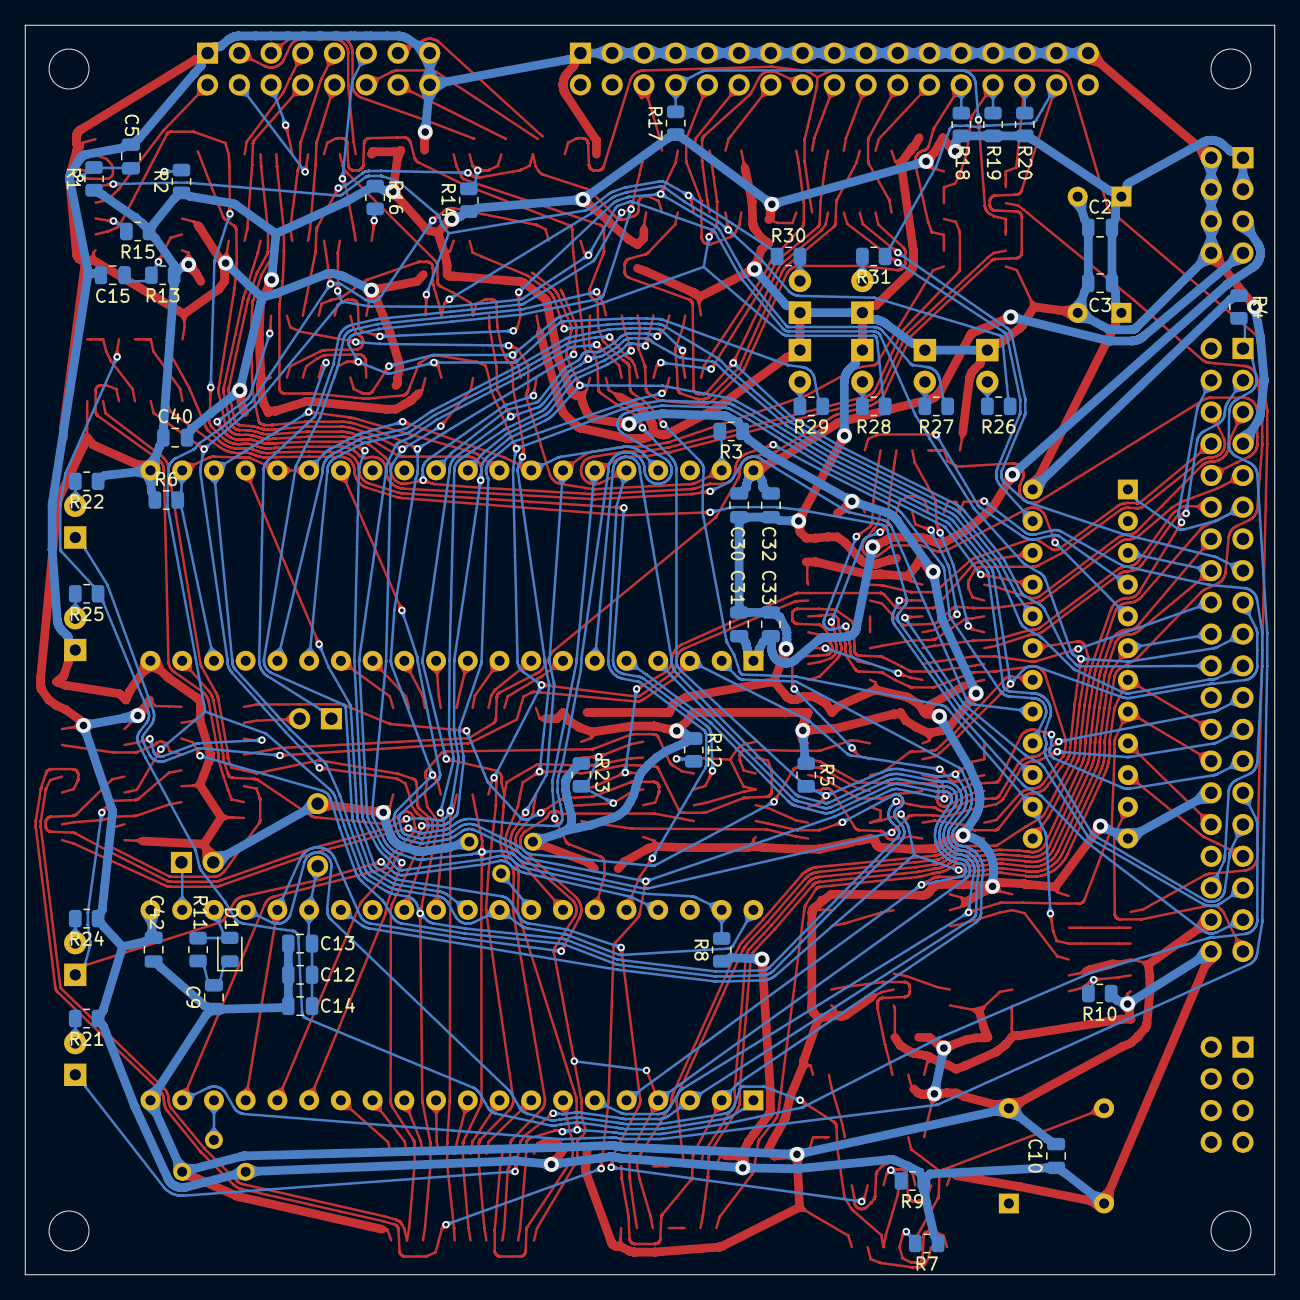
[picture p106: board boards/floppy/rev1-2/main.kicad_pcb from below]

Board: 2 copper layers, 100.0 x 100.0 mm, 130 parts (47 on the bottom side), 198 nets.

Parts:
C1, C4: 470uF; CP_Radial_D8.0mm_P3.50mm
C2, C3, C6, C7, C8, C10, C11, C16, C17, C18, C19, C20, C21, C22, C23, C24, C25, C26, C27, C28, C29, C30, C31, C32, C33, C34, C35, C36, C37, C38, C39, C40, C41, C42, C43: 100n; C_0805_2012Metric
C5: 33uF; C_0805_2012Metric
C9: 150nF; C_0805_2012Metric
C12, C13, C14: 15pF; C_0805_2012Metric
C15: 200p; C_0805_2012Metric
C44: 60pF; C_Rect_L7.0mm_W6.0mm_P5.00mm
D1: DIODE; D_0805_2012Metric
D2: WD2793; LED_D3.0mm
D3: WD1771; LED_D3.0mm
D4: DDEN; LED_D3.0mm
D5: PRE; LED_D3.0mm
D6: D0; LED_D3.0mm
D7: D1; LED_D3.0mm
D8: D2; LED_D3.0mm
D9: D3; LED_D3.0mm
D10: MOTOR; LED_D3.0mm
D11: SIDE1; LED_D3.0mm
J1, J4: Conn_02x04_Odd_Even; PinHeader_2x04_P2.54mm_Vertical
J2: Floppy-header; PinHeader_2x17_P2.54mm_Vertical
J3: TRS80W-header; PinHeader_2x20_P2.54mm_Vertical
J5: Conn_01x16_Male; PinHeader_2x08_P2.54mm_Vertical
JP1: SIDE; PinHeader_1x02_P2.54mm_Vertical
JP2: TEST; PinHeader_1x02_P2.54mm_Vertical
M1, M2, M3, M4: 3mm-mounting-hole; MountingHole_3.2mm_M3_DIN965
R1: 200K; R_0805_2012Metric
R2, R15, R16: 4K7; R_0805_2012Metric
R3, R4, R5, R6, R7, R8, R9, R10, R12, R14, R23: 10K; R_0805_2012Metric
R11: 1K; R_0805_2012Metric
R13: 20K; R_0805_2012Metric
R17, R18, R19, R20: 150; R_0805_2012Metric
R21, R22, R24, R25, R26, R27, R28, R29, R30, R31: 470; R_0805_2012Metric
RV1: 50K; Potentiometer_Bourns_3266W_Vertical
RV2: 10K; Potentiometer_Bourns_3266W_Vertical
U1, U4: 74LS06; SOIC-14_3.9x8.7mm_P1.27mm
U2, U28: 74LS175; SOP-16_3.9x9.9mm_P1.27mm
U3: 74LS123; SO-16_5.3x10.2mm_P1.27mm
U5: WD1771; DIP-40_W15.24mm_Socket
U6: 74LS640; SO-20_5.3x12.6mm_P1.27mm
U7, U29: 74LS157; SOP-16_3.9x9.9mm_P1.27mm
U8, U9, U10: 4518; SOP-16_3.9x9.9mm_P1.27mm
U11: 74LS08; SOIC-14_3.9x8.7mm_P1.27mm
U12, U18, U25, U30: 74LS00; SOIC-14_3.9x8.7mm_P1.27mm
U13, U19: 74LS02; SOIC-14_3.9x8.7mm_P1.27mm
U14, U15, U21, U27: 74LS74; SOIC-14_3.9x8.7mm_P1.27mm
U16: WD2793; DIP-40_W15.24mm_Socket
U17: 74LS245; SO-20_5.3x12.6mm_P1.27mm
U20, U26: 74LS32; SOIC-14_3.9x8.7mm_P1.27mm
U22: ATF22V10C; DIP-24_W7.62mm_Socket
U23: 74LS244; SO-20_5.3x12.6mm_P1.27mm
U24: 74LS273; SO-20_5.3x12.6mm_P1.27mm
X1: CXO_DIP8; Oscillator_DIP-8

Connections:
1MHz: U5.24, U14.9
2MHz: U14.5, U14.11, U16.24
4MHz: U10.2, U14.3, X1.5
37XX: U19.1, U22.4
40Hz: U9.6, U9.10, U15.3
58SEL: U22.15, U25.9
+5V: C1.1, C2.1, C3.1, C4.1, C6.1, C7.1, C8.1, C10.1, C11.1, C16.1, C17.1, C18.1, C19.1, C20.1, C21.1, C22.1, C23.1, C24.1, C25.1, C26.1, C27.1, C28.1, C29.1, C34.1, C35.1, C36.1, C37.1, C38.1, C39.1, C40.1, C41.1, C42.1, C43.1, J3.40, J4.1, J4.3, R1.1, R2.1, R3.1, R4.1, R5.1, R6.1, R7.1, R8.1, R9.1, R10.1, R12.1, R13.1, R14.1, R15.1, R16.1, R17.1, R18.1, R19.1, R20.1, R21.1, R22.1, R23.1, R24.1, RV1.1, RV2.3, U1.14, U2.16, U3.16, U4.14, U5.21, U6.20, U7.16, U8.16, U9.16, U10.16, U11.14, U12.14, U13.14, U14.14, U15.14, U16.21, U17.20, U18.14, U19.14, U20.14, U21.14, U22.24, U23.20, U24.20, U25.14, U26.14, U27.14, U28.1, U29.16, U30.14, X1.8
+12V: C30.1, C32.1, J4.7, U5.40
-5V: C31.1, C33.1, J4.5, U5.1
CENP: R25.1, U16.1, U25.3
D0: R26.1, U1.9, U2.2, U26.4
D1: R27.1, U1.3, U2.7, U26.5
D2: R28.1, U1.5, U2.10, U26.9
D3: JP1.1, R29.1, U1.1, U2.15, U26.10
DFH: U22.21, U28.9
DFL: U2.9, U3.9, U22.16
EFX: U19.13, U22.5
FLOP: U22.19, U30.5, U30.9
FSIDE: J2.32, R31.1, U29.4
F_A0: J3.26, U5.5, U16.5, U22.7
F_A1: J3.28, U5.6, U16.6, U22.8
F_A2: J3.39, U22.11
F_A3: J3.33, U22.10
F_A4: J3.32, U22.9
F_A5: J3.36, U19.8, U19.9
F_A6: J3.37, U18.13
F_A7: J3.35, U18.12
F_A8: J3.12, U18.10
F_A9: J3.18, U18.9
F_A10: J3.3, U18.5
F_A11: J3.10, U19.5, U19.6
F_A12: J3.6, U18.2
F_A13: J3.5, U18.1
F_A14: J3.9, U20.2
F_A15: J3.8, U20.1
F_D0: J3.29, U2.4, U6.2, U17.2, U21.2, U24.18, U27.12
F_D1: J3.21, U2.5, U6.3, U17.3, U24.17, U27.2
F_D2: J3.31, U2.12, U6.4, U17.4, U20.13, U24.14
F_D3: J3.25, U2.13, U6.5, U12.5, U17.5, U24.13
F_D4: J3.17, U6.6, U12.13, U17.6, U23.3, U24.8, U28.4
F_D5: J3.27, U6.7, U12.12, U17.7, U23.5, U24.7, U28.12
F_D6: J3.23, U6.8, U12.10, U17.8, U21.12, U23.7, U23.14, U24.4, U28.5
F_D7: J3.19, U6.9, U12.9, U17.9, U23.9, U23.12, U24.3, U25.10, U28.13
GND: C1.2, C2.2, C3.2, C4.2, C5.2, C6.2, C7.2, C8.2, C9.1, C10.2, C11.2, C12.1, C13.1, C14.1, C15.2, C16.2, C17.2, C18.2, C19.2, C20.2, C21.2, C22.2, C23.2, C24.2, C25.2, C26.2, C27.2, C28.2, C29.2, C30.2, C31.2, C32.2, C33.2, C34.2, C35.2, C36.2, C37.2, C38.2, C39.2, C40.2, C41.2, C42.2, C43.2, C44.2, D5.1, D6.1, D7.1, D8.1, D9.1, D10.1, D11.1, J2.1, J2.3, J2.5, J2.7, J2.9, J2.11, J2.13, J2.15, J2.17, J2.19, J2.21, J2.23, J2.25, J2.27, J2.29, J2.31, J2.33, J3.7, J3.30, J3.38, J4.2, J4.4, J4.6, J4.8, J5.1, J5.15, J5.16, JP2.2, RV1.3, RV2.1, U1.7, U2.8, U3.1, U3.6, U3.8, U3.14, U4.7, U5.20, U6.10, U7.8, U7.15, U8.1, U8.7, U8.8, U8.9, U8.15, U9.1, U9.7, U9.8, U9.9, U9.15, U10.1, U10.7, U10.8, U10.9, U10.15, U11.7, U12.7, U13.7, U14.7, U15.2, U15.7, U15.12, U16.20, U17.10, U18.7, U19.7, U20.7, U21.7, U22.12, U23.10, U24.10, U25.7, U26.7, U27.7, U28.8, U29.8, U29.11, U29.15, U30.7, X1.4
INTCLK: U4.13, U15.9, U23.8
INTFLOP: U1.13, U23.6
M1PRE: U16.29, U25.13, U29.5
M1SIDE: JP1.2, U29.2
MOTOR: R30.1, U1.11, U2.1, U3.5
unnamed: C5.1, R1.2, U3.7
unnamed: C9.2, D1.1, R11.1
unnamed: C12.2, C13.2, C14.2, C44.1, U16.26
unnamed: C15.1, R13.2, U3.15
unnamed: D1.2, R11.2, U16.23
unnamed: D2.2, R21.2
unnamed: D3.2, R22.2
unnamed: D4.2, R24.2
unnamed: D5.2, R25.2
unnamed: D6.2, R26.2
unnamed: D7.2, R27.2
unnamed: D8.2, R28.2
unnamed: D9.2, R29.2
unnamed: D10.2, R30.2
unnamed: D11.2, R31.2
unnamed: J2.6, U1.2
unnamed: J2.8, R17.2
unnamed: J2.10, U1.8
unnamed: J2.12, U1.4
unnamed: J2.14, U1.6
unnamed: J2.16, U1.10
unnamed: J2.18, U4.2
unnamed: J2.20, U4.4
unnamed: J2.22, U4.8
unnamed: J2.24, U4.6
unnamed: J2.26, R18.2
unnamed: J2.28, R19.2
unnamed: J2.30, R20.2, U26.1, U26.2
unnamed: J5.2, U3.4
unnamed: J5.3, U24.19
unnamed: J5.4, U24.16
unnamed: J5.5, U23.17
unnamed: J5.6, U24.15
unnamed: J5.7, U24.12
unnamed: J5.8, U24.9
unnamed: J5.9, U24.6
unnamed: J5.10, U24.5
unnamed: J5.11, U24.2
unnamed: J5.12, U23.11
unnamed: J5.13, U23.13
unnamed: J5.14, U23.15
unnamed: JP2.1, U16.22
unnamed: R2.2, U3.10, U3.11
unnamed: R3.2, U5.39
unnamed: R6.2, U5.18, U5.22, U5.25, U5.26, U5.33, U5.37
unnamed: R7.2, U14.1, U14.4
unnamed: R8.2, U16.39
unnamed: R9.2, U14.10, U14.13
unnamed: R10.2, U15.1, U15.13
unnamed: R12.2, U21.1, U21.4, U21.10, U21.13
unnamed: R14.2, U23.2, U23.4
unnamed: R15.2, U3.3
unnamed: R16.2, U24.1
unnamed: R23.2, U27.1, U27.4, U27.10, U27.13
unnamed: RV1.2, U16.18
unnamed: RV2.2, U16.33
unnamed: U4.1, U7.9
unnamed: U4.3, U7.12
unnamed: U4.5, U7.7
unnamed: U4.9, U7.4
unnamed: U5.7, U6.18
unnamed: U5.8, U6.17
unnamed: U5.9, U6.16
unnamed: U5.10, U6.15
unnamed: U5.11, U6.14
unnamed: U5.12, U6.13
unnamed: U5.13, U6.12
unnamed: U5.14, U6.11
unnamed: U5.15, U7.13
unnamed: U5.16, U7.10
unnamed: U5.30, U7.6
unnamed: U5.31, U7.3
unnamed: U8.6, U8.10
unnamed: U8.14, U9.2
unnamed: U10.6, U10.10
unnamed: U8.2, U10.14
unnamed: U12.4, U13.13
unnamed: U12.6, U20.12
unnamed: U12.8, U13.11
unnamed: U12.11, U13.12
unnamed: U13.1, U21.3
unnamed: U13.2, U20.11
unnamed: U5.27, U13.4
unnamed: U13.5, U13.6, U16.27, U26.3
unnamed: U13.8, U27.9
unnamed: U13.9, U21.5
unnamed: U14.2, U14.6
unnamed: U14.8, U14.12
unnamed: U15.5, U15.10
unnamed: U5.2, U16.2, U30.8
unnamed: U5.4, U6.1, U16.4, U17.1, U30.6
unnamed: U16.7, U17.18
unnamed: U16.8, U17.17
unnamed: U16.9, U17.16
unnamed: U16.10, U17.15
unnamed: U16.11, U17.14
unnamed: U16.12, U17.13
unnamed: U16.13, U17.12
unnamed: U16.14, U17.11
unnamed: U7.14, U16.15
unnamed: U7.11, U16.16
unnamed: U16.17, U16.25, U21.9
unnamed: U7.5, U16.30
unnamed: U7.2, U16.31
unnamed: U5.23, U5.32, U16.32, U16.40, U26.11
unnamed: U5.34, U16.34
unnamed: U5.35, U16.35
unnamed: U5.36, U16.36
unnamed: U18.3, U20.5
unnamed: U18.4, U19.4
unnamed: U18.6, U20.9
unnamed: U18.8, U20.10
unnamed: U18.11, U19.11
unnamed: U19.2, U20.6
unnamed: U19.3, U20.8
unnamed: U19.10, U19.12
unnamed: U20.3, U20.4
unnamed: U21.11, U25.6
unnamed: U4.11, U22.23
unnamed: U25.1, U25.2, U25.11
unnamed: U25.4, U25.5, U25.8
unnamed: U25.12, U29.7
unnamed: U26.8, U26.12
unnamed: U26.6, U26.13
unnamed: U27.5, U29.1
unnamed: U28.2, U29.3
unnamed: U28.7, U29.6
unnamed: U28.10, U29.10
unnamed: U28.15, U29.13
unnamed: U30.3, U30.4
unnamed: U30.10, U30.11
OPT: U22.22, U27.3, U27.11
~37E0~: U15.4, U15.11, U22.14, U23.1
~1771~: D3.1, U5.3, U6.19, U12.3
~2793~: D2.1, R5.2, U7.1, U12.1, U12.2, U13.10, U16.3, U17.19
~CDDEN~: D4.1, U16.37, U29.12
~DENSEL~: U13.3, U22.18
~F_EXMEM~: J3.4, U22.13
~F_INT~: J3.22, U1.12, U4.12
~F_INUSE~: J3.15, U4.10
~F_IN~: J3.20, U22.6, U30.1
~F_MEMRQ~: J3.2, U22.2
~F_OUT~: J3.11, U22.1, U30.12
~F_READ~: J3.16, U22.3, U30.2
~F_SYSRES~: J3.1, R4.2, U5.19, U16.19
~F_WRITE~: J3.14, U30.13
~MDDEN~: U21.6, U29.14
~PRINTREAD~: U22.20, U23.19
~PRINTWRITE~: U3.2, U22.17, U24.11
