alnwlsn/wc-80-archive/boards/keyboard-matrix/keyboard-matrix.kicad_pcb

## KiCad design boards/keyboard-matrix/keyboard-matrix.kicad_pcb (2025-07-11)

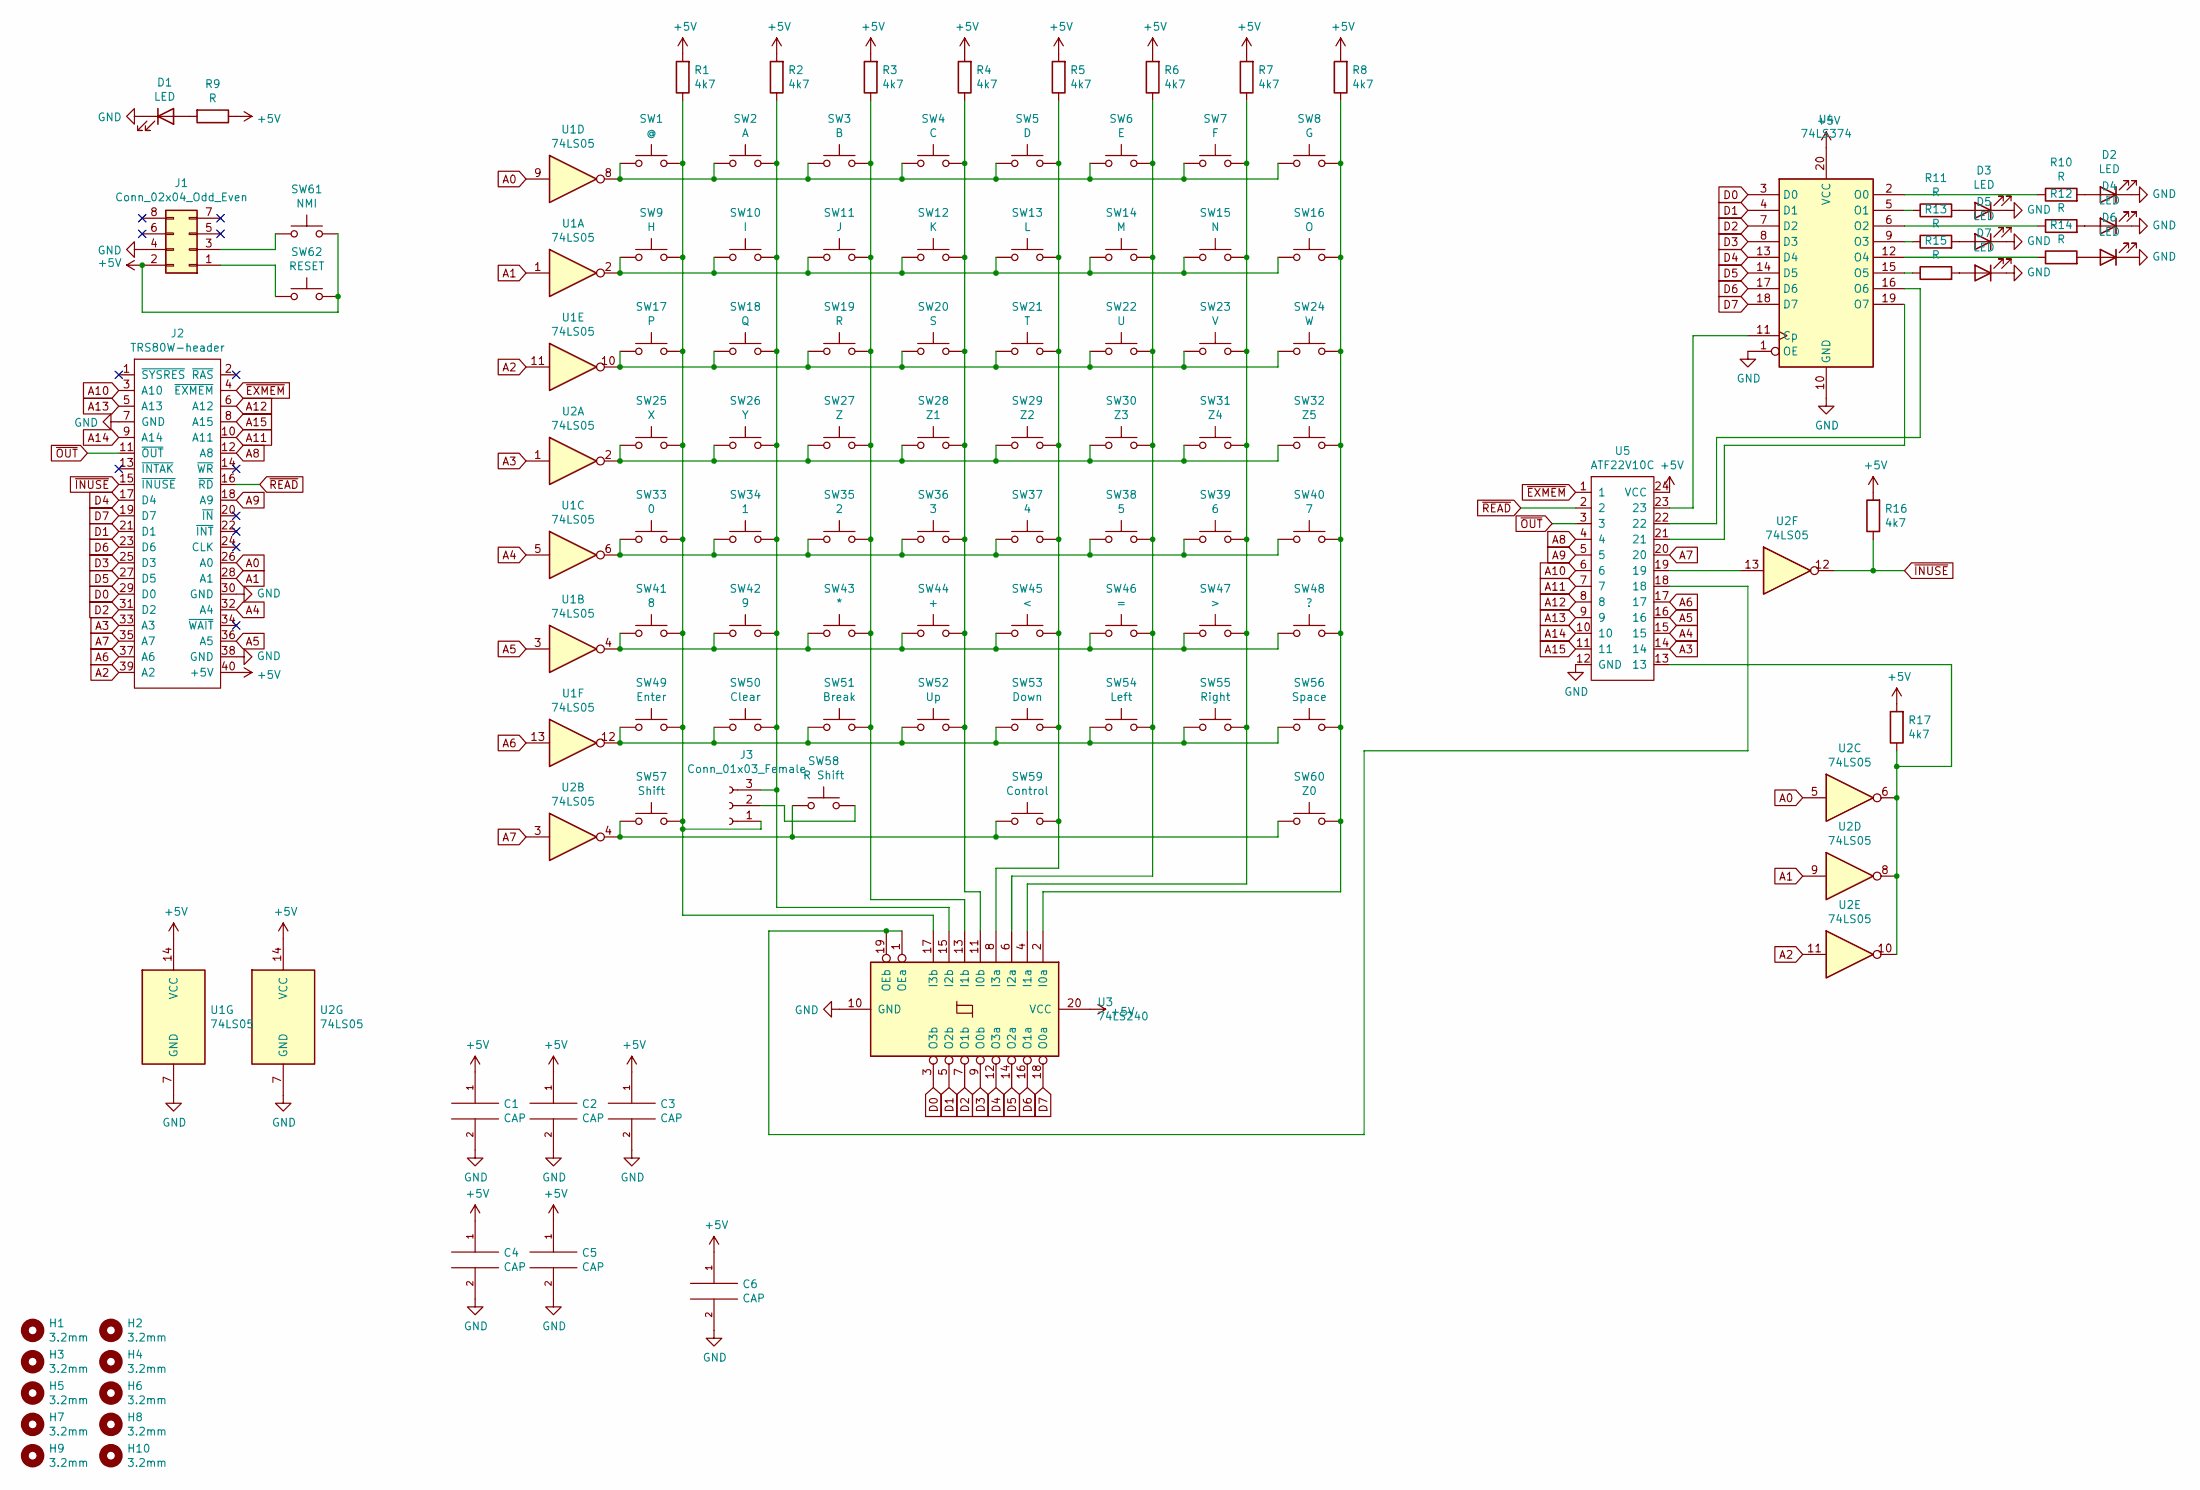
[picture p107: schematic keyboard-matrix.sch]

Parts:
C1, C2, C3, C4, C5: CAP; C_0805_2012Metric
C6: CAP; CP_Radial_D8.0mm_P3.50mm
D1, D2, D3, D4, D5, D6, D7: LED; LED_D3.0mm
H1, H2, H3, H4, H5, H6, H7, H8, H9, H10: 3.2mm; MountingHole_3.2mm_M3_DIN965
J1: Conn_02x04_Odd_Even; PinHeader_2x04_P2.54mm_Vertical
J2: TRS80W-header; PinHeader_2x20_P2.54mm_Vertical
J3: Conn_01x03_Female; SolderJumper-3_P1.3mm_Open_Pad1.0x1.5mm
R1, R2, R3, R4, R5, R6, R7, R8, R16, R17: 4k7; R_0805_2012Metric
R9, R10, R11, R12, R13, R14, R15: R; R_0805_2012Metric
SW1: @; SW_Cherry_MX_1.00u_PCB
SW2: A; SW_Cherry_MX_1.00u_PCB
SW3: B; SW_Cherry_MX_1.00u_PCB
SW4: C; SW_Cherry_MX_1.00u_PCB
SW5: D; SW_Cherry_MX_1.00u_PCB
SW6: E; SW_Cherry_MX_1.00u_PCB
SW7: F; SW_Cherry_MX_1.00u_PCB
SW8: G; SW_Cherry_MX_1.00u_PCB
SW9: H; SW_Cherry_MX_1.00u_PCB
SW10: I; SW_Cherry_MX_1.00u_PCB
SW11: J; SW_Cherry_MX_1.00u_PCB
SW12: K; SW_Cherry_MX_1.00u_PCB
SW13: L; SW_Cherry_MX_1.00u_PCB
SW14: M; SW_Cherry_MX_1.00u_PCB
SW15: N; SW_Cherry_MX_1.00u_PCB
SW16: O; SW_Cherry_MX_1.00u_PCB
SW17: P; SW_Cherry_MX_1.00u_PCB
SW18: Q; SW_Cherry_MX_1.00u_PCB
SW19: R; SW_Cherry_MX_1.00u_PCB
SW20: S; SW_Cherry_MX_1.00u_PCB
SW21: T; SW_Cherry_MX_1.00u_PCB
SW22: U; SW_Cherry_MX_1.00u_PCB
SW23: V; SW_Cherry_MX_1.00u_PCB
SW24: W; SW_Cherry_MX_1.00u_PCB
SW25: X; SW_Cherry_MX_1.00u_PCB
SW26: Y; SW_Cherry_MX_1.00u_PCB
SW27: Z; SW_Cherry_MX_1.00u_PCB
SW28: Z1; SW_Cherry_MX_1.00u_PCB
SW29: Z2; SW_Cherry_MX_1.00u_PCB
SW30: Z3; SW_Cherry_MX_1.00u_PCB
SW31: Z4; SW_Cherry_MX_1.00u_PCB
SW32: Z5; SW_Cherry_MX_1.00u_PCB
SW33: 0; SW_Cherry_MX_1.00u_PCB
SW34: 1; SW_Cherry_MX_1.00u_PCB
SW35: 2; SW_Cherry_MX_1.00u_PCB
SW36: 3; SW_Cherry_MX_1.00u_PCB
SW37: 4; SW_Cherry_MX_1.00u_PCB
SW38: 5; SW_Cherry_MX_1.00u_PCB
SW39: 6; SW_Cherry_MX_1.00u_PCB
SW40: 7; SW_Cherry_MX_1.00u_PCB
SW41: 8; SW_Cherry_MX_1.00u_PCB
SW42: 9; SW_Cherry_MX_1.00u_PCB
SW43: *; SW_Cherry_MX_1.00u_PCB
SW44: +; SW_Cherry_MX_1.00u_PCB
SW45: <; SW_Cherry_MX_1.00u_PCB
SW46: =; SW_Cherry_MX_1.00u_PCB
SW47: >; SW_Cherry_MX_1.00u_PCB
SW48: ?; SW_Cherry_MX_1.00u_PCB
SW49: Enter; SW_Cherry_MX_2.00u_PCB
SW50: Clear; SW_Cherry_MX_1.00u_PCB
SW51: Break; SW_Cherry_MX_1.00u_PCB
SW52: Up; SW_Cherry_MX_1.00u_PCB
SW53: Down; SW_Cherry_MX_1.00u_PCB
SW54: Left; SW_Cherry_MX_1.00u_PCB
SW55: Right; SW_Cherry_MX_1.00u_PCB
SW56: Space; SW_Cherry_MX_6.25u_PCB
SW57: Shift; SW_Cherry_MX_1.50u_PCB
SW58: R Shift; SW_Cherry_MX_1.50u_Plate
SW59: Control; SW_Cherry_MX_1.00u_PCB
SW60: Z0; SW_Cherry_MX_1.00u_PCB
SW61: NMI; SW_Cherry_MX_1.00u_PCB
SW62: RESET; SW_Cherry_MX_1.00u_PCB
U1, U2: 74LS05; DIP-14_W7.62mm
U3: 74LS240; DIP-20_W7.62mm
U4: 74LS374; DIP-20_W7.62mm
U5: ATF22V10C; DIP-24_W7.62mm

Connections:
+5V: C1.1, C2.1, C3.1, C4.1, C5.1, C6.1, J1.2, J2.40 (+5V), R1.2, R2.2, R3.2, R4.2, R5.2, R6.2, R7.2, R8.2, R9.1, R16.2, R17.2, SW61.2, SW62.2, U1.14 (VCC), U2.14 (VCC), U3.20 (VCC), U4.20 (VCC), U5.24 (VCC)
A0: J2.26 (A0), U1.9, U2.5
A1: J2.28 (A1), U1.1, U2.9
A2: J2.39 (A2), U1.11, U2.11
A3: J2.33 (A3), U2.1, U5.14
A4: J2.32 (A4), U1.5, U5.15
A5: J2.36 (A5), U1.3, U5.16
A6: J2.37 (A6), U1.13, U5.17
A7: J2.35 (A7), U2.3, U5.20
A8: J2.12 (A8), U5.4
A9: J2.18 (A9), U5.5
A10: J2.3 (A10), U5.6
A11: J2.10 (A11), U5.7
A12: J2.6 (A12), U5.8
A13: J2.5 (A13), U5.9
A14: J2.9 (A14), U5.10
A15: J2.8 (A15), U5.11
D0: J2.29 (D0), U3.3 (O3b), U4.3 (D0)
D1: J2.21 (D1), U3.5 (O2b), U4.4 (D1)
D2: J2.31 (D2), U3.7 (O1b), U4.7 (D2)
D3: J2.25 (D3), U3.9 (O0b), U4.8 (D3)
D4: J2.17 (D4), U3.12 (O3a), U4.13 (D4)
D5: J2.27 (D5), U3.14 (O2a), U4.14 (D5)
D6: J2.23 (D6), U3.16 (O1a), U4.17 (D6)
D7: J2.19 (D7), U3.18 (O0a), U4.18 (D7)
GND: C1.2, C2.2, C3.2, C4.2, C5.2, C6.2, D1.1 (K), D2.1 (K), D3.1 (K), D4.1 (K), D5.1 (K), D6.1 (K), D7.1 (K), J1.4, J2.7 (GND), J2.30 (GND), J2.38 (GND), U1.7 (GND), U2.7 (GND), U3.10 (GND), U4.1 (OE), U4.10 (GND), U5.12 (GND)
unnamed: D1.2 (A), R9.2
unnamed: D2.2 (A), R10.2
unnamed: D3.2 (A), R11.2
unnamed: D4.2 (A), R12.2
unnamed: D5.2 (A), R13.2
unnamed: D6.2 (A), R14.2
unnamed: D7.2 (A), R15.2
unnamed: J1.1, SW62.1
unnamed: J1.3, SW61.1
unnamed: J3.1, R1.1, SW1.2, SW9.2, SW17.2, SW25.2, SW33.2, SW41.2, SW49.2, SW57.2, U3.17 (I3b)
unnamed: J3.2, SW58.2
unnamed: J3.3, R2.1, SW2.2, SW10.2, SW18.2, SW26.2, SW34.2, SW42.2, SW50.2, U3.15 (I2b)
unnamed: R3.1, SW3.2, SW11.2, SW19.2, SW27.2, SW35.2, SW43.2, SW51.2, U3.13 (I1b)
unnamed: R4.1, SW4.2, SW12.2, SW20.2, SW28.2, SW36.2, SW44.2, SW52.2, U3.11 (I0b)
unnamed: R5.1, SW5.2, SW13.2, SW21.2, SW29.2, SW37.2, SW45.2, SW53.2, SW59.2, U3.8 (I3a)
unnamed: R6.1, SW6.2, SW14.2, SW22.2, SW30.2, SW38.2, SW46.2, SW54.2, U3.6 (I2a)
unnamed: R7.1, SW7.2, SW15.2, SW23.2, SW31.2, SW39.2, SW47.2, SW55.2, U3.4 (I1a)
unnamed: R8.1, SW8.2, SW16.2, SW24.2, SW32.2, SW40.2, SW48.2, SW56.2, SW60.2, U3.2 (I0a)
unnamed: R10.1, U4.2 (O0)
unnamed: R11.1, U4.5 (O1)
unnamed: R12.1, U4.6 (O2)
unnamed: R13.1, U4.9 (O3)
unnamed: R14.1, U4.12 (O4)
unnamed: R15.1, U4.15 (O5)
unnamed: R17.1, U2.6, U2.8, U2.10, U5.13
unnamed: SW1.1, SW2.1, SW3.1, SW4.1, SW5.1, SW6.1, SW7.1, SW8.1, U1.8
unnamed: SW9.1, SW10.1, SW11.1, SW12.1, SW13.1, SW14.1, SW15.1, SW16.1, U1.2
unnamed: SW17.1, SW18.1, SW19.1, SW20.1, SW21.1, SW22.1, SW23.1, SW24.1, U1.10
unnamed: SW25.1, SW26.1, SW27.1, SW28.1, SW29.1, SW30.1, SW31.1, SW32.1, U2.2
unnamed: SW33.1, SW34.1, SW35.1, SW36.1, SW37.1, SW38.1, SW39.1, SW40.1, U1.6
unnamed: SW41.1, SW42.1, SW43.1, SW44.1, SW45.1, SW46.1, SW47.1, SW48.1, U1.4
unnamed: SW49.1, SW50.1, SW51.1, SW52.1, SW53.1, SW54.1, SW55.1, SW56.1, U1.12
unnamed: SW57.1, SW58.1, SW59.1, SW60.1, U2.4
unnamed: U2.13, U5.19
unnamed: U3.1 (OEa), U3.19 (OEb), U5.18
unnamed: U4.11 (Cp), U5.23
unnamed: U4.16 (O6), U5.22
unnamed: U4.19 (O7), U5.21
~EXMEM~: J2.4 (~EXMEM~), U5.1
~INUSE~: J2.15 (~INUSE~), R16.1, U2.12
~OUT~: J2.11 (~OUT~), U5.3
~READ~: J2.16 (~RD~), U5.2

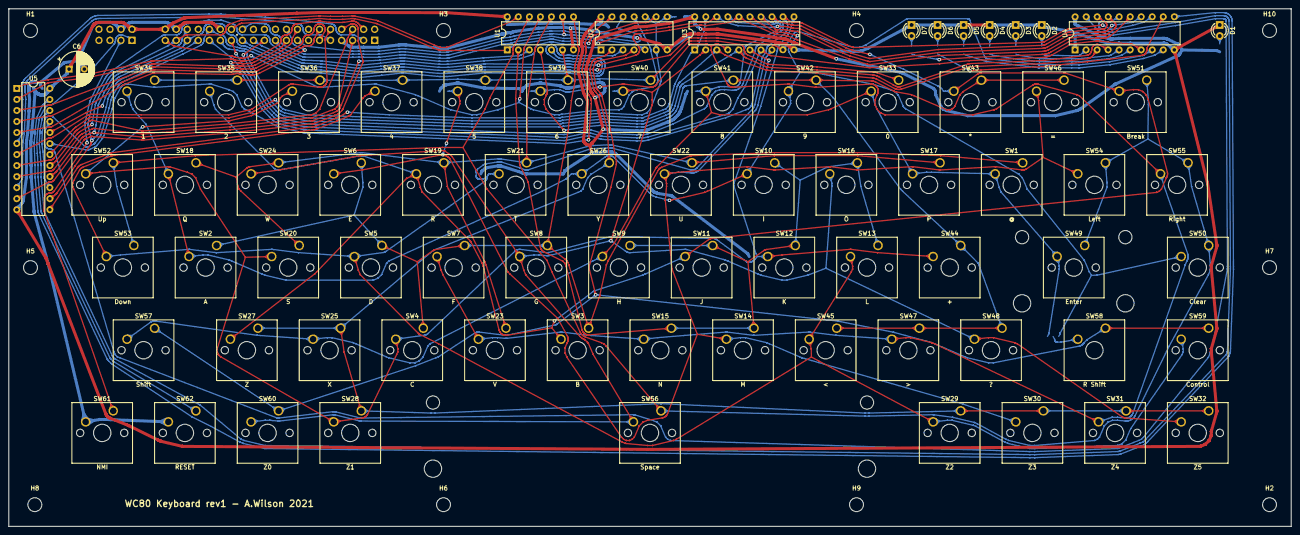
[picture p108: board boards/keyboard-matrix/keyboard-matrix.kicad_pcb from above]

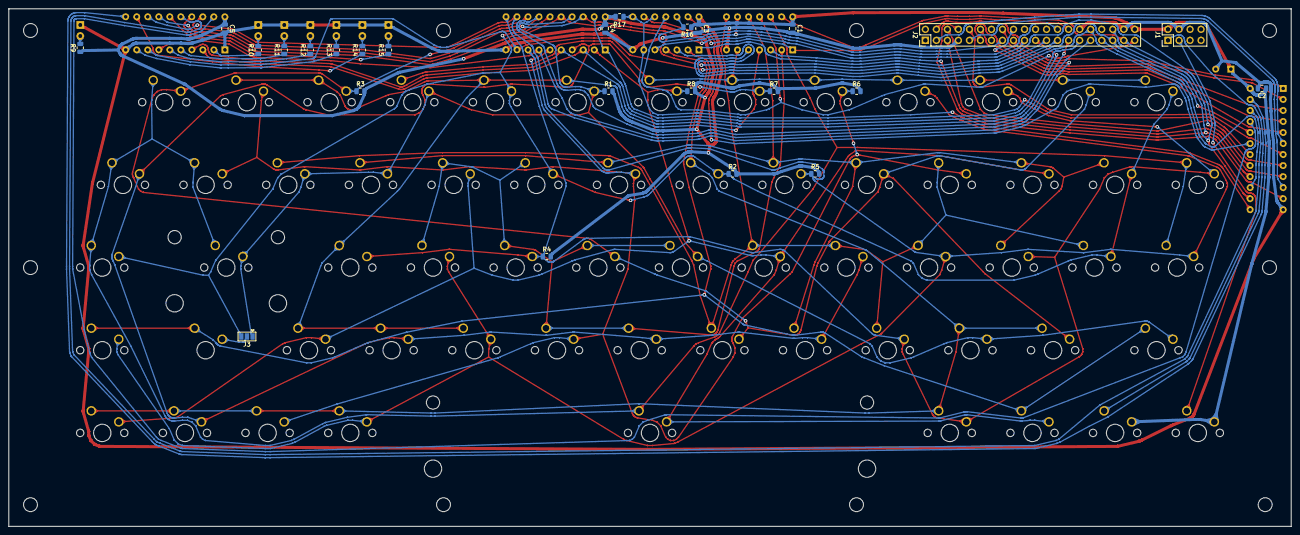
[picture p109: board boards/keyboard-matrix/keyboard-matrix.kicad_pcb from below]

Board: 2 copper layers, 295.5 x 119.2 mm, 110 parts (25 on the bottom side), 68 nets.
