alnwlsn/wc-80-archive/boards/ledboard2/main.kicad_pcb

## KiCad design boards/ledboard2/main.kicad_pcb (2025-07-11)

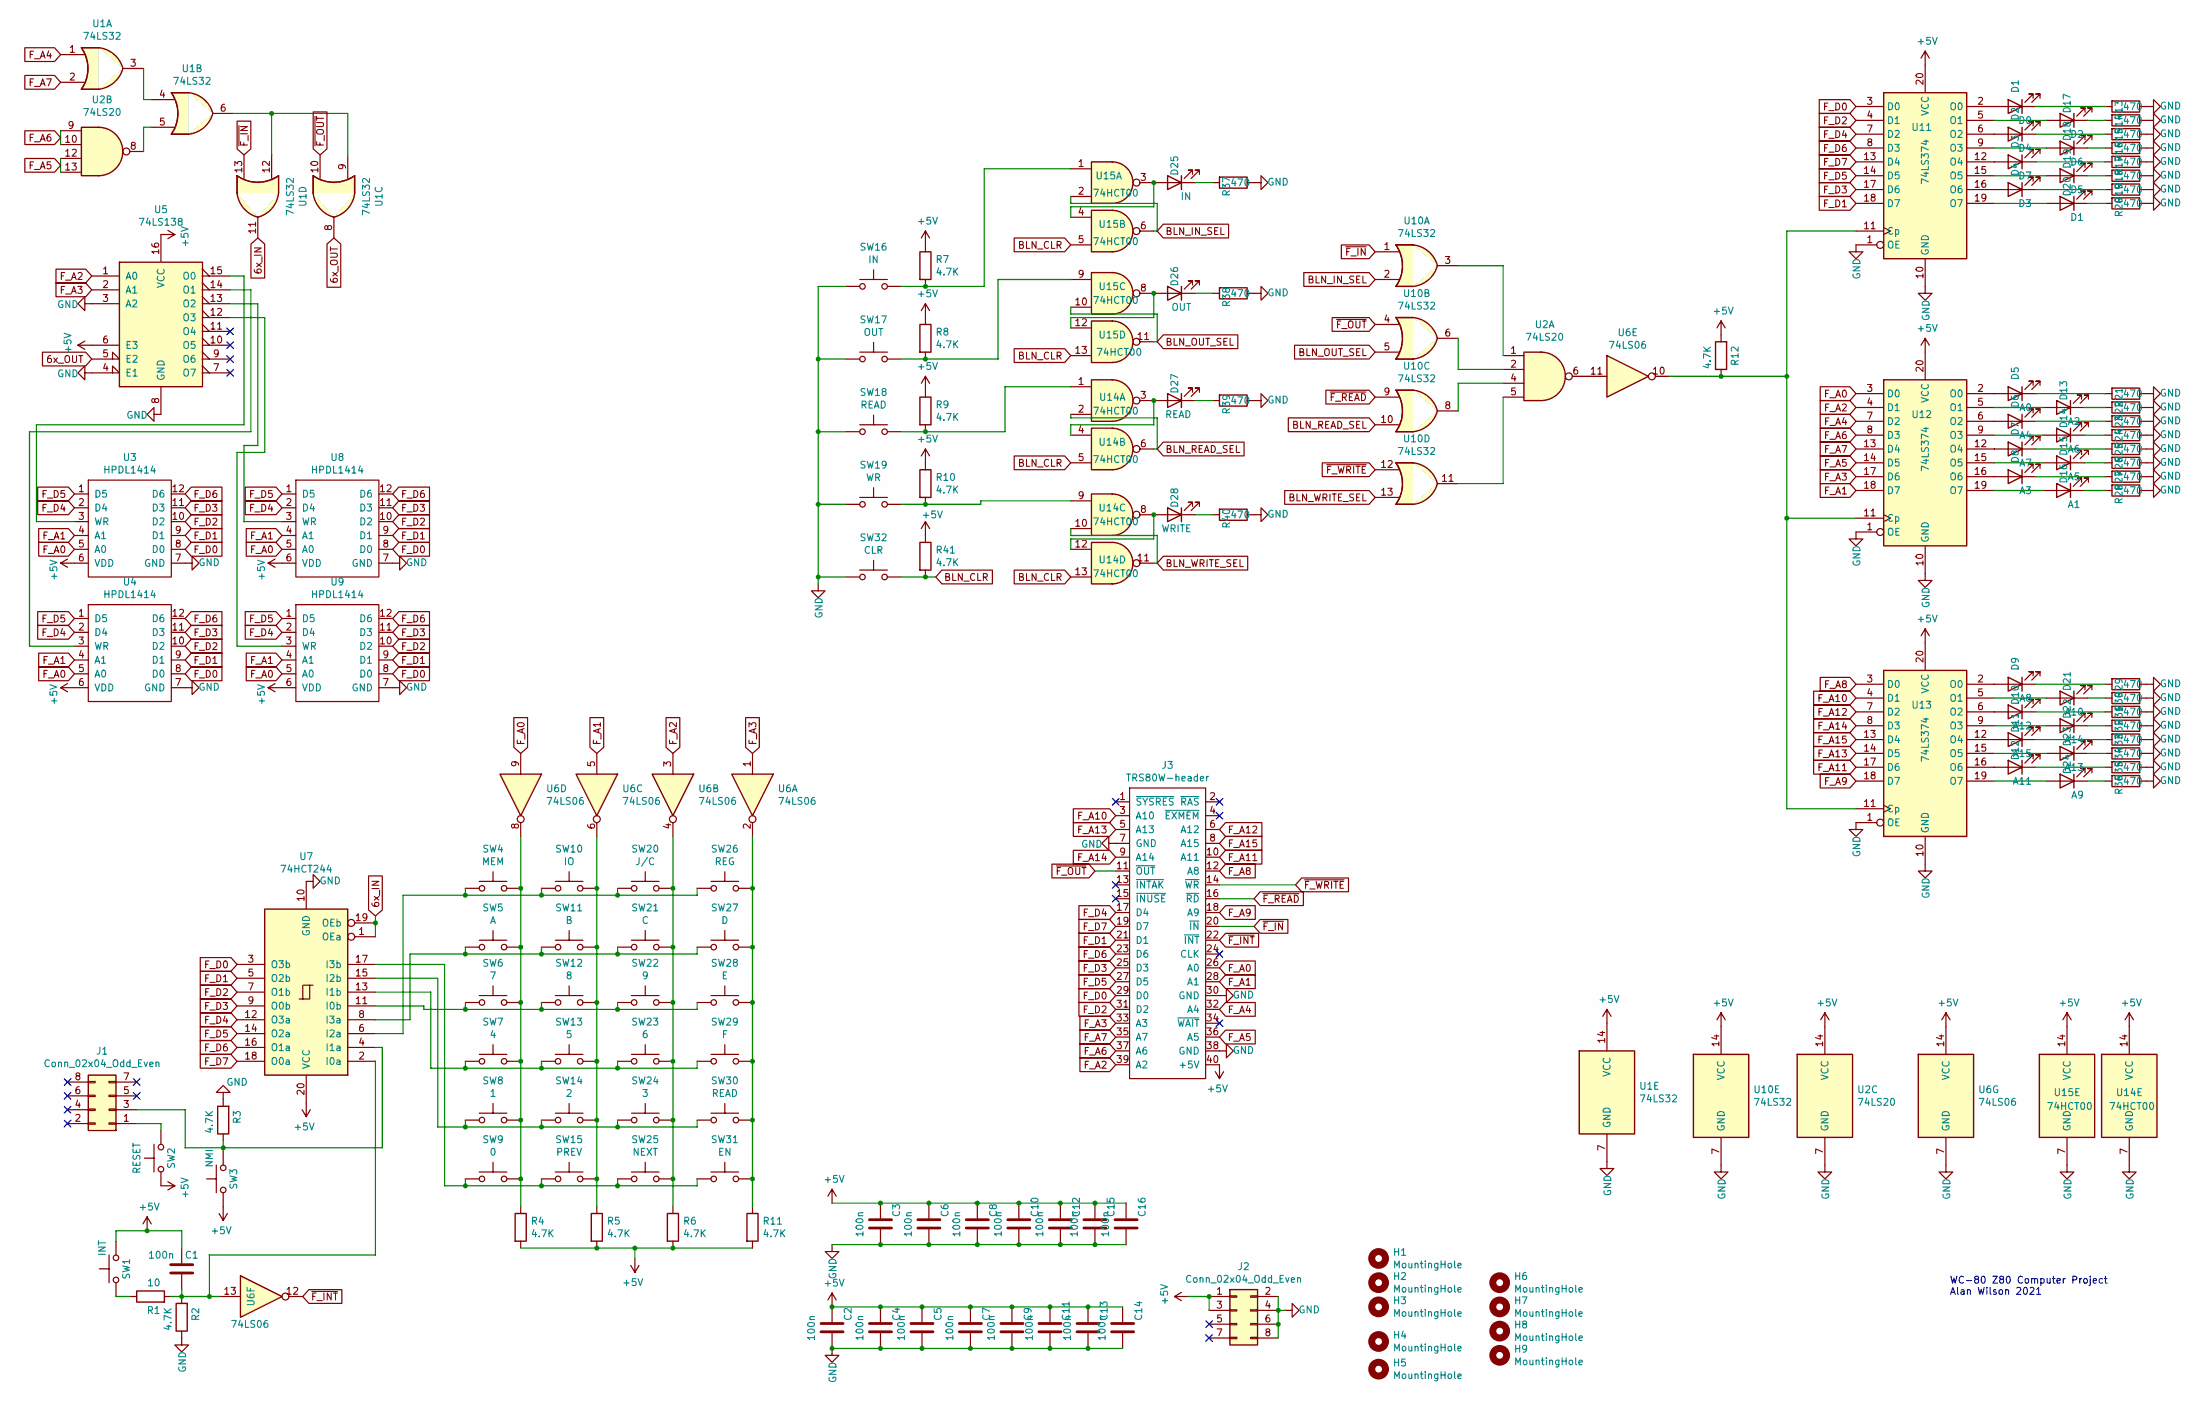
[picture p110: schematic main.kicad_sch]

Parts:
C1, C2, C3, C4, C5, C6, C7, C8, C9, C10, C11, C12, C13, C14, C15, C16: 100n; C_0805_2012Metric
D1: D0; LED_D3.0mm_FlatTop
D2: D4; LED_D3.0mm_FlatTop
D3: D7; LED_D3.0mm_FlatTop
D4: D3; LED_D3.0mm_FlatTop
D5: A0; LED_D3.0mm_FlatTop
D6: A4; LED_D3.0mm_FlatTop
D7: A7; LED_D3.0mm_FlatTop
D8: A3; LED_D3.0mm_FlatTop
D9: A8; LED_D3.0mm_FlatTop
D10: A12; LED_D3.0mm_FlatTop
D11: A15; LED_D3.0mm_FlatTop
D12: A11; LED_D3.0mm_FlatTop
D13: A2; LED_D3.0mm_FlatTop
D14: A6; LED_D3.0mm_FlatTop
D15: A5; LED_D3.0mm_FlatTop
D16: A1; LED_D3.0mm_FlatTop
D17: D2; LED_D3.0mm_FlatTop
D18: D6; LED_D3.0mm_FlatTop
D19: D5; LED_D3.0mm_FlatTop
D20: D1; LED_D3.0mm_FlatTop
D21: A10; LED_D3.0mm_FlatTop
D22: A14; LED_D3.0mm_FlatTop
D23: A13; LED_D3.0mm_FlatTop
D24: A9; LED_D3.0mm_FlatTop
D25: IN; LED_D3.0mm_FlatTop
D26: OUT; LED_D3.0mm_FlatTop
D27: READ; LED_D3.0mm_FlatTop
D28: WRITE; LED_D3.0mm_FlatTop
H1, H2, H3, H4, H5, H6, H7, H8, H9: MountingHole; MountingHole_3.2mm_M3_DIN965
J1, J2: Conn_02x04_Odd_Even; PinHeader_2x04_P2.54mm_Vertical
J3: TRS80W-header; PinHeader_2x20_P2.54mm_Vertical
R1: 10; R_0805_2012Metric
R2, R3, R4, R5, R6, R7, R8, R9, R10, R11, R12, R41: 4.7K; R_0805_2012Metric
R13, R14, R15, R16, R17, R18, R19, R20, R21, R22, R23, R24, R25, R26, R27, R28, R29, R30, R31, R32, R33, R34, R35, R36, R37, R38, R39, R40: 470; R_0805_2012Metric
SW1: INT; DTSL-6
SW2: RESET; DTSL-6
SW3: NMI; DTSL-6
SW4: MEM; DTSL-6
SW5: A; DTSL-6
SW6: 7; DTSL-6
SW7: 4; DTSL-6
SW8: 1; DTSL-6
SW9: 0; DTSL-6
SW10: IO; DTSL-6
SW11: B; DTSL-6
SW12: 8; DTSL-6
SW13: 5; DTSL-6
SW14: 2; DTSL-6
SW15: PREV; DTSL-6
SW16: IN; DTSL-6
SW17: OUT; DTSL-6
SW18, SW30: READ; DTSL-6
SW19: WR; DTSL-6
SW20: J/C; DTSL-6
SW21: C; DTSL-6
SW22: 9; DTSL-6
SW23: 6; DTSL-6
SW24: 3; DTSL-6
SW25: NEXT; DTSL-6
SW26: REG; DTSL-6
SW27: D; DTSL-6
SW28: E; DTSL-6
SW29: F; DTSL-6
SW31: EN; DTSL-6
SW32: CLR; DTSL-6
U1, U10: 74LS32; SOIC-14_3.9x8.7mm_P1.27mm
U2: 74LS20; SOIC-14_3.9x8.7mm_P1.27mm
U3, U4, U8, U9: HPDL1414; DIP-24_W15.24mm_Socket
U5: 74LS138; SOIC-16_3.9x9.9mm_P1.27mm
U6: 74LS06; SOIC-14_3.9x8.7mm_P1.27mm
U7: 74HCT244; SOIC-20W_7.5x12.8mm_P1.27mm
U11, U12, U13: 74LS374; SOIC-20W_7.5x12.8mm_P1.27mm
U14, U15: 74HCT00; SOIC-14_3.9x8.7mm_P1.27mm

Connections:
6x_IN: U1.11, U7.1 (OEa), U7.19 (OEb)
6x_OUT: U1.8, U5.5 (E2)
+5V: C1.2, C2.1, C3.1, C4.1, C5.1, C6.1, C7.1, C8.1, C9.1, C10.1, C11.1, C12.1, C13.1, C14.1, C15.1, C16.1, J2.1, J2.3, J3.40 (+5V), R4.2, R5.2, R6.2, R7.1, R8.1, R9.1, R10.1, R11.2, R12.2, R41.1, SW1.2, SW2.1, SW3.1, U1.14 (VCC), U2.14 (VCC), U3.6 (VDD), U4.6 (VDD), U5.6 (E3), U5.16 (VCC), U6.14 (VCC), U7.20 (VCC), U8.6 (VDD), U9.6 (VDD), U10.14 (VCC), U11.20 (VCC), U12.20 (VCC), U13.20 (VCC), U14.14 (VCC), U15.14 (VCC)
BLN_CLR: R41.2, SW32.2, U14.5, U14.13, U15.5, U15.13
BLN_IN_SEL: U10.2, U15.2, U15.6
BLN_OUT_SEL: U10.5, U15.10, U15.11
BLN_READ_SEL: U10.10, U14.2, U14.6
BLN_WRITE_SEL: U10.13, U14.10, U14.11
F_A0: J3.26 (A0), U3.5 (A0), U4.5 (A0), U6.9, U8.5 (A0), U9.5 (A0), U12.3 (D0)
F_A1: J3.28 (A1), U3.4 (A1), U4.4 (A1), U6.5, U8.4 (A1), U9.4 (A1), U12.18 (D7)
F_A2: J3.39 (A2), U5.1 (A0), U6.3, U12.4 (D1)
F_A3: J3.33 (A3), U5.2 (A1), U6.1, U12.17 (D6)
F_A4: J3.32 (A4), U1.1, U12.7 (D2)
F_A5: J3.36 (A5), U2.12, U2.13, U12.14 (D5)
F_A6: J3.37 (A6), U2.9, U2.10, U12.8 (D3)
F_A7: J3.35 (A7), U1.2, U12.13 (D4)
F_A8: J3.12 (A8), U13.3 (D0)
F_A9: J3.18 (A9), U13.18 (D7)
F_A10: J3.3 (A10), U13.4 (D1)
F_A11: J3.10 (A11), U13.17 (D6)
F_A12: J3.6 (A12), U13.7 (D2)
F_A13: J3.5 (A13), U13.14 (D5)
F_A14: J3.9 (A14), U13.8 (D3)
F_A15: J3.8 (A15), U13.13 (D4)
F_D0: J3.29 (D0), U3.8 (D0), U4.8 (D0), U7.3 (O3b), U8.8 (D0), U9.8 (D0), U11.3 (D0)
F_D1: J3.21 (D1), U3.9 (D1), U4.9 (D1), U7.5 (O2b), U8.9 (D1), U9.9 (D1), U11.18 (D7)
F_D2: J3.31 (D2), U3.10 (D2), U4.10 (D2), U7.7 (O1b), U8.10 (D2), U9.10 (D2), U11.4 (D1)
F_D3: J3.25 (D3), U3.11 (D3), U4.11 (D3), U7.9 (O0b), U8.11 (D3), U9.11 (D3), U11.17 (D6)
F_D4: J3.17 (D4), U3.2 (D4), U4.2 (D4), U7.12 (O3a), U8.2 (D4), U9.2 (D4), U11.7 (D2)
F_D5: J3.27 (D5), U3.1 (D5), U4.1 (D5), U7.14 (O2a), U8.1 (D5), U9.1 (D5), U11.14 (D5)
F_D6: J3.23 (D6), U3.12 (D6), U4.12 (D6), U7.16 (O1a), U8.12 (D6), U9.12 (D6), U11.8 (D3)
F_D7: J3.19 (D7), U7.18 (O0a), U11.13 (D4)
GND: C2.2, C3.2, C4.2, C5.2, C6.2, C7.2, C8.2, C9.2, C10.2, C11.2, C12.2, C13.2, C14.2, C15.2, C16.2, J2.2, J2.4, J2.6, J2.8, J3.7 (GND), J3.30 (GND), J3.38 (GND), R2.1, R3.2, R13.1, R14.1, R15.1, R16.1, R17.1, R18.1, R19.1, R20.1, R21.1, R22.1, R23.1, R24.1, R25.1, R26.1, R27.1, R28.1, R29.1, R30.1, R31.1, R32.1, R33.1, R34.1, R35.1, R36.1, R37.1, R38.1, R39.1, R40.1, SW16.1, SW17.1, SW18.1, SW19.1, SW32.1, U1.7 (GND), U2.7 (GND), U3.7 (GND), U4.7 (GND), U5.3 (A2), U5.4 (E1), U5.8 (GND), U6.7 (GND), U7.10 (GND), U8.7 (GND), U9.7 (GND), U10.7 (GND), U11.1 (OE), U11.10 (GND), U12.1 (OE), U12.10 (GND), U13.1 (OE), U13.10 (GND), U14.7 (GND), U15.7 (GND)
unnamed: D1.2 (A), U11.2 (O0)
unnamed: D1.1 (K), R13.2
unnamed: D2.2 (A), U11.6 (O2)
unnamed: D2.1 (K), R15.2
unnamed: D3.2 (A), U11.12 (O4)
unnamed: D3.1 (K), R17.2
unnamed: D4.2 (A), U11.16 (O6)
unnamed: D4.1 (K), R19.2
unnamed: D5.2 (A), U12.2 (O0)
unnamed: D5.1 (K), R21.2
unnamed: D6.2 (A), U12.6 (O2)
unnamed: D6.1 (K), R23.2
unnamed: D7.2 (A), U12.12 (O4)
unnamed: D7.1 (K), R25.2
unnamed: D8.2 (A), U12.16 (O6)
unnamed: D8.1 (K), R27.2
unnamed: D9.2 (A), U13.2 (O0)
unnamed: D9.1 (K), R29.2
unnamed: D10.2 (A), U13.6 (O2)
unnamed: D10.1 (K), R31.2
unnamed: D11.2 (A), U13.12 (O4)
unnamed: D11.1 (K), R33.2
unnamed: D12.2 (A), U13.16 (O6)
unnamed: D12.1 (K), R35.2
unnamed: D13.2 (A), U12.5 (O1)
unnamed: D13.1 (K), R22.2
unnamed: D14.2 (A), U12.9 (O3)
unnamed: D14.1 (K), R24.2
unnamed: D15.2 (A), U12.15 (O5)
unnamed: D15.1 (K), R26.2
unnamed: D16.2 (A), U12.19 (O7)
unnamed: D16.1 (K), R28.2
unnamed: D17.2 (A), U11.5 (O1)
unnamed: D17.1 (K), R14.2
unnamed: D18.2 (A), U11.9 (O3)
unnamed: D18.1 (K), R16.2
unnamed: D19.2 (A), U11.15 (O5)
unnamed: D19.1 (K), R18.2
unnamed: D20.2 (A), U11.19 (O7)
unnamed: D20.1 (K), R20.2
unnamed: D21.2 (A), U13.5 (O1)
unnamed: D21.1 (K), R30.2
unnamed: D22.2 (A), U13.9 (O3)
unnamed: D22.1 (K), R32.2
unnamed: D23.2 (A), U13.15 (O5)
unnamed: D23.1 (K), R34.2
unnamed: D24.2 (A), U13.19 (O7)
unnamed: D24.1 (K), R36.2
unnamed: D25.2 (A), U15.3, U15.4
unnamed: D25.1 (K), R37.2
unnamed: D26.2 (A), U15.8, U15.12
unnamed: D26.1 (K), R38.2
unnamed: D27.2 (A), U14.3, U14.4
unnamed: D27.1 (K), R39.2
unnamed: D28.2 (A), U14.8, U14.12
unnamed: D28.1 (K), R40.2
unnamed: J1.1, SW2.2
unnamed: J1.3, R3.1, SW3.2, U7.4 (I1a)
unnamed: R1.1, SW1.1
unnamed: R4.1, SW4.2, SW5.2, SW6.2, SW7.2, SW8.2, SW9.2, U6.8
unnamed: R5.1, SW10.2, SW11.2, SW12.2, SW13.2, SW14.2, SW15.2, U6.6
unnamed: R6.1, SW20.2, SW21.2, SW22.2, SW23.2, SW24.2, SW25.2, U6.4
unnamed: R7.2, SW16.2, U15.1
unnamed: R8.2, SW17.2, U15.9
unnamed: R9.2, SW18.2, U14.1
unnamed: R10.2, SW19.2, U14.9
unnamed: R11.1, SW26.2, SW27.2, SW28.2, SW29.2, SW30.2, SW31.2, U6.2
unnamed: U1.3, U1.4
unnamed: U1.5, U2.8
unnamed: U1.6, U1.9, U1.12
unnamed: U2.6, U6.11
unnamed: U3.3 (WR), U5.15 (O0)
unnamed: U4.3 (WR), U5.14 (O1)
unnamed: U5.13 (O2), U8.3 (WR)
unnamed: U5.12 (O3), U9.3 (WR)
unnamed: C1.1, R1.2, R2.2, U6.13, U7.2 (I0a)
unnamed: SW6.1, SW12.1, SW22.1, SW28.1, U7.11 (I0b)
unnamed: SW7.1, SW13.1, SW23.1, SW29.1, U7.13 (I1b)
unnamed: SW4.1, SW10.1, SW20.1, SW26.1, U7.6 (I2a)
unnamed: SW8.1, SW14.1, SW24.1, SW30.1, U7.15 (I2b)
unnamed: SW5.1, SW11.1, SW21.1, SW27.1, U7.8 (I3a)
unnamed: SW9.1, SW15.1, SW25.1, SW31.1, U7.17 (I3b)
unnamed: U2.1, U10.3
unnamed: U2.2, U10.6
unnamed: U2.4, U10.8
unnamed: U2.5, U10.11
unnamed: R12.1, U6.10, U11.11 (Cp), U12.11 (Cp), U13.11 (Cp)
~F_INT: J3.22 (~INT), U6.12
~F_IN: J3.20 (~IN), U1.13, U10.1
~F_OUT: J3.11 (~OUT), U1.10, U10.4
~F_READ: J3.16 (~RD), U10.9
~F_WRITE: J3.14 (~WR), U10.12

Notes on the sheet:
WC-80 Z80 Computer Project Alan Wilson 2021

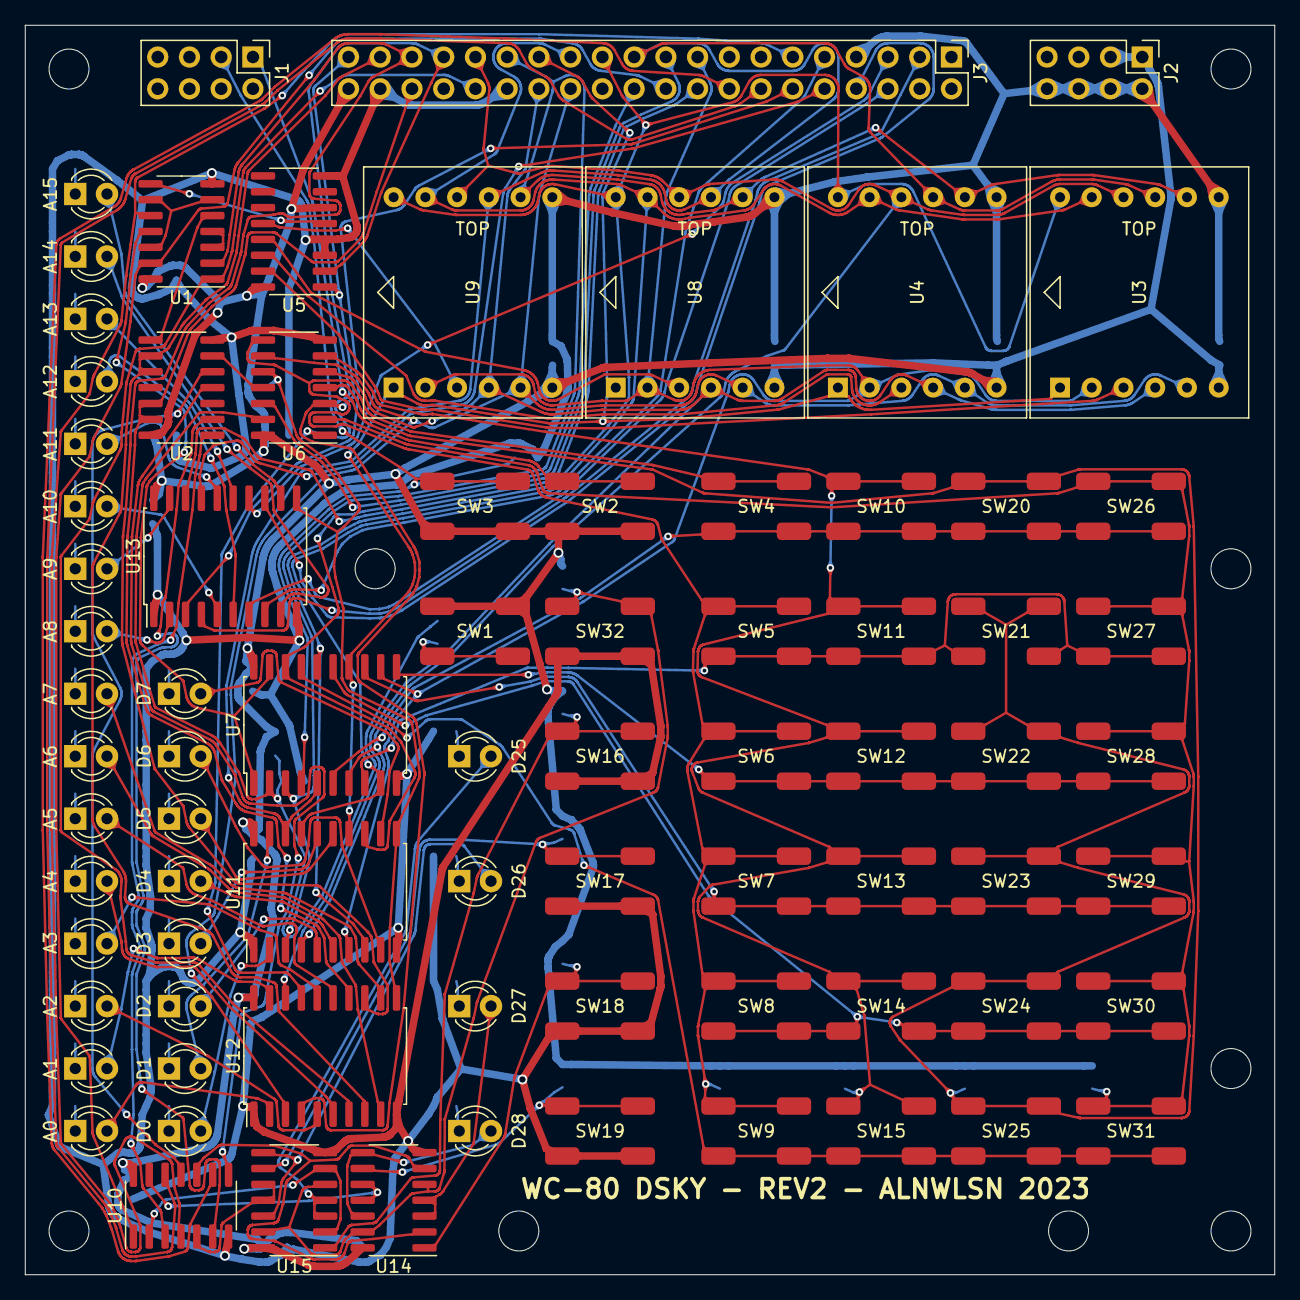
[picture p111: board boards/ledboard2/main.kicad_pcb from above]

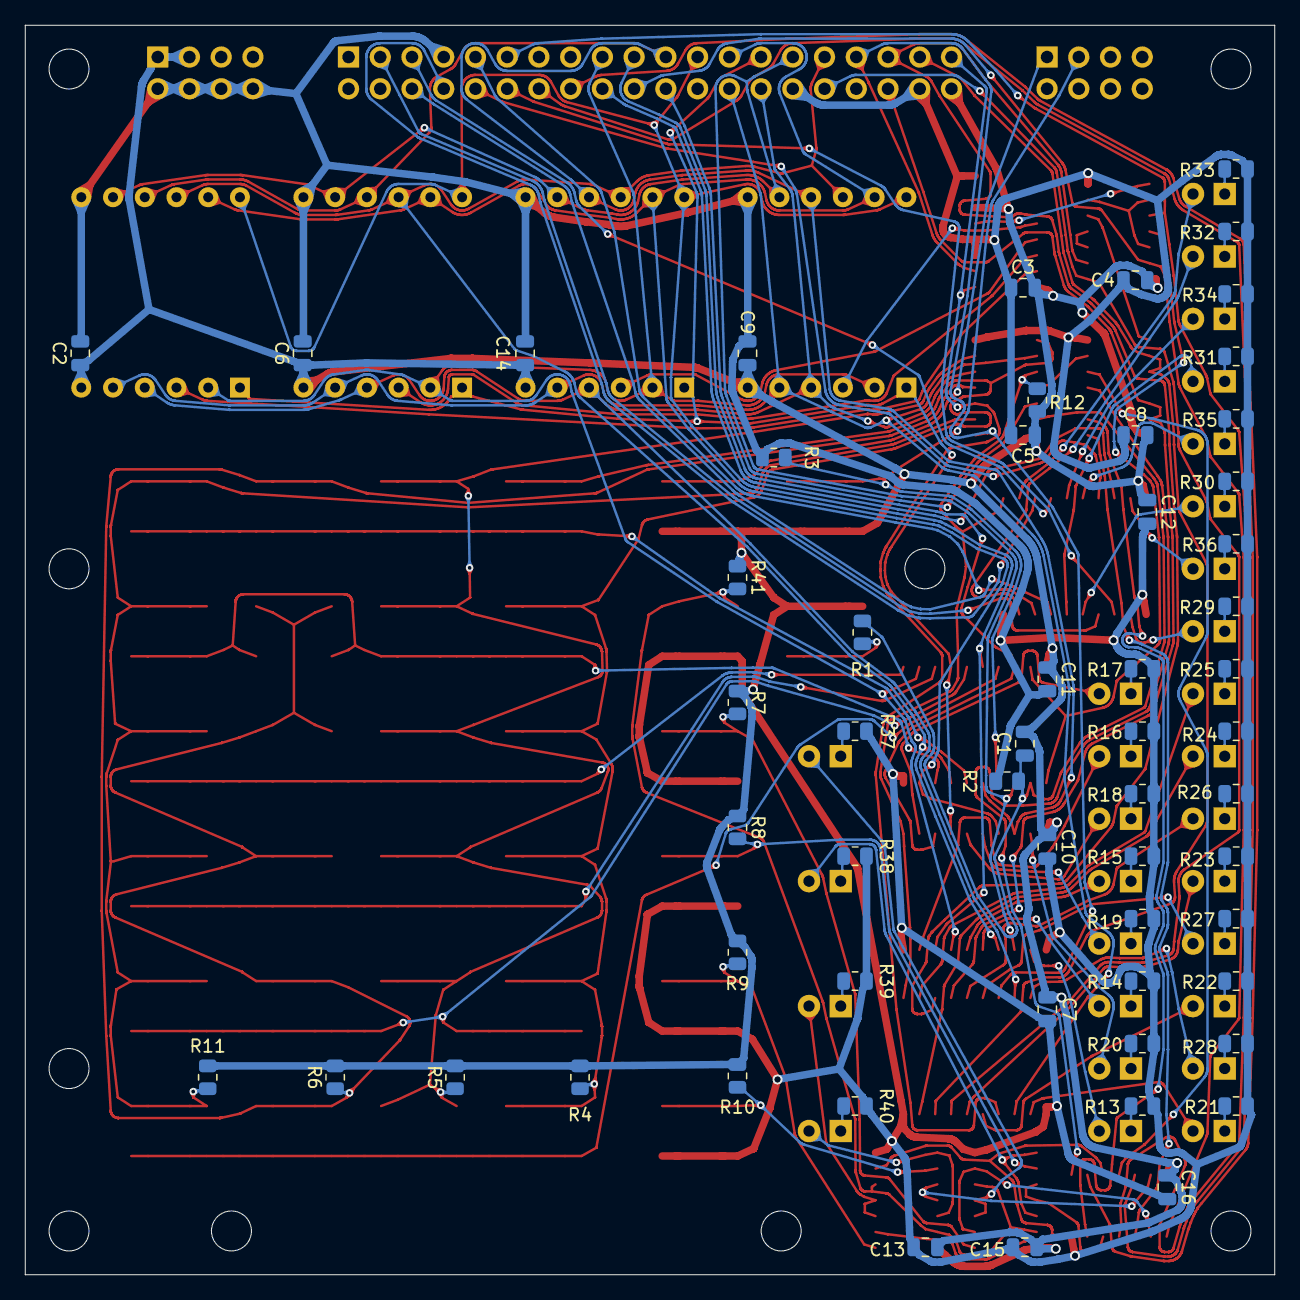
[picture p112: board boards/ledboard2/main.kicad_pcb from below]

Board: 2 copper layers, 100.0 x 100.0 mm, 144 parts (57 on the bottom side), 125 nets.
