alnwlsn/wc-80-archive/boards/0old/floppy-rev2/main.kicad_pcb

## KiCad design boards/0old/floppy-rev2/main.kicad_pcb (2025-07-11, an earlier design)

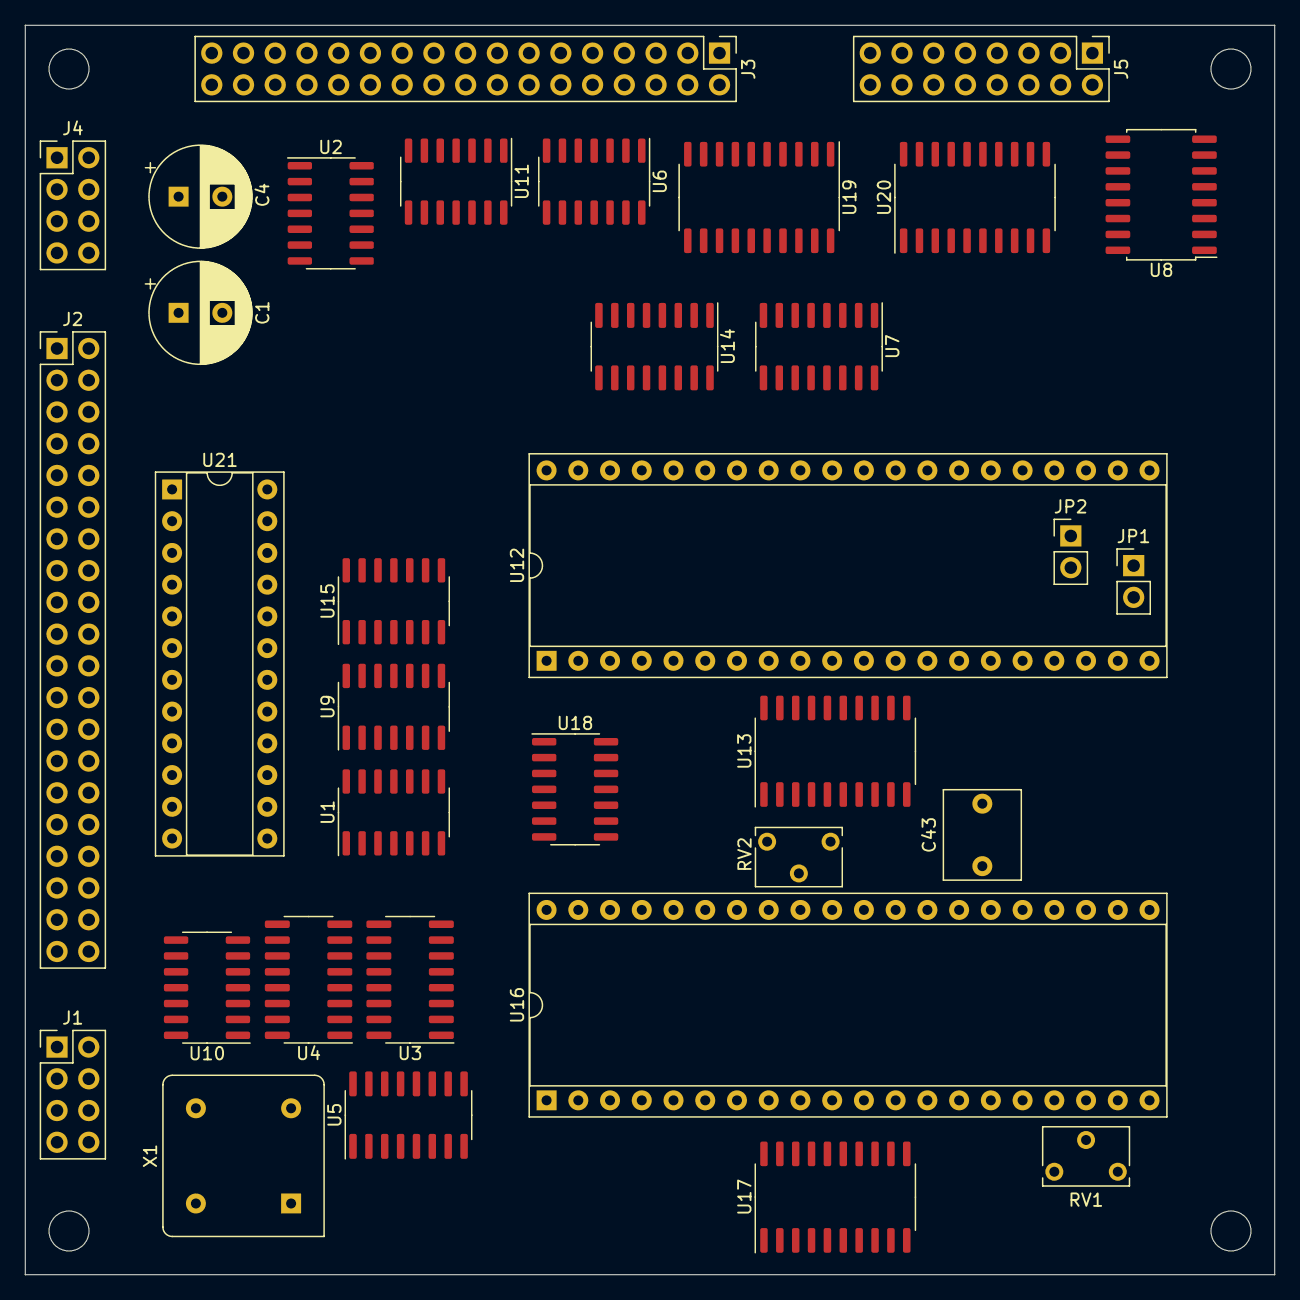
[picture p113: board boards/0old/floppy-rev2/main.kicad_pcb from above]

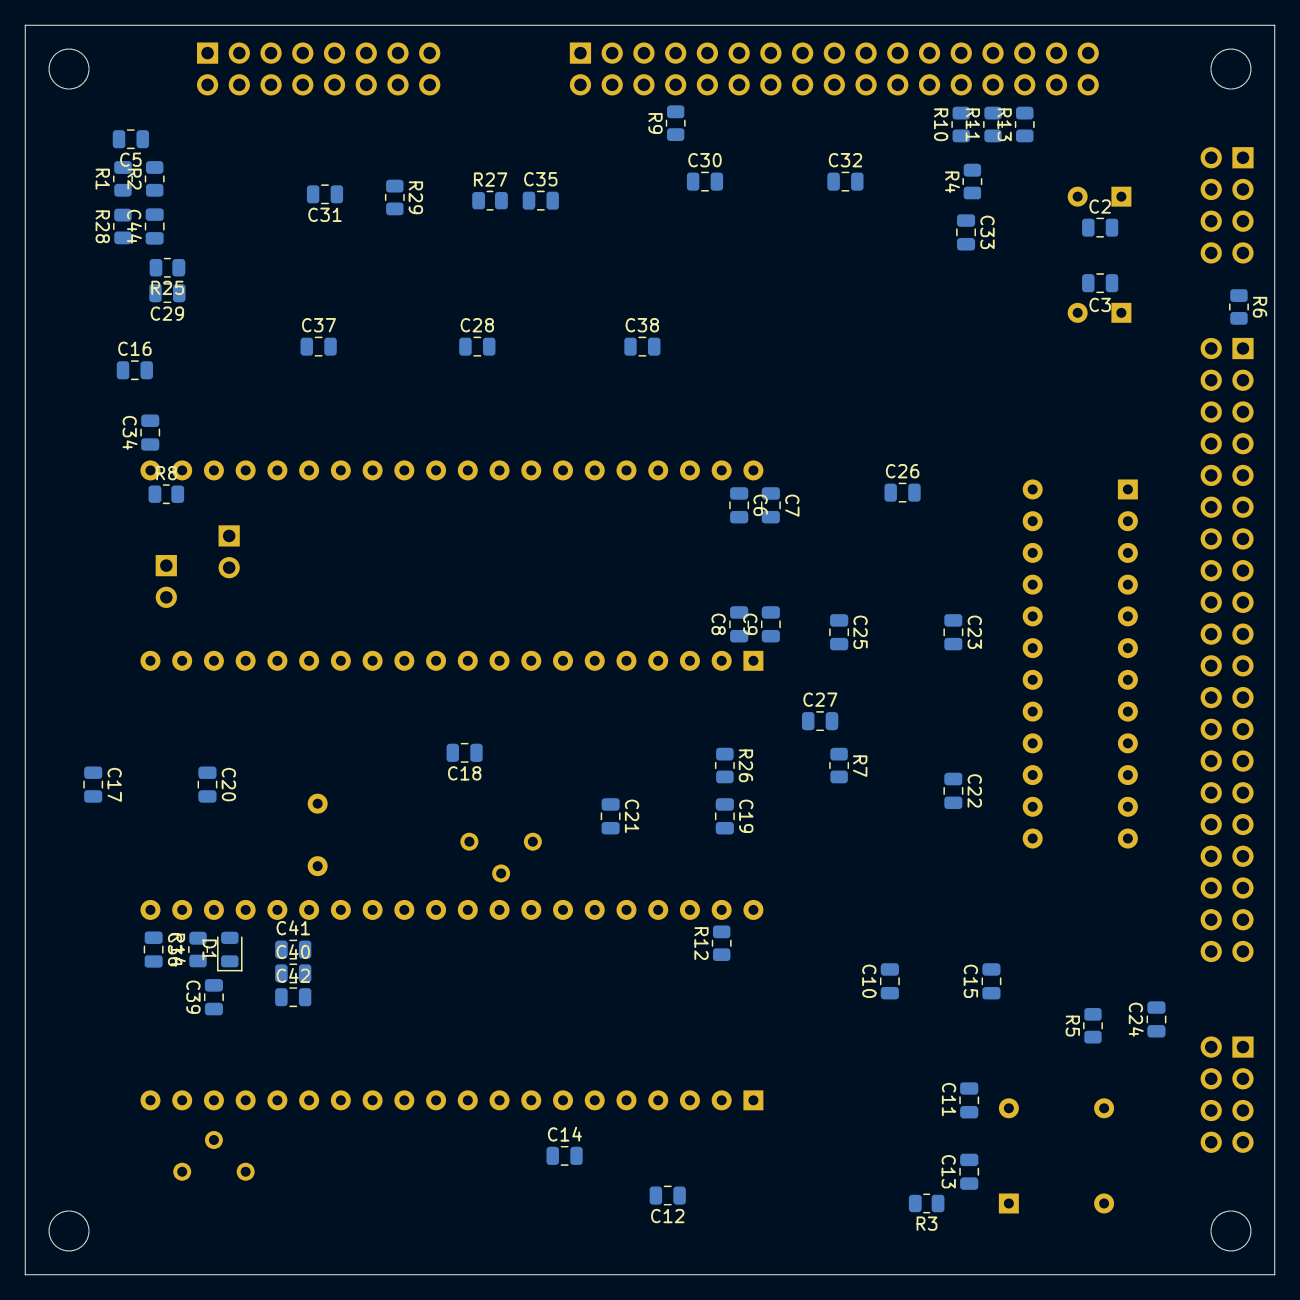
[picture p114: board boards/0old/floppy-rev2/main.kicad_pcb from below]

Board: 2 copper layers, 100.0 x 100.0 mm, 99 parts (61 on the bottom side), 134 nets, no tracks yet.

Parts:
C1, C4: 470uF; CP_Radial_D8.0mm_P3.50mm
C2, C3, C6, C7, C8, C9, C10, C11, C12, C13, C14, C15, C16, C17, C18, C19, C20, C21, C22, C23, C24, C25, C26, C27, C28, C29, C30, C31, C32, C33, C34, C35, C36, C37, C38: 100n; C_0805_2012Metric
C5: 33uF; C_0805_2012Metric
C39: 150nF; C_0805_2012Metric
C40, C41, C42: 15pF; C_0805_2012Metric
C43: 60pF; C_Rect_L7.0mm_W6.0mm_P5.00mm
C44: 200p; C_0805_2012Metric
D1: DIODE; D_0805_2012Metric
J1, J4: Conn_02x04_Odd_Even; PinHeader_2x04_P2.54mm_Vertical
J2: TRS80W-header; PinHeader_2x20_P2.54mm_Vertical
J3: Floppy-header; PinHeader_2x17_P2.54mm_Vertical
J5: Conn_01x16_Male; PinHeader_2x08_P2.54mm_Vertical
JP1: SIDE; PinHeader_1x02_P2.54mm_Vertical
JP2: TEST; PinHeader_1x02_P2.54mm_Vertical
M1, M2, M3, M4: 3mm-mounting-hole; MountingHole_3.2mm_M3_DIN965
R1: 200K; R_0805_2012Metric
R2, R28, R29: 4K7; R_0805_2012Metric
R3, R4, R5, R6, R7, R8, R12, R26, R27: 10K; R_0805_2012Metric
R9, R10, R11, R13: 150; R_0805_2012Metric
R14: 1K; R_0805_2012Metric
R25: 20K; R_0805_2012Metric
RV1: 50K; Potentiometer_Bourns_3266W_Vertical
RV2: 10K; Potentiometer_Bourns_3266W_Vertical
U1, U2: 74LS32; SOIC-14_3.9x8.7mm_P1.27mm
U3, U4, U5: 4518; SOP-16_3.9x9.9mm_P1.27mm
U6, U11: 74LS06; SOIC-14_3.9x8.7mm_P1.27mm
U7: 74LS175; SOP-16_3.9x9.9mm_P1.27mm
U8: 74LS123; SO-16_5.3x10.2mm_P1.27mm
U9, U10, U18: 74LS74; SOIC-14_3.9x8.7mm_P1.27mm
U12: WD1771; DIP-40_W15.24mm_Socket
U13: 74LS640; SO-20_5.3x12.6mm_P1.27mm
U14: 74LS157; SOP-16_3.9x9.9mm_P1.27mm
U15: 74LS02; SOIC-14_3.9x8.7mm_P1.27mm
U16: WD2793; DIP-40_W15.24mm_Socket
U17: 74LS245; SO-20_5.3x12.6mm_P1.27mm
U19: 74LS244; SO-20_5.3x12.6mm_P1.27mm
U20: 74LS273; SO-20_5.3x12.6mm_P1.27mm
U21: ATF22V10C; DIP-24_W7.62mm_Socket
X1: CXO_DIP8; Oscillator_DIP-8

Connections:
1MHz: U9.9, U12.24
2MHz: U5.3, U9.11, U16.24
4MHz: U5.2, X1.5
40Hz: U4.6, U4.10, U10.3
+5V: C1.1, C2.1, C3.1, C4.1, C10.1, C11.1, C12.1, C13.1, C14.1, C15.1, C16.1, C17.1, C18.1, C19.1, C20.1, C21.1, C22.1, C23.1, C24.1, C25.1, C26.1, C27.1, C28.1, C29.1, C30.1, C31.1, C32.1, C33.1, C34.1, C35.1, C36.1, C37.1, C38.1, J2.40, J4.1, J4.3, R1.1, R2.1, R3.1, R4.1, R5.1, R6.1, R7.1, R8.1, R9.1, R10.1, R11.1, R12.1, R13.1, R25.1, R26.1, R27.1, R28.1, R29.1, RV1.1, RV2.3, U1.14, U2.14, U3.16, U4.16, U5.16, U6.14, U7.16, U8.16, U9.14, U10.14, U11.14, U12.21, U13.20, U14.16, U15.14, U16.21, U17.20, U19.20, U20.20, U21.24, X1.8
+12V: C6.1, C7.1, J4.7, U12.40
-5V: C8.1, C9.1, J4.5, U12.1
D0: U1.4, U6.9, U7.2
D1: U1.5, U6.3, U7.7
D2: U1.9, U6.5, U7.10
D3: U1.10, U6.1, U7.15
DFL: U7.9, U8.9, U21.16
F_A0: J2.26, U12.5, U16.5, U21.5
F_A1: J2.28, U12.6, U16.6, U21.6
F_A2: J2.39, U21.7
F_A3: J2.33, U21.8
F_A4: J2.32, U21.9
F_D0: J2.29, U7.4, U13.2, U17.2, U18.2, U20.18
F_D1: J2.21, U7.5, U13.3, U17.3, U20.17
F_D2: J2.31, U7.12, U13.4, U17.4, U20.14
F_D3: J2.25, U7.13, U13.5, U17.5, U20.13
F_D4: J2.17, U13.6, U17.6, U19.17, U20.8
F_D5: J2.27, U13.7, U17.7, U19.15, U20.7
F_D6: J2.23, U13.8, U17.8, U19.13, U19.14, U20.4
F_D7: J2.19, U13.9, U17.9, U19.11, U19.12, U20.3
GND: C1.2, C2.2, C3.2, C4.2, C5.2, C6.2, C7.2, C8.2, C9.2, C10.2, C11.2, C12.2, C13.2, C14.2, C15.2, C16.2, C17.2, C18.2, C19.2, C20.2, C21.2, C22.2, C23.2, C24.2, C25.2, C26.2, C27.2, C28.2, C29.2, C30.2, C31.2, C32.2, C33.2, C34.2, C35.2, C36.2, C37.2, C38.2, C39.1, C40.1, C41.1, C42.1, C43.2, C44.2, J2.7, J2.30, J2.38, J3.1, J3.3, J3.5, J3.7, J3.9, J3.11, J3.13, J3.15, J3.17, J3.19, J3.21, J3.23, J3.25, J3.27, J3.29, J3.31, J3.33, J4.2, J4.4, J4.6, J4.8, J5.1, J5.15, J5.16, JP2.2, RV1.3, RV2.1, U1.7, U2.7, U3.1, U3.7, U3.8, U3.9, U3.15, U4.1, U4.7, U4.8, U4.9, U4.15, U5.1, U5.7, U5.8, U5.9, U5.15, U6.7, U7.8, U8.1, U8.7, U8.8, U8.14, U9.7, U10.2, U10.7, U10.12, U11.7, U12.20, U13.10, U14.8, U14.15, U15.7, U16.20, U17.10, U19.10, U20.10, U21.12, X1.4
INTCLK: U10.9, U11.13, U19.8
INTFLOP: U1.3, U6.13, U19.6
MOTOR: U6.11, U7.1, U8.5
unnamed: C5.1, R1.2, U8.6
unnamed: C39.2, D1.1, R14.1
unnamed: C40.2, C41.2, C42.2, C43.1, U16.26
unnamed: C44.1, R25.2, U8.15
unnamed: D1.2, R14.2, U16.23
unnamed: J3.6, JP1.1, U6.2
unnamed: J3.8, R9.2, U2.4, U2.5
unnamed: J3.10, U6.8
unnamed: J3.12, U6.4
unnamed: J3.14, U6.6
unnamed: J3.16, U6.10
unnamed: J3.18, U11.2
unnamed: J3.20, U11.4
unnamed: J3.22, U11.8
unnamed: J3.24, U11.6
unnamed: J3.26, R10.2, U2.9, U2.10
unnamed: J3.28, R11.2, U2.12, U2.13
unnamed: J3.30, R13.2, U2.1, U2.2
unnamed: J5.2, U8.4
unnamed: J5.3, U20.19
unnamed: J5.4, U20.16
unnamed: J5.5, U19.3
unnamed: J5.6, U20.15
unnamed: J5.7, U20.12
unnamed: J5.8, U20.9
unnamed: J5.9, U20.6
unnamed: J5.10, U20.5
unnamed: J5.11, U20.2
unnamed: J5.12, U19.9
unnamed: J5.13, U19.7
unnamed: J5.14, U19.5
unnamed: JP2.1, U16.22
unnamed: R2.2, U8.10, U8.11
unnamed: R3.2, U9.10, U9.13
unnamed: R4.2, U1.2, U12.39
unnamed: R5.2, U10.1, U10.13
unnamed: R8.2, U12.18, U12.22, U12.25, U12.26, U12.33, U12.37
unnamed: R12.2, U1.1, U16.39
unnamed: R26.2, U18.1, U18.4
unnamed: R27.2, U19.2, U19.4
unnamed: R28.2, U8.3
unnamed: R29.2, U20.1
unnamed: RV1.2, U16.18
unnamed: RV2.2, U16.33
unnamed: U1.11, U12.23, U12.32, U16.32, U16.40
unnamed: U1.8, U1.12
unnamed: U1.6, U1.13
unnamed: U3.2, U5.14
unnamed: U3.6, U3.10
unnamed: U3.14, U4.2
unnamed: U5.6, U5.10
unnamed: U9.8, U9.12
unnamed: U10.5, U10.10
unnamed: U11.1, U14.9
unnamed: U11.3, U14.12
unnamed: U11.5, U14.7
unnamed: U11.9, U14.4
unnamed: U11.11, U21.23
unnamed: U12.2, U13.1, U16.2, U17.1
unnamed: U12.4, U16.4
unnamed: U12.7, U13.18
unnamed: U12.8, U13.17
unnamed: U12.9, U13.16
unnamed: U12.10, U13.15
unnamed: U12.11, U13.14
unnamed: U12.12, U13.13
unnamed: U12.13, U13.12
unnamed: U12.14, U13.11
unnamed: U12.15, U14.13
unnamed: U12.16, U14.10
unnamed: U12.27, U15.4
unnamed: U12.30, U14.6
unnamed: U12.31, U14.3
unnamed: U2.8, U12.34, U16.34
unnamed: U2.6, U12.35, U16.35
unnamed: U2.11, U12.36, U16.36
unnamed: U14.2, U16.31
unnamed: U14.5, U16.30
unnamed: U14.11, U16.16
unnamed: U14.14, U16.15
unnamed: U2.3, U15.5, U15.6, U16.27
unnamed: U15.9, U18.5
unnamed: U16.1, U16.29
unnamed: U16.7, U17.18
unnamed: U16.8, U17.17
unnamed: U16.9, U17.16
unnamed: U16.10, U17.15
unnamed: U16.11, U17.14
unnamed: U16.12, U17.13
unnamed: U16.13, U17.12
unnamed: U16.14, U17.11
unnamed: U16.17, U16.25
~37E0~: U10.4, U10.11, U19.1, U21.14
~1771~: U12.3, U13.19, U15.13
~2793~: R7.2, U14.1, U15.10, U15.11, U15.12, U16.3, U17.19
~F_EXMEM~: J2.4, U21.13
~F_INT~: J2.22, U6.12, U11.12
~F_INUSE~: J2.15, U11.10
~F_IN~: J2.20, U21.2
~F_OUT~: J2.11, U21.1
~F_READ~: J2.16, U21.4
~F_SYSRES~: J2.1, R6.2, U12.19, U16.19
~F_WRITE~: J2.14, U21.3
~PRINTREAD~: U19.19, U21.20
~PRINTWRITE~: U8.2, U20.11, U21.17
