alnwlsn/wc-80-archive/boards/keyboard-matrix/0old/keyboard-matrix-positions-backup/keyboard-matrix.kicad_pcb

## KiCad design boards/keyboard-matrix/0old/keyboard-matrix-positions-backup/keyboard-matrix.kicad_pcb (2025-07-11, an earlier design)

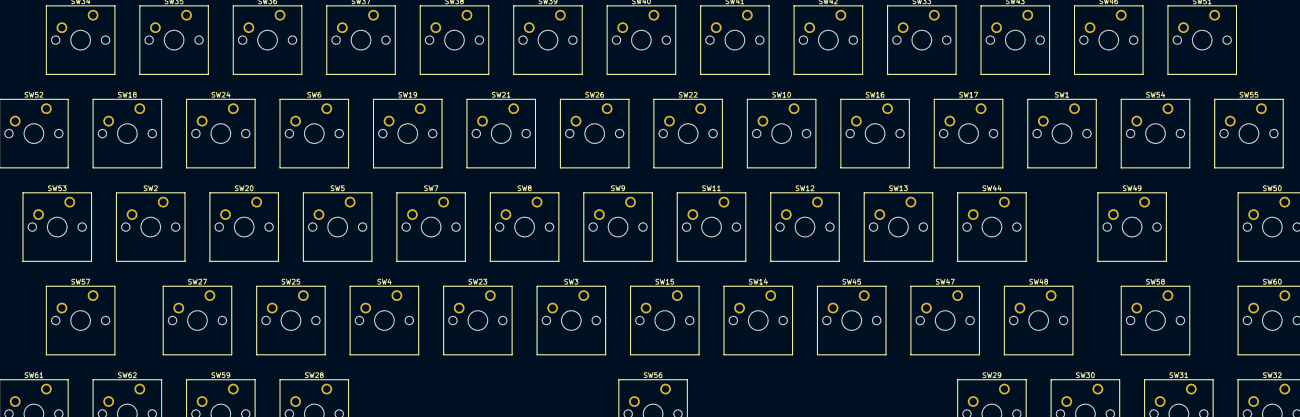
[picture p115: board boards/keyboard-matrix/0old/keyboard-matrix-positions-backup/keyboard… from above]

Board: 2 copper layers, 62 parts (0 on the bottom side), 16 nets, no tracks yet.

Parts:
SW1: @; SW_Cherry_MX_1.00u_PCB
SW2: A; SW_Cherry_MX_1.00u_PCB
SW3: B; SW_Cherry_MX_1.00u_PCB
SW4: C; SW_Cherry_MX_1.00u_PCB
SW5: D; SW_Cherry_MX_1.00u_PCB
SW6: E; SW_Cherry_MX_1.00u_PCB
SW7: F; SW_Cherry_MX_1.00u_PCB
SW8: G; SW_Cherry_MX_1.00u_PCB
SW9: H; SW_Cherry_MX_1.00u_PCB
SW10: I; SW_Cherry_MX_1.00u_PCB
SW11: J; SW_Cherry_MX_1.00u_PCB
SW12: K; SW_Cherry_MX_1.00u_PCB
SW13: L; SW_Cherry_MX_1.00u_PCB
SW14: M; SW_Cherry_MX_1.00u_PCB
SW15: N; SW_Cherry_MX_1.00u_PCB
SW16: O; SW_Cherry_MX_1.00u_PCB
SW17: P; SW_Cherry_MX_1.00u_PCB
SW18: Q; SW_Cherry_MX_1.00u_PCB
SW19: R; SW_Cherry_MX_1.00u_PCB
SW20: S; SW_Cherry_MX_1.00u_PCB
SW21: T; SW_Cherry_MX_1.00u_PCB
SW22: U; SW_Cherry_MX_1.00u_PCB
SW23: V; SW_Cherry_MX_1.00u_PCB
SW24: W; SW_Cherry_MX_1.00u_PCB
SW25: X; SW_Cherry_MX_1.00u_PCB
SW26: Y; SW_Cherry_MX_1.00u_PCB
SW27: Z; SW_Cherry_MX_1.00u_PCB
SW28: Z1; SW_Cherry_MX_1.00u_PCB
SW29: Z2; SW_Cherry_MX_1.00u_PCB
SW30: Z3; SW_Cherry_MX_1.00u_PCB
SW31: Z4; SW_Cherry_MX_1.00u_PCB
SW32: Z5; SW_Cherry_MX_1.00u_PCB
SW33: 0; SW_Cherry_MX_1.00u_PCB
SW34: 1; SW_Cherry_MX_1.00u_PCB
SW35: 2; SW_Cherry_MX_1.00u_PCB
SW36: 3; SW_Cherry_MX_1.00u_PCB
SW37: 4; SW_Cherry_MX_1.00u_PCB
SW38: 5; SW_Cherry_MX_1.00u_PCB
SW39: 6; SW_Cherry_MX_1.00u_PCB
SW40: 7; SW_Cherry_MX_1.00u_PCB
SW41: 8; SW_Cherry_MX_1.00u_PCB
SW42: 9; SW_Cherry_MX_1.00u_PCB
SW43: *; SW_Cherry_MX_1.00u_PCB
SW44: +; SW_Cherry_MX_1.00u_PCB
SW45: <; SW_Cherry_MX_1.00u_PCB
SW46: =; SW_Cherry_MX_1.00u_PCB
SW47: >; SW_Cherry_MX_1.00u_PCB
SW48: ?; SW_Cherry_MX_1.00u_PCB
SW49: Enter; SW_Cherry_MX_1.00u_PCB
SW50: Clear; SW_Cherry_MX_1.00u_PCB
SW51: Break; SW_Cherry_MX_1.00u_PCB
SW52: Up; SW_Cherry_MX_1.00u_PCB
SW53: Down; SW_Cherry_MX_1.00u_PCB
SW54: Left; SW_Cherry_MX_1.00u_PCB
SW55: Right; SW_Cherry_MX_1.00u_PCB
SW56: Space; SW_Cherry_MX_1.00u_PCB
SW57: Shift; SW_Cherry_MX_1.00u_PCB
SW58: R Shift; SW_Cherry_MX_1.00u_PCB
SW59: Z0; SW_Cherry_MX_1.00u_PCB
SW60: Control; SW_Cherry_MX_1.00u_PCB
SW61: NMI; SW_Cherry_MX_1.00u_PCB
SW62: RESET; SW_Cherry_MX_1.00u_PCB

Connections:
unnamed: SW1.1, SW2.1, SW3.1, SW4.1, SW5.1, SW6.1, SW7.1, SW8.1
unnamed: SW1.2, SW9.2, SW17.2, SW25.2, SW33.2, SW41.2, SW49.2, SW57.2
unnamed: SW9.1, SW10.1, SW11.1, SW12.1, SW13.1, SW14.1, SW15.1, SW16.1
unnamed: SW2.2, SW10.2, SW18.2, SW26.2, SW34.2, SW42.2, SW50.2, SW58.2
unnamed: SW3.2, SW11.2, SW19.2, SW27.2, SW35.2, SW43.2, SW51.2, SW59.2
unnamed: SW4.2, SW12.2, SW20.2, SW28.2, SW36.2, SW44.2, SW52.2
unnamed: SW5.2, SW13.2, SW21.2, SW29.2, SW37.2, SW45.2, SW53.2, SW60.2
unnamed: SW6.2, SW14.2, SW22.2, SW30.2, SW38.2, SW46.2, SW54.2
unnamed: SW7.2, SW15.2, SW23.2, SW31.2, SW39.2, SW47.2, SW55.2
unnamed: SW8.2, SW16.2, SW24.2, SW32.2, SW40.2, SW48.2, SW56.2
unnamed: SW17.1, SW18.1, SW19.1, SW20.1, SW21.1, SW22.1, SW23.1, SW24.1
unnamed: SW25.1, SW26.1, SW27.1, SW28.1, SW29.1, SW30.1, SW31.1, SW32.1
unnamed: SW33.1, SW34.1, SW35.1, SW36.1, SW37.1, SW38.1, SW39.1, SW40.1
unnamed: SW41.1, SW42.1, SW43.1, SW44.1, SW45.1, SW46.1, SW47.1, SW48.1
unnamed: SW49.1, SW50.1, SW51.1, SW52.1, SW53.1, SW54.1, SW55.1, SW56.1
unnamed: SW57.1, SW58.1, SW59.1, SW60.1
