alnwlsn/wc-80-archive/boards/frehd/main.kicad_pcb

## KiCad design boards/frehd/main.kicad_pcb (2025-07-11)

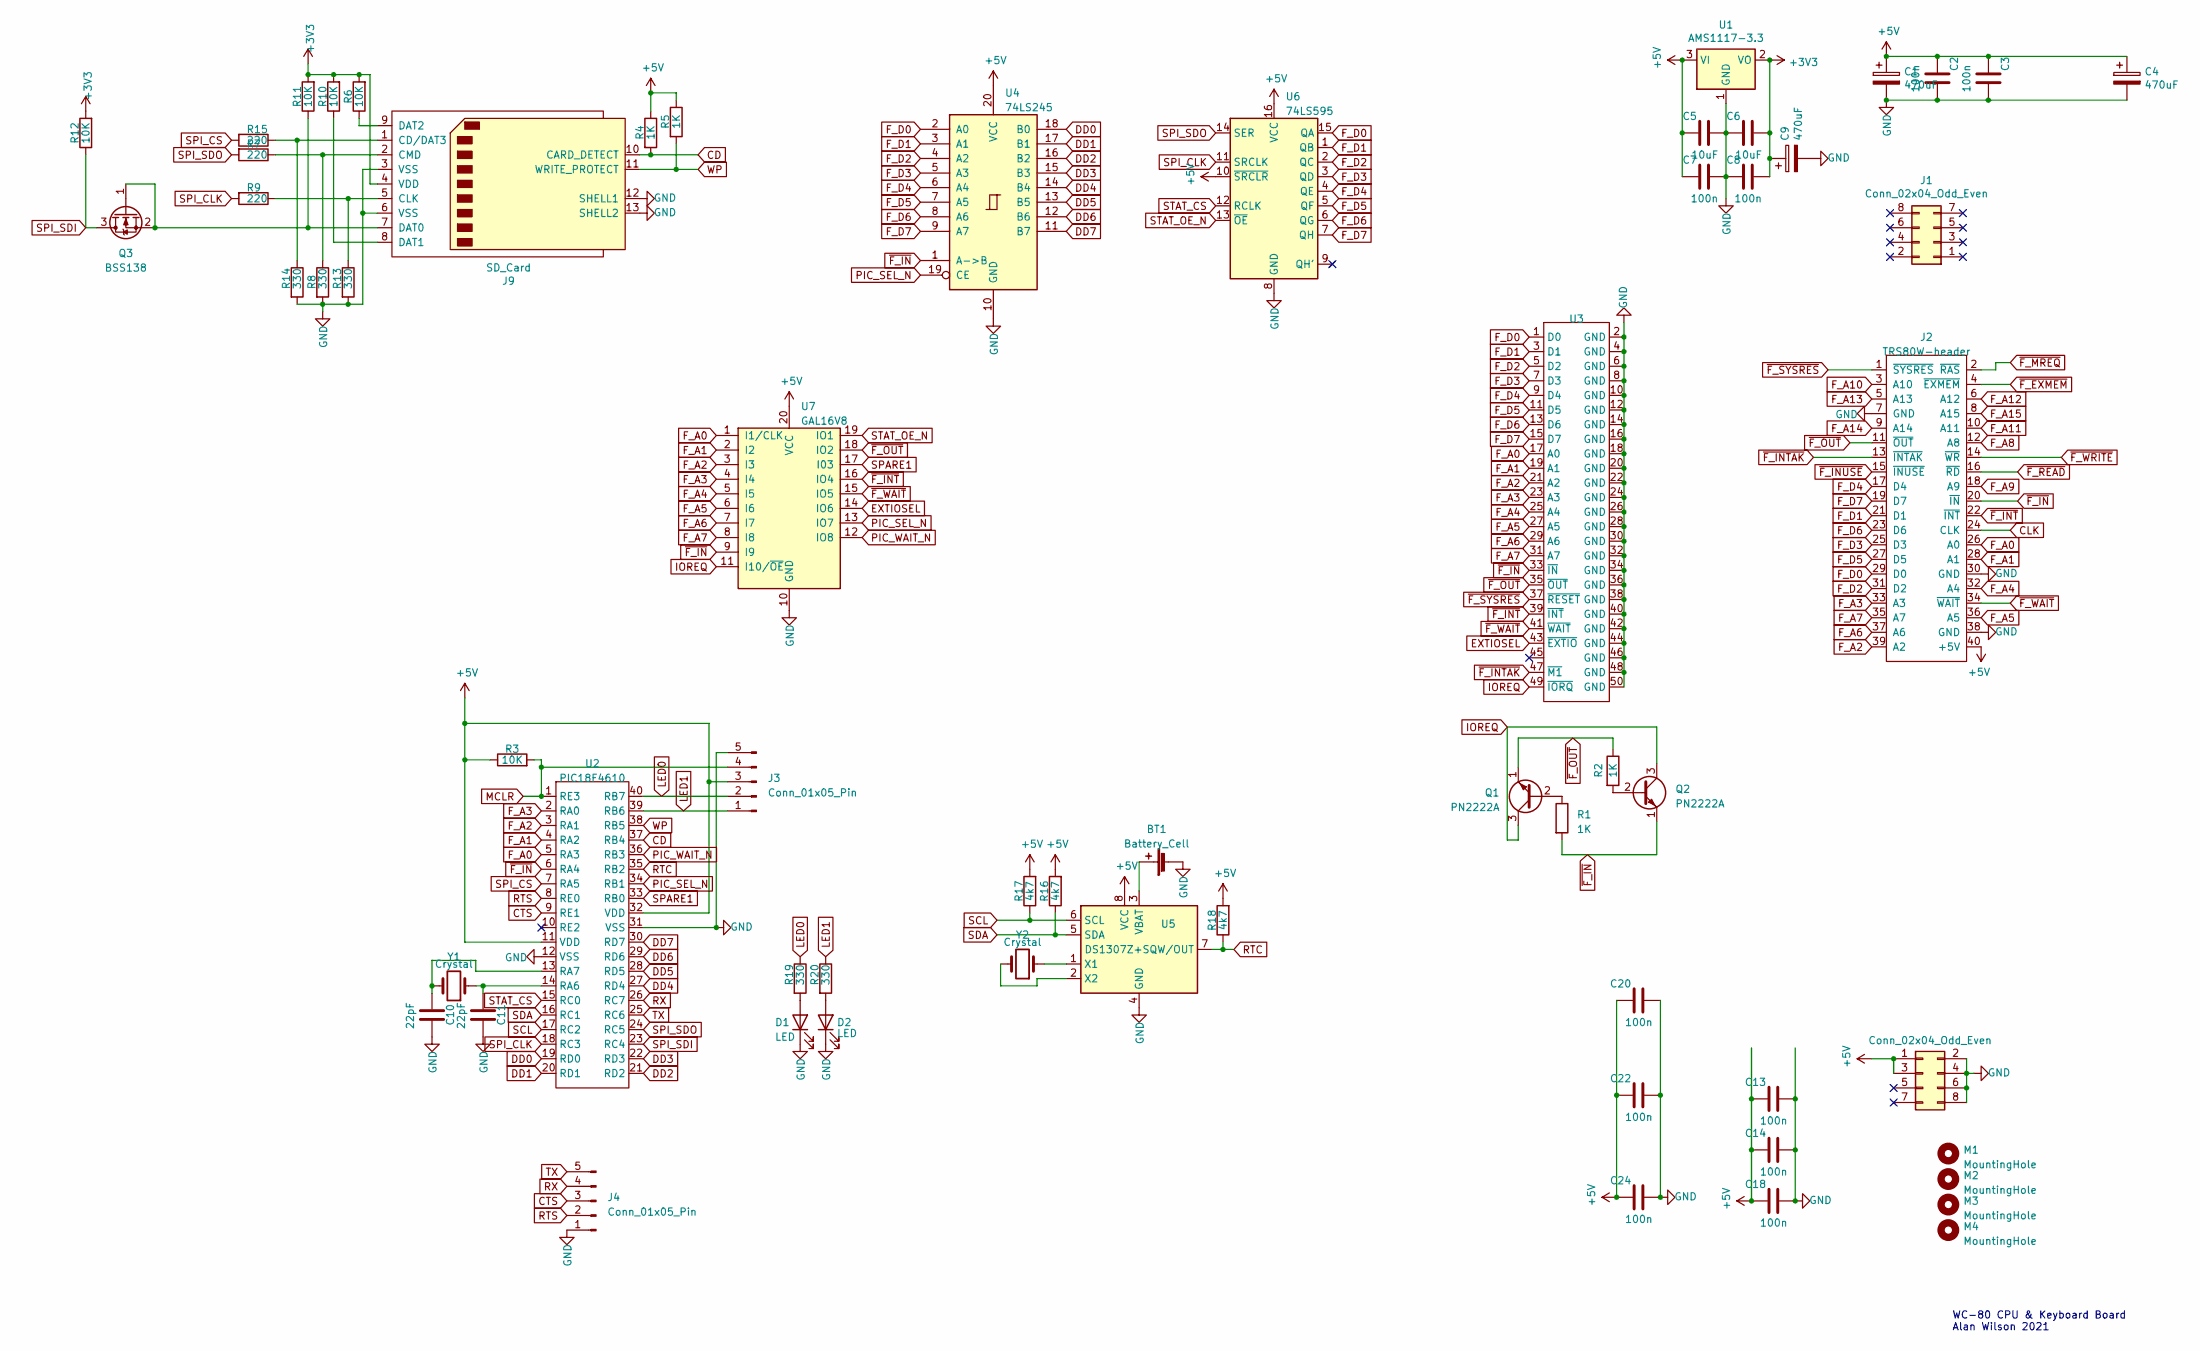
[picture p116: schematic main.kicad_sch]

Parts:
BT1: Battery_Cell; BS-01-A4CJ004
C1, C4, C9: 470uF; CP_Radial_D8.0mm_P3.50mm
C2, C3, C7, C8, C13, C14, C18, C20, C22, C24: 100n; C_0805_2012Metric
C5, C6: 10uF; C_0805_2012Metric
C10, C11: 22pF; C_0805_2012Metric
D1, D2: LED; LED_D3.0mm
J1, J5: Conn_02x04_Odd_Even; PinHeader_2x04_P2.54mm_Vertical
J2: TRS80W-header; PinHeader_2x20_P2.54mm_Vertical
J3, J4: Conn_01x05_Pin; PinSocket_1x05_P2.54mm_Vertical
J9: SD_Card; SD_Card_ XUNPU_SD-101
M1, M2, M3, M4: MountingHole; MountingHole_3.2mm_M3_DIN965
Q1, Q2: PN2222A; TO-92_Inline
Q3: BSS138; SOT-23
R1, R2, R4, R5: 1K; R_0805_2012Metric
R3, R6, R10, R11, R12: 10K; R_0805_2012Metric
R7, R9, R15: 220; R_0805_2012Metric
R8, R13, R14, R19, R20: 330; R_0805_2012Metric
R16, R17, R18: 4k7; R_0805_2012Metric
U1: AMS1117-3.3; SOT-223-3_TabPin2
U2: PIC18F4610; DIP-40_W15.24mm_Socket
U3: PinSocket_2x25_P2.54mm_Vertical
U4: 74LS245; SO-20_5.3x12.6mm_P1.27mm
U5: DS1307Z+; SOIC-8_3.9x4.9mm_P1.27mm
U6: 74LS595; SO-16_3.9x9.9mm_P1.27mm
U7: GAL16V8; DIP-20_W7.62mm
Y1: Crystal; Crystal_SMD_HC49-SD
Y2: Crystal; Crystal_AT310_D3.0mm_L10.0mm_Horizontal

Connections:
+3V3: C6.2, C8.2, C9.1, J9.4 (VDD), R6.2, R10.2, R11.2, R12.2, U1.2 (VO)
+5V: C1.1, C2.1, C3.1, C4.1, C5.1, C7.1, C13.1, C14.1, C18.1, C20.1, C22.1, C24.1, J2.40 (+5V), J3.3, J5.1, J5.3, R3.1, R4.1, R5.1, R16.2, R17.2, R18.2, U1.3 (VI), U2.11 (VDD), U2.32 (VDD), U4.20 (VCC), U5.8 (VCC), U6.10 (~SRCLR), U6.16 (VCC), U7.20 (VCC)
CD: J9.10 (CARD_DETECT), R4.2, U2.37 (RB4)
CLK: J2.24 (CLK)
CTS: J4.3, U2.9 (RE1)
DD0: U2.19 (RD0), U4.18 (B0)
DD1: U2.20 (RD1), U4.17 (B1)
DD2: U2.21 (RD2), U4.16 (B2)
DD3: U2.22 (RD3), U4.15 (B3)
DD4: U2.27 (RD4), U4.14 (B4)
DD5: U2.28 (RD5), U4.13 (B5)
DD6: U2.29 (RD6), U4.12 (B6)
DD7: U2.30 (RD7), U4.11 (B7)
EXTIOSEL: U3.43 (~EXTIO), U7.14 (IO6)
F_A0: J2.26 (A0), U2.5 (RA3), U3.17 (A0), U7.1 (I1/CLK)
F_A1: J2.28 (A1), U2.4 (RA2), U3.19 (A1), U7.2 (I2)
F_A2: J2.39 (A2), U2.3 (RA1), U3.21 (A2), U7.3 (I3)
F_A3: J2.33 (A3), U2.2 (RA0), U3.23 (A3), U7.4 (I4)
F_A4: J2.32 (A4), U3.25 (A4), U7.5 (I5)
F_A5: J2.36 (A5), U3.27 (A5), U7.6 (I6)
F_A6: J2.37 (A6), U3.29 (A6), U7.7 (I7)
F_A7: J2.35 (A7), U3.31 (A7), U7.8 (I8)
F_A8: J2.12 (A8)
F_A9: J2.18 (A9)
F_A10: J2.3 (A10)
F_A11: J2.10 (A11)
F_A12: J2.6 (A12)
F_A13: J2.5 (A13)
F_A14: J2.9 (A14)
F_A15: J2.8 (A15)
F_D0: J2.29 (D0), U3.1 (D0), U4.2 (A0), U6.15 (QA)
F_D1: J2.21 (D1), U3.3 (D1), U4.3 (A1), U6.1 (QB)
F_D2: J2.31 (D2), U3.5 (D2), U4.4 (A2), U6.2 (QC)
F_D3: J2.25 (D3), U3.7 (D3), U4.5 (A3), U6.3 (QD)
F_D4: J2.17 (D4), U3.9 (D4), U4.6 (A4), U6.4 (QE)
F_D5: J2.27 (D5), U3.11 (D5), U4.7 (A5), U6.5 (QF)
F_D6: J2.23 (D6), U3.13 (D6), U4.8 (A6), U6.6 (QG)
F_D7: J2.19 (D7), U3.15 (D7), U4.9 (A7), U6.7 (QH)
GND: BT1.2 (-), C1.2, C2.2, C3.2, C4.2, C5.2, C6.1, C7.2, C8.1, C9.2, C10.2, C11.2, C13.2, C14.2, C18.2, C20.2, C22.2, C24.2, D1.1 (K), D2.1 (K), J2.7 (GND), J2.30 (GND), J2.38 (GND), J3.5, J4.1, J5.2, J5.4, J5.6, J5.8, J9.3 (VSS), J9.6 (VSS), J9.12 (SHELL1), J9.13 (SHELL2), R8.2, R13.2, R14.2, U1.1 (GND), U2.12 (VSS), U2.31 (VSS), U3.2 (GND), U3.4 (GND), U3.6 (GND), U3.8 (GND), U3.10 (GND), U3.12 (GND), U3.14 (GND), U3.16 (GND), U3.18 (GND), U3.20 (GND), U3.22 (GND), U3.24 (GND), U3.26 (GND), U3.28 (GND), U3.30 (GND), U3.32 (GND), U3.34 (GND), U3.36 (GND), U3.38 (GND), U3.40 (GND), U3.42 (GND), U3.44 (GND), U3.46 (GND), U3.48 (GND), U3.50 (GND), U4.10 (GND), U5.4 (GND), U6.8 (GND), U7.10 (GND)
IOREQ: Q1.3 (C), Q2.3 (C), U3.49 (~IORQ), U7.11 (I10/~OE)
LED0: J3.2, R19.1, U2.40 (RB7)
LED1: J3.1, R20.1, U2.39 (RB6)
MCLR: J3.4, R3.2, U2.1 (RE3)
unnamed: BT1.1 (+), U5.3 (VBAT)
unnamed: D1.2 (A), R19.2
unnamed: D2.2 (A), R20.2
unnamed: J9.1 (CD/DAT3), R14.1, R15.1
unnamed: J9.5 (CLK), R9.1, R13.1
unnamed: J9.2 (CMD), R7.1, R8.1
unnamed: J9.7 (DAT0), Q3.1 (G), Q3.2 (S), R11.1
unnamed: J9.8 (DAT1), R10.1
unnamed: J9.9 (DAT2), R6.1
unnamed: Q1.2 (B), R1.1
unnamed: Q2.2 (B), R2.2
unnamed: C11.1, U2.14 (RA6), Y1.1
unnamed: C10.1, U2.13 (RA7), Y1.2
unnamed: U5.1 (X1), Y2.1
unnamed: U5.2 (X2), Y2.2
PIC_SEL_N: U2.34 (RB1), U4.19 (CE), U7.13 (IO7)
PIC_WAIT_N: U2.36 (RB3), U7.12 (IO8)
RTC: R18.1, U2.35 (RB2), U5.7 (SQW/OUT)
RTS: J4.2, U2.8 (RE0)
RX: J4.4, U2.26 (RC7)
SCL: R17.1, U2.17 (RC2), U5.6 (SCL)
SDA: R16.1, U2.16 (RC1), U5.5 (SDA)
SPARE1: U2.33 (RB0), U7.17 (I03)
SPI_CLK: R9.2, U2.18 (RC3), U6.11 (SRCLK)
SPI_CS: R15.2, U2.7 (RA5)
SPI_SDI: Q3.3 (D), R12.1, U2.23 (RC4)
SPI_SDO: R7.2, U2.24 (RC5), U6.14 (SER)
STAT_CS: U2.15 (RC0), U6.12 (RCLK)
STAT_OE_N: U6.13 (~OE), U7.19 (IO1)
TX: J4.5, U2.25 (RC6)
WP: J9.11 (WRITE_PROTECT), R5.2, U2.38 (RB5)
~F_EXMEM: J2.4 (~EXMEM)
~F_INTAK: J2.13 (~INTAK), U3.47 (~M1)
~F_INT: J2.22 (~INT), U3.39 (~INT), U7.16 (IO4)
~F_INUSE: J2.15 (~INUSE)
~F_IN: J2.20 (~IN), Q2.1 (E), R1.2, U2.6 (RA4), U3.33 (~IN), U4.1 (A->B), U7.9 (I9)
~F_MREQ: J2.2 (~RAS)
~F_OUT: J2.11 (~OUT), Q1.1 (E), R2.1, U3.35 (~OUT), U7.18 (IO2)
~F_READ: J2.16 (~RD)
~F_SYSRES: J2.1 (~SYSRES), U3.37 (~RESET)
~F_WAIT: J2.34 (~WAIT), U3.41 (~WAIT), U7.15 (IO5)
~F_WRITE: J2.14 (~WR)

Notes on the sheet:
WC-80 CPU & Keyboard Board Alan Wilson 2021

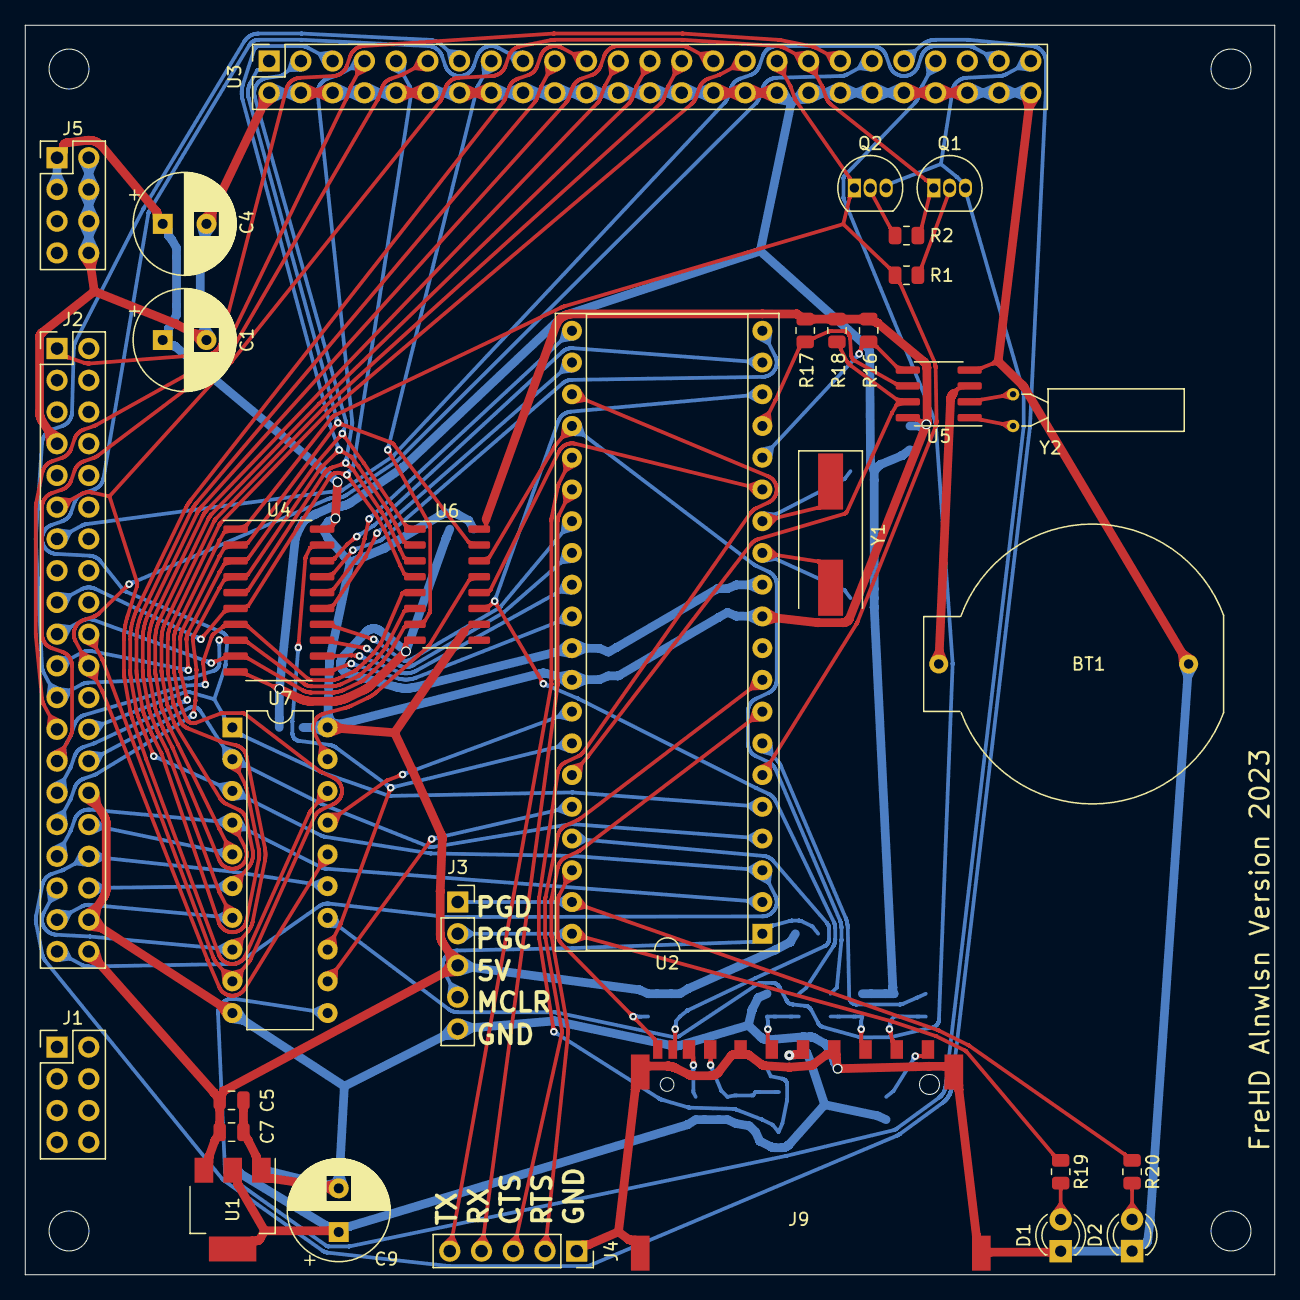
[picture p117: board boards/frehd/main.kicad_pcb from above]

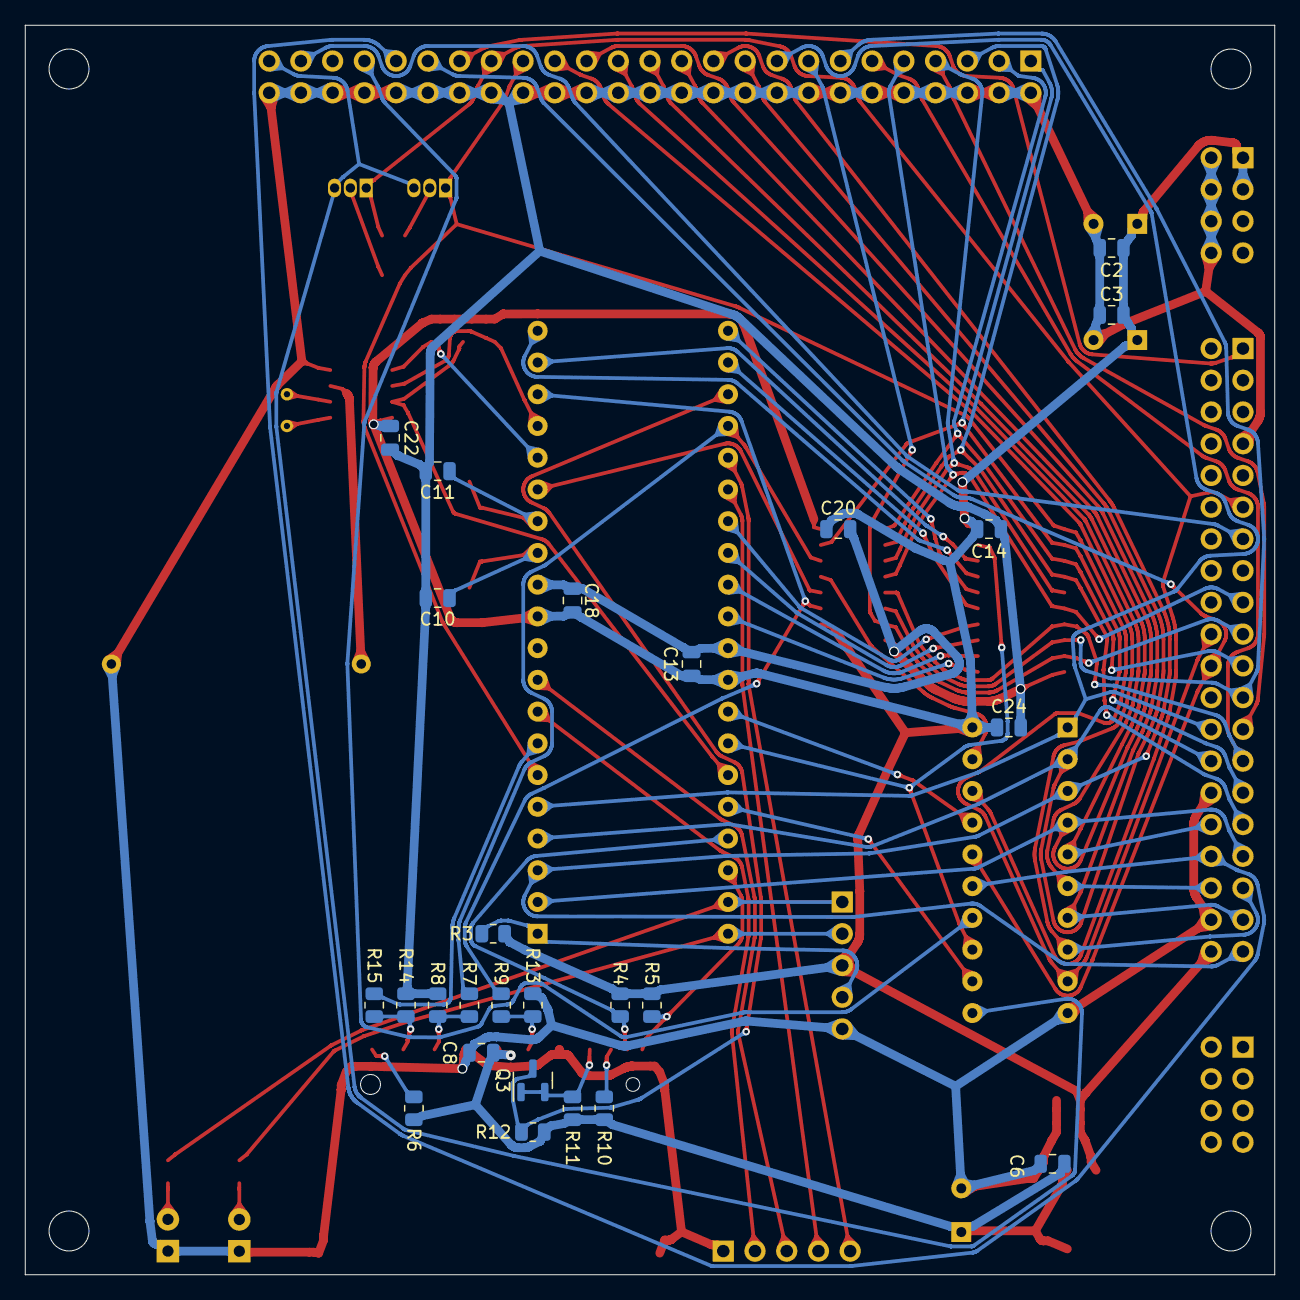
[picture p118: board boards/frehd/main.kicad_pcb from below]

Board: 2 copper layers, 100.0 x 100.0 mm, 62 parts (26 on the bottom side), 71 nets.
