alnwlsn/wc-80-archive/boards/trs80-breakout/main.kicad_pcb

## KiCad design boards/trs80-breakout/main.kicad_pcb (2025-07-11)

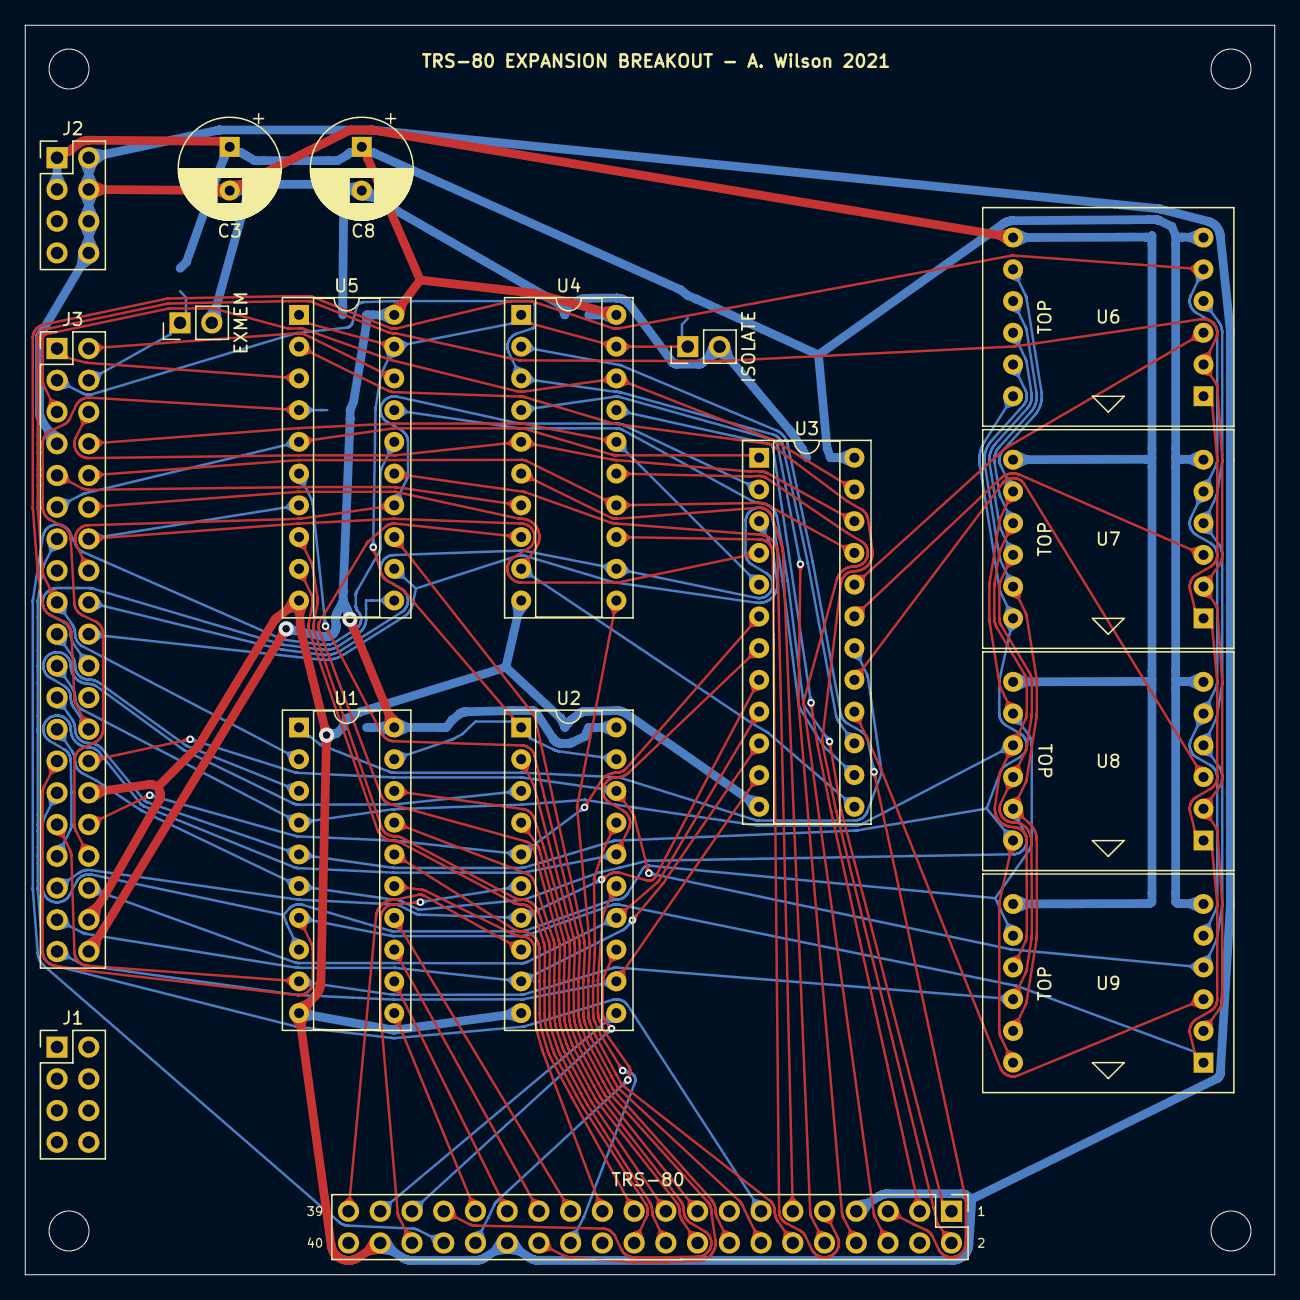
[picture p119: board boards/trs80-breakout/main.kicad_pcb from above]

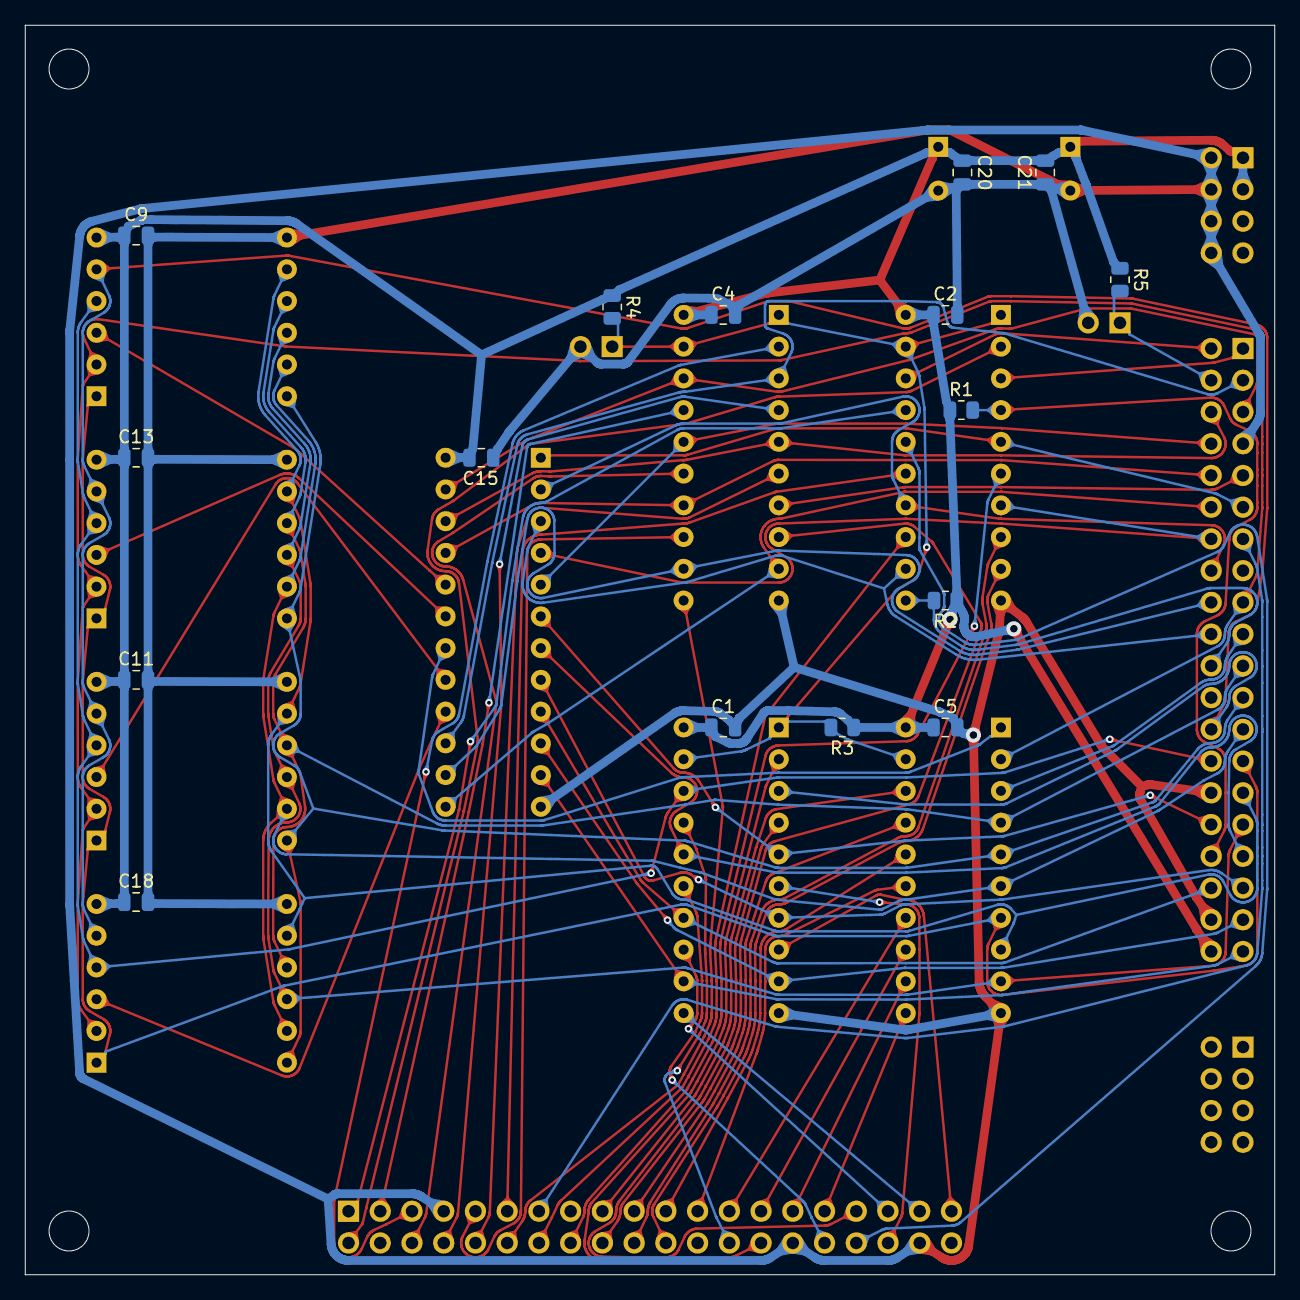
[picture p120: board boards/trs80-breakout/main.kicad_pcb from below]

Board: 2 copper layers, 100.0 x 100.0 mm, 37 parts (16 on the bottom side), 74 nets.

Parts:
C1, C2, C4, C5, C9, C11, C13, C15, C18, C20, C21: 100n; C_0805_2012Metric
C3, C8: 470uF; CP_Radial_D8.0mm_P3.50mm
J1, J2: Conn_02x04_Odd_Even; PinHeader_2x04_P2.54mm_Vertical
J3: TRS80W-header; PinHeader_2x20_P2.54mm_Vertical
J4: TRS-80; PinHeader_2x20_P2.54mm_Vertical
JP1: ISOLATE; PinHeader_1x02_P2.54mm_Vertical
JP2: EXMEM; PinHeader_1x02_P2.54mm_Vertical
M1, M2, M3, M4: 3mm-mounting-hole; MountingHole_3.2mm_M3_DIN965
R1, R2, R3, R4, R5: R; R_0805_2012Metric
U1: 74LS245; DIP-20_W7.62mm_Socket
U2, U4, U5: 74LS244; DIP-20_W7.62mm_Socket
U3: ATF22V10C; DIP-24_W7.62mm_Socket
U6, U7, U8, U9: HPDL1414; DIP-24_W15.24mm_Socket

Connections:
+5V: C1.1, C2.1, C3.1, C4.1, C5.1, C8.1, C9.1, C11.1, C13.1, C15.1, C18.1, C20.1, C21.1, J2.1, J2.3, J3.40, R1.1, R2.1, R3.1, R4.1, R5.1, U1.20, U2.20, U3.24, U4.20, U5.20, U6.6, U7.6, U8.6, U9.6
A0: J4.26, U2.17
A1: J4.28, U2.2
A2: J4.39, U2.8
A3: J4.33, U2.4
A4: J4.32, U2.15
A5: J4.36, U2.6
A6: J4.37, U2.11
A7: J4.35, U2.13
A8: J4.12, U4.11
A9: J4.18, U4.8
A10: J4.3, U4.17
A11: J4.10, U4.6
A12: J4.6, U4.15
A13: J4.5, U4.2
A14: J4.9, U4.13
A15: J4.8, U4.4
D0: J4.29, U1.12
D1: J4.21, U1.16
D2: J4.31, U1.11
D3: J4.25, U1.14
D4: J4.17, U1.18
D5: J4.27, U1.13
D6: J4.23, U1.15
D7: J4.19, U1.17
F_A0: J3.26, U2.3, U6.5, U7.5, U8.5, U9.5
F_A1: J3.28, U2.18, U6.4, U7.4, U8.4, U9.4
F_A2: J3.39, U2.12, U3.11
F_A3: J3.33, U2.16, U3.7
F_A4: J3.32, U2.5, U3.6
F_A5: J3.36, U2.14, U3.9
F_A6: J3.37, U2.9, U3.10
F_A7: J3.35, U2.7, U3.8
F_A8: J3.12, U3.13, U4.9
F_A9: J3.18, U3.14, U4.12
F_A10: J3.3, U3.15, U4.3
F_A11: J3.10, U3.21, U4.14
F_A12: J3.6, U3.22, U4.5
F_A13: J3.5, U3.23, U4.18
F_A14: J3.9, U4.7
F_A15: J3.8, U3.5, U4.16
F_D0: J3.29, U1.8, U6.8, U7.8, U8.8, U9.8
F_D1: J3.21, U1.4, U6.9, U7.9, U8.9, U9.9
F_D2: J3.31, U1.9, U6.10, U7.10, U8.10, U9.10
F_D3: J3.25, U1.6, U6.11, U7.11, U8.11, U9.11
F_D4: J3.17, U1.2, U6.2, U7.2, U8.2, U9.2
F_D5: J3.27, U1.7, U6.1, U7.1, U8.1, U9.1
F_D6: J3.23, U1.5, U6.12, U7.12, U8.12, U9.12
F_D7: J3.19, U1.3
GND: C1.2, C2.2, C3.2, C4.2, C5.2, C8.2, C9.2, C11.2, C13.2, C15.2, C18.2, C20.2, C21.2, J2.2, J2.4, J2.6, J2.8, J3.7, J3.30, J3.38, J4.7, J4.30, J4.38, JP1.2, JP2.2, U1.10, U2.10, U3.12, U4.10, U5.10, U6.7, U7.7, U8.7, U9.7
unnamed: U1.1, U3.18
S1: U3.16, U9.3
S2: U3.20, U6.3
S3: U3.17, U8.3
S4: U3.19, U7.3
~F_EXMEM~: J3.4, JP2.1, R5.2
~F_INTAK~: J3.13, J4.13
~F_INT~: J3.22, R2.2, U5.11
~F_IN~: J3.20, U3.3, U5.12
~F_MREQ~: J3.2, U5.18
~F_OUT~: J3.11, U3.1, U5.5
~F_READ~: J3.16, U3.2, U5.14
~F_SYSRES~: J3.1, U5.3
~F_WAIT~: J3.34, R1.2, U5.4
~F_WRITE~: J3.14, U3.4, U5.7
~INT~: J4.22, U5.9
~IN~: J4.20, U5.8
~ISOLATE~: JP1.1, R3.2, R4.2, U1.19, U2.1, U2.19, U4.1, U4.19, U5.1, U5.19
~MREQ~: J4.2, U5.2
~OUT~: J4.11, U5.15
~READ~: J4.16, U5.6
~SYSRES~: J4.1, U5.17
~WAIT~: J4.34, U5.16
~WRITE~: J4.14, U5.13
