alnwlsn/wc-80-archive/boards/video-mc6845/rev2/main.kicad_pcb

## KiCad design boards/video-mc6845/rev2/main.kicad_pcb (2025-07-11)

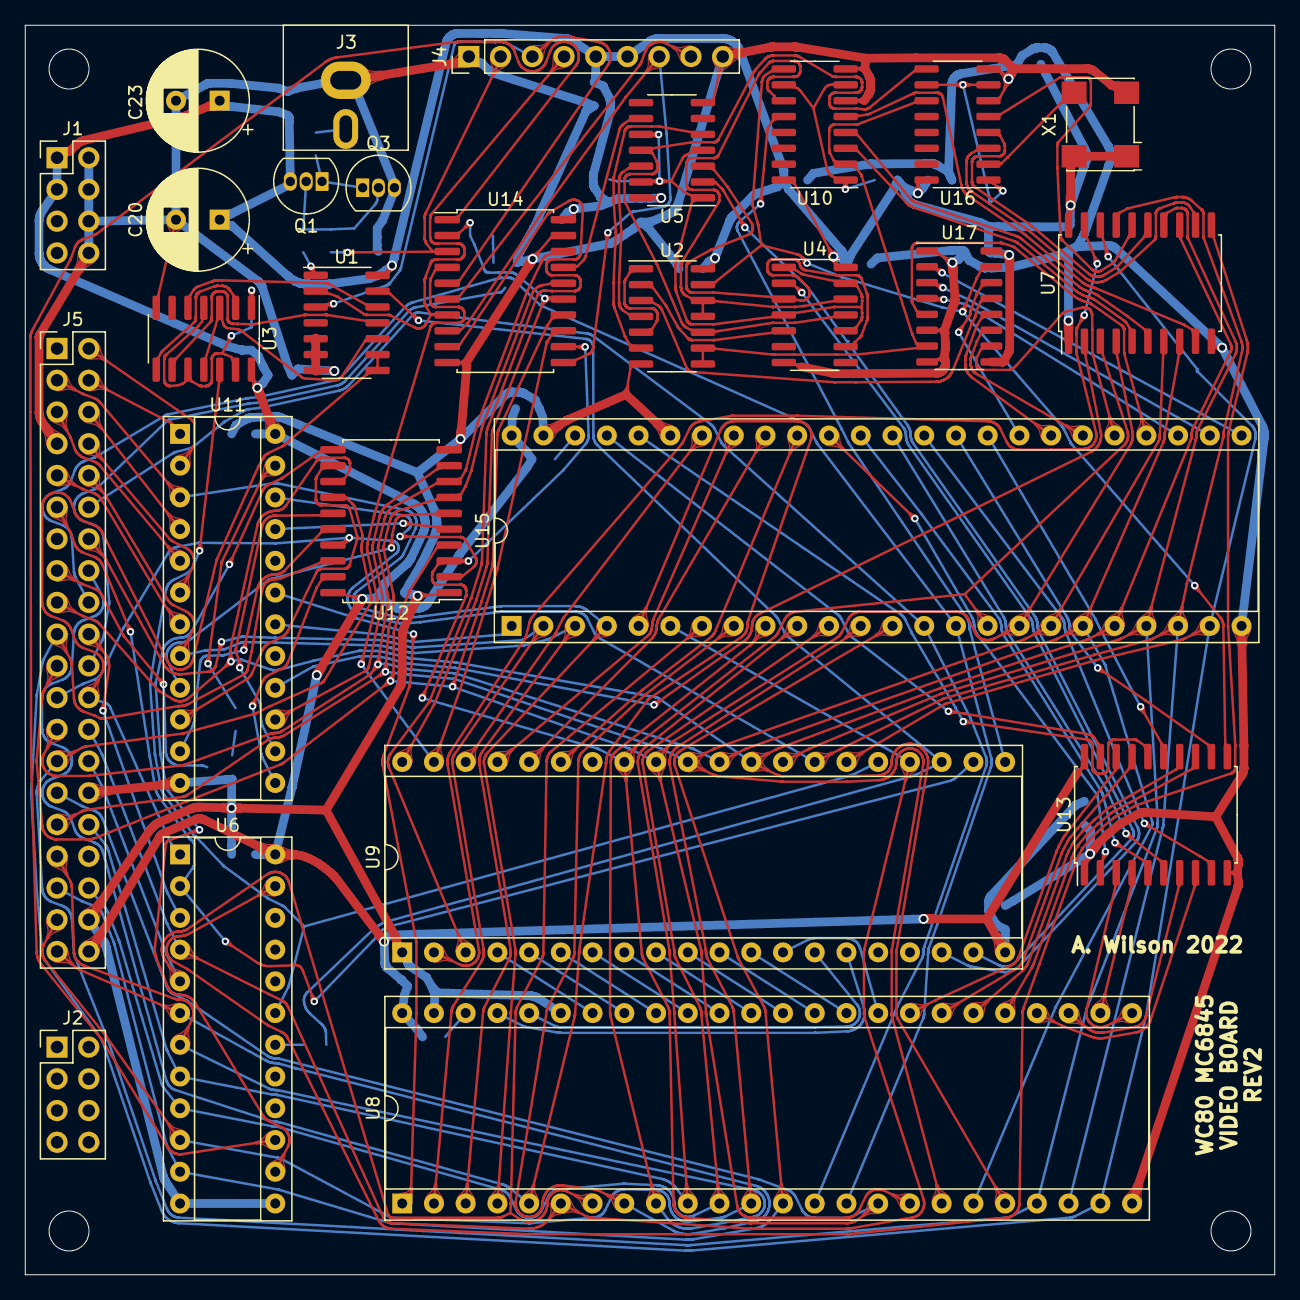
[picture p121: board boards/video-mc6845/rev2/main.kicad_pcb from above]

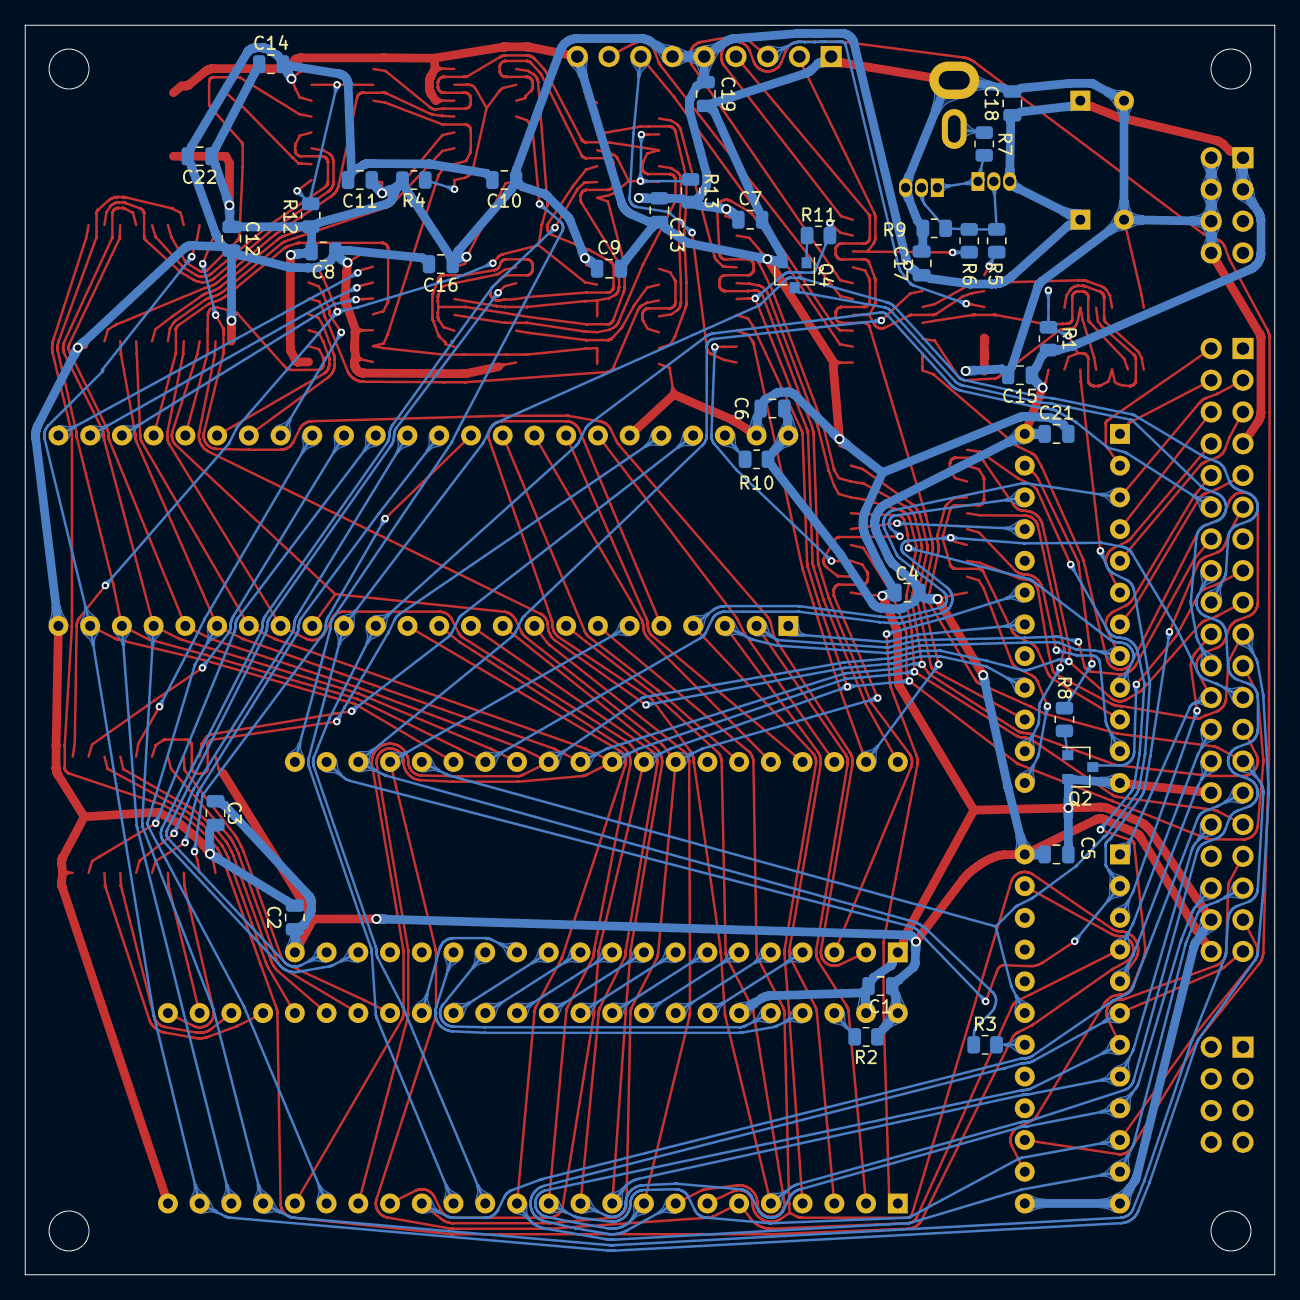
[picture p122: board boards/video-mc6845/rev2/main.kicad_pcb from below]

Board: 2 copper layers, 100.0 x 100.0 mm, 67 parts (36 on the bottom side), 139 nets.

Parts:
C1, C2, C3, C4, C5, C6, C7, C8, C9, C10, C11, C12, C13, C14, C15, C16, C17, C18, C19, C21, C22: 100n; C_0805_2012Metric
C20, C23: 470uF; CP_Radial_D8.0mm_P3.50mm
J1, J2: Conn_02x04_Odd_Even; PinHeader_2x04_P2.54mm_Vertical
J3: Conn_Coaxial; AV-5
J4: Conn_01x09_Male; PinHeader_1x09_P2.54mm_Vertical
J5: TRS80W-header; PinHeader_2x20_P2.54mm_Vertical
M1, M2, M3, M4: 3mm-mounting-hole; MountingHole_3.2mm_M3_DIN965
Q1: 2N3904; TO-92_Inline
Q2, Q4: BSS138; SOT-23
Q3: 2N3906; TO-92_Inline
R1, R2, R4, R10, R12, R13: 10K; R_0805_2012Metric
R3: optional; R_0805_2012Metric
R5: 910; R_0805_2012Metric
R6: 750; R_0805_2012Metric
R7: 75; R_0805_2012Metric
R8, R11: 100; R_0805_2012Metric
R9: 510; R_0805_2012Metric
U1, U2: 74LS02; SOIC-14_3.9x8.7mm_P1.27mm
U3, U4, U5: 74LS74; SOIC-14_3.9x8.7mm_P1.27mm
U6, U11: ATF22V10C; DIP-24_W7.62mm_Socket
U7, U12, U13: 74LS374; SOIC-20W_7.5x12.8mm_P1.27mm
U8: SCREENMEM; DIP-48_W15.24mm_Socket
U9: MC68B45; DIP-40_W15.24mm_Socket
U10, U16: 74LS163; SOIC-16_3.9x9.9mm_P1.27mm
U14: 74LS244; SOIC-20W_7.5x12.8mm_P1.27mm
U15: CHARROM; DIP-48_W15.24mm_Socket
U17: 74LS166; SO-16_3.9x9.9mm_P1.27mm
X1: SG-7050CAN; Oscillator_SMD_SeikoEpson_SG8002CA-4Pin_7.0x5.0mm

Connections:
74_PULL: R13.1, U4.1, U4.4, U4.10, U4.13, U5.1, U5.4, U5.10, U5.13
+5V: C1.1, C2.1, C3.1, C4.1, C5.1, C6.1, C7.1, C8.1, C9.1, C10.1, C11.1, C12.1, C13.1, C14.1, C15.1, C16.1, C17.1, C18.1, C19.1, C20.1, C21.1, C22.1, C23.1, J1.1, J1.3, J4.5, J4.6, J5.40, Q1.3, R1.2, R2.1, R4.2, R10.2, R12.2, R13.2, U1.14, U2.14, U3.14, U4.14, U5.14, U6.24, U7.20, U8.48, U9.20, U10.16, U11.24, U12.20, U13.20, U14.20, U15.48, U16.16, U17.9, U17.16, X1.1, X1.4
/CA0: U13.2, U15.38
/CA1: U13.5, U15.37
/CA2: U13.6, U15.36
/CA3: U13.9, U15.35
/CA4: U13.12, U15.34
/CA5: U13.15, U15.33
/CA6: U13.16, U15.44
/CA7: U13.19, U15.45
/CD0: U15.25, U17.2
/CD1: U15.26, U17.3
/CD2: U15.27, U17.4
/CD3: U15.28, U17.5
/CD4: U15.29, U17.10
/CD5: U15.30, U17.11
/CD6: U15.31, U17.12
/CD7: U15.32, U17.14
/CL74PU2: R1.1, U3.1, U3.4, U3.10, U3.13
/CRPU: R10.1, U15.46
/CURSOR: U2.2, U4.5
/CURSU: U4.2, U9.19
/DEU: U5.2, U9.18
/DIV1PU: R4.1, U10.1, U10.7, U10.10
/DIV2PU: R12.1, U16.1, U16.7, U16.10
/HSB: J4.4, U1.2, U14.7
/IMGU: U2.4, U5.12
/IUR: Q2.1, R8.1
/IUU: R8.2, U11.23
/LPBU: J4.8, U14.6
/LPU: J4.7, U14.8, U14.11
/MA0: U8.42, U9.4
/MA1: U8.41, U9.5
/MA2: U8.40, U9.6
/MA3: U8.39, U9.7
/MA4: U8.38, U9.8
/MA5: U8.37, U9.9
/MA6: U8.36, U9.10
/MA7: U8.35, U9.11
/MA8: U8.34, U9.12
/MA9: U8.33, U9.13
/MA10: U8.44, U9.14
/MA11: U8.45, U9.15
/NIMAGE: J4.2, R6.2, U14.3
/NOU: Q1.1, Q3.1, R7.2
/NOUT: J3.1, R7.1
/NSYNC: R5.2, U1.1
/NVDC: Q1.2, Q3.2, R5.1, R6.1, R9.2
/OMCS: R3.2, U6.18
/RA0: U9.38, U15.42
/RA1: U9.37, U15.41
/RA2: U9.36, U15.40
/RA3: U9.35, U15.39
/SD0: U8.25, U13.3
/SD1: U8.26, U13.4
/SD2: U8.27, U13.7
/SD3: U8.28, U13.8
/SD4: U8.29, U13.13
/SD5: U8.30, U13.14
/SD6: U8.31, U13.17
/SD7: U8.32, U13.18
/SRPU: R2.2, U8.46
/VSB: J4.3, U1.3, U14.5
/VSR: Q4.1, R11.1
/~DISPEN~: U2.6, U5.5
ADR0: U11.10, U12.12
ADR1: U11.14, U12.15
ADR2: U11.11, U12.16
ADR3: U11.13, U12.19
CHARCLOCK: U2.13, U10.9, U13.11, U17.15
CRTCCLOCK: U9.21, U10.12
DC0: U7.12, U16.3
DC1: U7.15, U16.4
DC2: U7.16, U16.5
DOTCLOCK: U2.8, U2.9, U10.2, U16.11, U17.7
F_A0: J5.26, U6.4, U8.6, U9.24, U15.6
F_A1: J5.28, U6.5, U8.7, U15.7
F_A2: J5.39, U6.6, U8.8, U15.8
F_A3: J5.33, U6.7, U8.9, U15.9
F_A4: J5.32, U6.8, U8.10, U15.10
F_A5: J5.36, U6.9, U8.11, U15.11
F_A6: J5.37, U6.10, U8.12, U15.12
F_A7: J5.35, U6.11, U8.13, U15.13
F_A8: J5.12, U8.14, U15.14
F_A9: J5.18, U8.15, U15.15
F_A10: J5.3, U8.4, U11.3, U15.4
F_A11: J5.10, U8.3, U11.8, U15.3
F_A12: J5.6, U11.4
F_A13: J5.5, U11.5
F_A14: J5.9, U11.7
F_A15: J5.8, U11.6
F_D0: J5.29, U7.3, U8.16, U9.33, U12.3, U14.12, U15.16
F_D1: J5.21, U7.4, U8.17, U9.32, U12.4, U14.14, U15.17
F_D2: J5.31, U7.7, U8.18, U9.31, U12.7, U14.16, U15.18
F_D3: J5.25, U7.8, U8.19, U9.30, U12.8, U14.18, U15.19
F_D4: J5.17, U7.13, U8.20, U9.29, U12.13, U15.20
F_D5: J5.27, U7.14, U8.21, U9.28, U12.14, U15.21
F_D6: J5.23, U7.17, U8.22, U9.27, U12.17, U15.22
F_D7: J5.19, U7.18, U8.23, U9.26, U12.18, U15.23
GND: C1.2, C2.2, C3.2, C4.2, C5.2, C6.2, C7.2, C8.2, C9.2, C10.2, C11.2, C12.2, C13.2, C14.2, C15.2, C16.2, C17.2, C18.2, C19.2, C20.2, C21.2, C22.2, C23.2, J1.2, J1.4, J1.6, J1.8, J3.2, J4.1, J4.9, J5.7, J5.30, J5.38, Q2.2, Q3.3, Q4.2, R9.1, U1.5, U1.6, U1.7, U2.7, U3.7, U4.7, U5.7, U6.12, U6.13, U7.1, U7.10, U8.24, U8.43, U8.47, U9.1, U10.6, U10.8, U11.12, U12.1, U12.10, U13.1, U13.10, U14.10, U14.19, U15.24, U15.43, U15.47, U16.6, U16.8, U17.1, U17.6, U17.8, X1.2
HS: U9.39, U14.4, U14.13
IMAGE: U5.9, U14.17
LIGHTPEN: U9.3, U14.9
MC6845E: R3.1, U1.13, U9.23
MSK0: U11.22, U12.2
MSK1: U11.21, U12.5
MSK2: U11.9, U12.6
MSK3: U11.15, U12.9
unnamed: U1.10, U3.3, U3.11
unnamed: U1.11, U3.9
unnamed: U1.12, U3.5
unnamed: U2.1, U2.5
unnamed: U3.2, U3.8
unnamed: U4.3, U4.9, U5.3
unnamed: U2.11, U2.12, U4.12, U10.11
unnamed: U16.2, X1.3
unnamed: U2.3, U17.13
OPT8: U7.2, U11.16
OPTIONS1: U6.14, U12.11
OPTIONS2: U6.23, U7.11
PL0: U7.5, U10.3
PL1: U7.6, U10.4
PL2: U7.9, U10.5
VIDSTAT: U6.15, U14.1
VS: R11.2, U9.40, U14.2, U14.15
Z80CLK: J5.24, U1.8, U1.9, U6.1
~CRMEM~: U11.18, U15.1
~DOTCLOCK~: U2.10, U4.11, U5.11, U16.9
~EXMEM~: J5.4, U11.1
~F_IN~: J5.20, U6.3
~F_OUT~: J5.11, U6.2, U9.22
~F_RD~: J5.16, U8.5, U15.5
~F_WR~: J5.14, U8.2, U15.2
~INT~: J5.22, Q4.3
~INUSE~: J5.15, Q2.3
~MC6845CS~: U3.12, U6.19, U9.25
~MEMRQ~: J5.2, U11.2
~SCMEM~: U8.1, U11.19
~SYSRES~: U7.19, U9.2
