alnwlsn/wc-80-archive/boards/backplane2/new/main.kicad_sch

## KiCad design boards/backplane2/new/main.kicad_sch (2025-07-11)

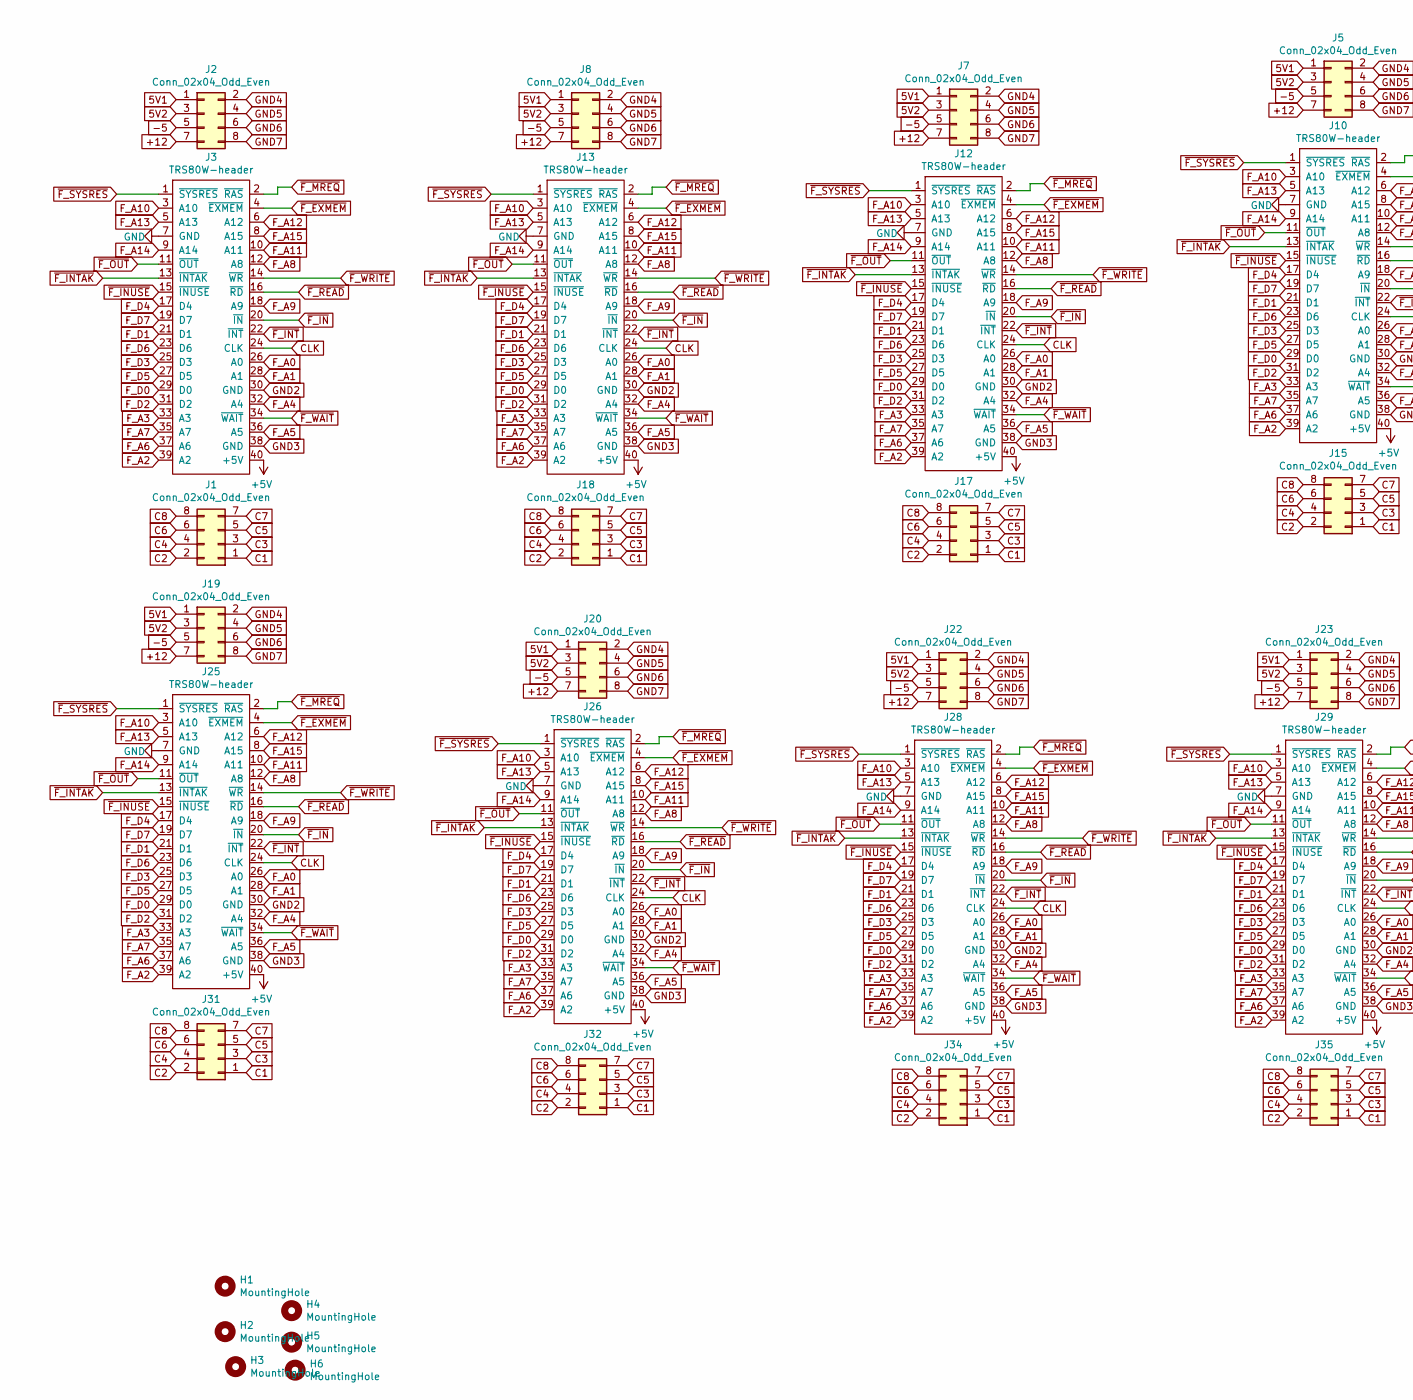
[picture p123: schematic main.kicad_sch, part in row 1, column 1]

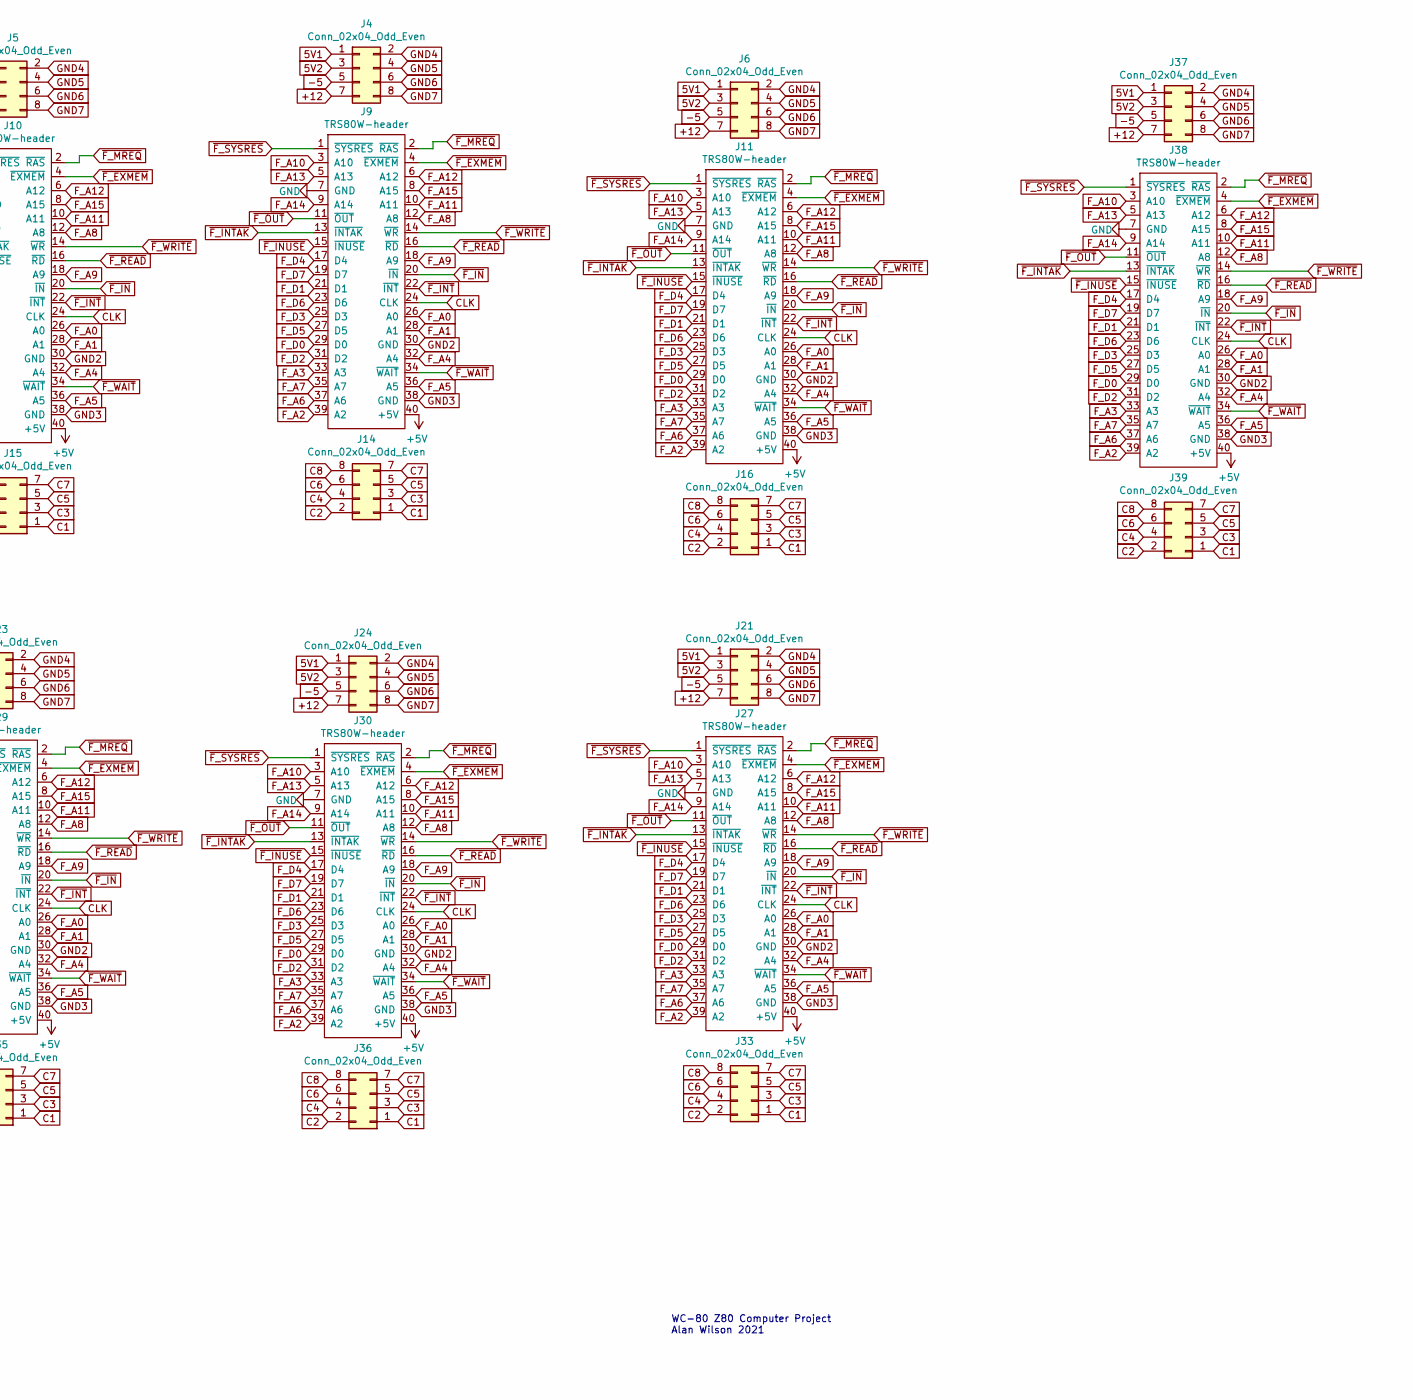
[picture p124: schematic main.kicad_sch, part in row 1, column 2]

Parts:
H1, H2, H3, H4, H5, H6: MountingHole; MountingHole_3.2mm_M3_DIN965
J1, J2, J4, J5, J6, J7, J8, J14, J15, J16, J17, J18, J19, J20, J21, J22, J23, J24, J31, J32, J33, J34, J35, J36, J37, J39: Conn_02x04_Odd_Even; PinHeader_2x04_P2.54mm_Vertical
J3, J9, J10, J11, J12, J13, J25, J26, J27, J28, J29, J30, J38: TRS80W-header; PinHeader_2x20_P2.54mm_Vertical

Connections:
5V1: J2.1, J4.1, J5.1, J6.1, J7.1, J8.1, J19.1, J20.1, J21.1, J22.1, J23.1, J24.1, J37.1
5V2: J2.3, J4.3, J5.3, J6.3, J7.3, J8.3, J19.3, J20.3, J21.3, J22.3, J23.3, J24.3, J37.3
+5V: J3.40 (+5V), J9.40 (+5V), J10.40 (+5V), J11.40 (+5V), J12.40 (+5V), J13.40 (+5V), J25.40 (+5V), J26.40 (+5V), J27.40 (+5V), J28.40 (+5V), J29.40 (+5V), J30.40 (+5V), J38.40 (+5V)
+12: J2.7, J4.7, J5.7, J6.7, J7.7, J8.7, J19.7, J20.7, J21.7, J22.7, J23.7, J24.7, J37.7
-5: J2.5, J4.5, J5.5, J6.5, J7.5, J8.5, J19.5, J20.5, J21.5, J22.5, J23.5, J24.5, J37.5
C1: J1.1, J14.1, J15.1, J16.1, J17.1, J18.1, J31.1, J32.1, J33.1, J34.1, J35.1, J36.1, J39.1
C2: J1.2, J14.2, J15.2, J16.2, J17.2, J18.2, J31.2, J32.2, J33.2, J34.2, J35.2, J36.2, J39.2
C3: J1.3, J14.3, J15.3, J16.3, J17.3, J18.3, J31.3, J32.3, J33.3, J34.3, J35.3, J36.3, J39.3
C4: J1.4, J14.4, J15.4, J16.4, J17.4, J18.4, J31.4, J32.4, J33.4, J34.4, J35.4, J36.4, J39.4
C5: J1.5, J14.5, J15.5, J16.5, J17.5, J18.5, J31.5, J32.5, J33.5, J34.5, J35.5, J36.5, J39.5
C6: J1.6, J14.6, J15.6, J16.6, J17.6, J18.6, J31.6, J32.6, J33.6, J34.6, J35.6, J36.6, J39.6
C7: J1.7, J14.7, J15.7, J16.7, J17.7, J18.7, J31.7, J32.7, J33.7, J34.7, J35.7, J36.7, J39.7
C8: J1.8, J14.8, J15.8, J16.8, J17.8, J18.8, J31.8, J32.8, J33.8, J34.8, J35.8, J36.8, J39.8
CLK: J3.24 (CLK), J9.24 (CLK), J10.24 (CLK), J11.24 (CLK), J12.24 (CLK), J13.24 (CLK), J25.24 (CLK), J26.24 (CLK), J27.24 (CLK), J28.24 (CLK), J29.24 (CLK), J30.24 (CLK), J38.24 (CLK)
F_A0: J3.26 (A0), J9.26 (A0), J10.26 (A0), J11.26 (A0), J12.26 (A0), J13.26 (A0), J25.26 (A0), J26.26 (A0), J27.26 (A0), J28.26 (A0), J29.26 (A0), J30.26 (A0), J38.26 (A0)
F_A1: J3.28 (A1), J9.28 (A1), J10.28 (A1), J11.28 (A1), J12.28 (A1), J13.28 (A1), J25.28 (A1), J26.28 (A1), J27.28 (A1), J28.28 (A1), J29.28 (A1), J30.28 (A1), J38.28 (A1)
F_A2: J3.39 (A2), J9.39 (A2), J10.39 (A2), J11.39 (A2), J12.39 (A2), J13.39 (A2), J25.39 (A2), J26.39 (A2), J27.39 (A2), J28.39 (A2), J29.39 (A2), J30.39 (A2), J38.39 (A2)
F_A3: J3.33 (A3), J9.33 (A3), J10.33 (A3), J11.33 (A3), J12.33 (A3), J13.33 (A3), J25.33 (A3), J26.33 (A3), J27.33 (A3), J28.33 (A3), J29.33 (A3), J30.33 (A3), J38.33 (A3)
F_A4: J3.32 (A4), J9.32 (A4), J10.32 (A4), J11.32 (A4), J12.32 (A4), J13.32 (A4), J25.32 (A4), J26.32 (A4), J27.32 (A4), J28.32 (A4), J29.32 (A4), J30.32 (A4), J38.32 (A4)
F_A5: J3.36 (A5), J9.36 (A5), J10.36 (A5), J11.36 (A5), J12.36 (A5), J13.36 (A5), J25.36 (A5), J26.36 (A5), J27.36 (A5), J28.36 (A5), J29.36 (A5), J30.36 (A5), J38.36 (A5)
F_A6: J3.37 (A6), J9.37 (A6), J10.37 (A6), J11.37 (A6), J12.37 (A6), J13.37 (A6), J25.37 (A6), J26.37 (A6), J27.37 (A6), J28.37 (A6), J29.37 (A6), J30.37 (A6), J38.37 (A6)
F_A7: J3.35 (A7), J9.35 (A7), J10.35 (A7), J11.35 (A7), J12.35 (A7), J13.35 (A7), J25.35 (A7), J26.35 (A7), J27.35 (A7), J28.35 (A7), J29.35 (A7), J30.35 (A7), J38.35 (A7)
F_A8: J3.12 (A8), J9.12 (A8), J10.12 (A8), J11.12 (A8), J12.12 (A8), J13.12 (A8), J25.12 (A8), J26.12 (A8), J27.12 (A8), J28.12 (A8), J29.12 (A8), J30.12 (A8), J38.12 (A8)
F_A9: J3.18 (A9), J9.18 (A9), J10.18 (A9), J11.18 (A9), J12.18 (A9), J13.18 (A9), J25.18 (A9), J26.18 (A9), J27.18 (A9), J28.18 (A9), J29.18 (A9), J30.18 (A9), J38.18 (A9)
F_A10: J3.3 (A10), J9.3 (A10), J10.3 (A10), J11.3 (A10), J12.3 (A10), J13.3 (A10), J25.3 (A10), J26.3 (A10), J27.3 (A10), J28.3 (A10), J29.3 (A10), J30.3 (A10), J38.3 (A10)
F_A11: J3.10 (A11), J9.10 (A11), J10.10 (A11), J11.10 (A11), J12.10 (A11), J13.10 (A11), J25.10 (A11), J26.10 (A11), J27.10 (A11), J28.10 (A11), J29.10 (A11), J30.10 (A11), J38.10 (A11)
F_A12: J3.6 (A12), J9.6 (A12), J10.6 (A12), J11.6 (A12), J12.6 (A12), J13.6 (A12), J25.6 (A12), J26.6 (A12), J27.6 (A12), J28.6 (A12), J29.6 (A12), J30.6 (A12), J38.6 (A12)
F_A13: J3.5 (A13), J9.5 (A13), J10.5 (A13), J11.5 (A13), J12.5 (A13), J13.5 (A13), J25.5 (A13), J26.5 (A13), J27.5 (A13), J28.5 (A13), J29.5 (A13), J30.5 (A13), J38.5 (A13)
F_A14: J3.9 (A14), J9.9 (A14), J10.9 (A14), J11.9 (A14), J12.9 (A14), J13.9 (A14), J25.9 (A14), J26.9 (A14), J27.9 (A14), J28.9 (A14), J29.9 (A14), J30.9 (A14), J38.9 (A14)
F_A15: J3.8 (A15), J9.8 (A15), J10.8 (A15), J11.8 (A15), J12.8 (A15), J13.8 (A15), J25.8 (A15), J26.8 (A15), J27.8 (A15), J28.8 (A15), J29.8 (A15), J30.8 (A15), J38.8 (A15)
F_D0: J3.29 (D0), J9.29 (D0), J10.29 (D0), J11.29 (D0), J12.29 (D0), J13.29 (D0), J25.29 (D0), J26.29 (D0), J27.29 (D0), J28.29 (D0), J29.29 (D0), J30.29 (D0), J38.29 (D0)
F_D1: J3.21 (D1), J9.21 (D1), J10.21 (D1), J11.21 (D1), J12.21 (D1), J13.21 (D1), J25.21 (D1), J26.21 (D1), J27.21 (D1), J28.21 (D1), J29.21 (D1), J30.21 (D1), J38.21 (D1)
F_D2: J3.31 (D2), J9.31 (D2), J10.31 (D2), J11.31 (D2), J12.31 (D2), J13.31 (D2), J25.31 (D2), J26.31 (D2), J27.31 (D2), J28.31 (D2), J29.31 (D2), J30.31 (D2), J38.31 (D2)
F_D3: J3.25 (D3), J9.25 (D3), J10.25 (D3), J11.25 (D3), J12.25 (D3), J13.25 (D3), J25.25 (D3), J26.25 (D3), J27.25 (D3), J28.25 (D3), J29.25 (D3), J30.25 (D3), J38.25 (D3)
F_D4: J3.17 (D4), J9.17 (D4), J10.17 (D4), J11.17 (D4), J12.17 (D4), J13.17 (D4), J25.17 (D4), J26.17 (D4), J27.17 (D4), J28.17 (D4), J29.17 (D4), J30.17 (D4), J38.17 (D4)
F_D5: J3.27 (D5), J9.27 (D5), J10.27 (D5), J11.27 (D5), J12.27 (D5), J13.27 (D5), J25.27 (D5), J26.27 (D5), J27.27 (D5), J28.27 (D5), J29.27 (D5), J30.27 (D5), J38.27 (D5)
F_D6: J3.23 (D6), J9.23 (D6), J10.23 (D6), J11.23 (D6), J12.23 (D6), J13.23 (D6), J25.23 (D6), J26.23 (D6), J27.23 (D6), J28.23 (D6), J29.23 (D6), J30.23 (D6), J38.23 (D6)
F_D7: J3.19 (D7), J9.19 (D7), J10.19 (D7), J11.19 (D7), J12.19 (D7), J13.19 (D7), J25.19 (D7), J26.19 (D7), J27.19 (D7), J28.19 (D7), J29.19 (D7), J30.19 (D7), J38.19 (D7)
GND: J3.7 (GND), J9.7 (GND), J10.7 (GND), J11.7 (GND), J12.7 (GND), J13.7 (GND), J25.7 (GND), J26.7 (GND), J27.7 (GND), J28.7 (GND), J29.7 (GND), J30.7 (GND), J38.7 (GND)
GND2: J3.30 (GND), J9.30 (GND), J10.30 (GND), J11.30 (GND), J12.30 (GND), J13.30 (GND), J25.30 (GND), J26.30 (GND), J27.30 (GND), J28.30 (GND), J29.30 (GND), J30.30 (GND), J38.30 (GND)
GND3: J3.38 (GND), J9.38 (GND), J10.38 (GND), J11.38 (GND), J12.38 (GND), J13.38 (GND), J25.38 (GND), J26.38 (GND), J27.38 (GND), J28.38 (GND), J29.38 (GND), J30.38 (GND), J38.38 (GND)
GND4: J2.2, J4.2, J5.2, J6.2, J7.2, J8.2, J19.2, J20.2, J21.2, J22.2, J23.2, J24.2, J37.2
GND5: J2.4, J4.4, J5.4, J6.4, J7.4, J8.4, J19.4, J20.4, J21.4, J22.4, J23.4, J24.4, J37.4
GND6: J2.6, J4.6, J5.6, J6.6, J7.6, J8.6, J19.6, J20.6, J21.6, J22.6, J23.6, J24.6, J37.6
GND7: J2.8, J4.8, J5.8, J6.8, J7.8, J8.8, J19.8, J20.8, J21.8, J22.8, J23.8, J24.8, J37.8
~F_EXMEM: J3.4 (~EXMEM), J9.4 (~EXMEM), J10.4 (~EXMEM), J11.4 (~EXMEM), J12.4 (~EXMEM), J13.4 (~EXMEM), J25.4 (~EXMEM), J26.4 (~EXMEM), J27.4 (~EXMEM), J28.4 (~EXMEM), J29.4 (~EXMEM), J30.4 (~EXMEM), J38.4 (~EXMEM)
~F_INTAK: J3.13 (~INTAK), J9.13 (~INTAK), J10.13 (~INTAK), J11.13 (~INTAK), J12.13 (~INTAK), J13.13 (~INTAK), J25.13 (~INTAK), J26.13 (~INTAK), J27.13 (~INTAK), J28.13 (~INTAK), J29.13 (~INTAK), J30.13 (~INTAK), J38.13 (~INTAK)
~F_INT: J3.22 (~INT), J9.22 (~INT), J10.22 (~INT), J11.22 (~INT), J12.22 (~INT), J13.22 (~INT), J25.22 (~INT), J26.22 (~INT), J27.22 (~INT), J28.22 (~INT), J29.22 (~INT), J30.22 (~INT), J38.22 (~INT)
~F_INUSE: J3.15 (~INUSE), J9.15 (~INUSE), J10.15 (~INUSE), J11.15 (~INUSE), J12.15 (~INUSE), J13.15 (~INUSE), J25.15 (~INUSE), J26.15 (~INUSE), J27.15 (~INUSE), J28.15 (~INUSE), J29.15 (~INUSE), J30.15 (~INUSE), J38.15 (~INUSE)
~F_IN: J3.20 (~IN), J9.20 (~IN), J10.20 (~IN), J11.20 (~IN), J12.20 (~IN), J13.20 (~IN), J25.20 (~IN), J26.20 (~IN), J27.20 (~IN), J28.20 (~IN), J29.20 (~IN), J30.20 (~IN), J38.20 (~IN)
~F_MREQ: J3.2 (~RAS), J9.2 (~RAS), J10.2 (~RAS), J11.2 (~RAS), J12.2 (~RAS), J13.2 (~RAS), J25.2 (~RAS), J26.2 (~RAS), J27.2 (~RAS), J28.2 (~RAS), J29.2 (~RAS), J30.2 (~RAS), J38.2 (~RAS)
~F_OUT: J3.11 (~OUT), J9.11 (~OUT), J10.11 (~OUT), J11.11 (~OUT), J12.11 (~OUT), J13.11 (~OUT), J25.11 (~OUT), J26.11 (~OUT), J27.11 (~OUT), J28.11 (~OUT), J29.11 (~OUT), J30.11 (~OUT), J38.11 (~OUT)
~F_READ: J3.16 (~RD), J9.16 (~RD), J10.16 (~RD), J11.16 (~RD), J12.16 (~RD), J13.16 (~RD), J25.16 (~RD), J26.16 (~RD), J27.16 (~RD), J28.16 (~RD), J29.16 (~RD), J30.16 (~RD), J38.16 (~RD)
~F_SYSRES: J3.1 (~SYSRES), J9.1 (~SYSRES), J10.1 (~SYSRES), J11.1 (~SYSRES), J12.1 (~SYSRES), J13.1 (~SYSRES), J25.1 (~SYSRES), J26.1 (~SYSRES), J27.1 (~SYSRES), J28.1 (~SYSRES), J29.1 (~SYSRES), J30.1 (~SYSRES), J38.1 (~SYSRES)
~F_WAIT: J3.34 (~WAIT), J9.34 (~WAIT), J10.34 (~WAIT), J11.34 (~WAIT), J12.34 (~WAIT), J13.34 (~WAIT), J25.34 (~WAIT), J26.34 (~WAIT), J27.34 (~WAIT), J28.34 (~WAIT), J29.34 (~WAIT), J30.34 (~WAIT), J38.34 (~WAIT)
~F_WRITE: J3.14 (~WR), J9.14 (~WR), J10.14 (~WR), J11.14 (~WR), J12.14 (~WR), J13.14 (~WR), J25.14 (~WR), J26.14 (~WR), J27.14 (~WR), J28.14 (~WR), J29.14 (~WR), J30.14 (~WR), J38.14 (~WR)

Notes on the sheet:
WC-80 Z80 Computer Project Alan Wilson 2021
