alnwlsn/wc-80-archive/boards/cpu/cpu-rev2/cpu2/cpu2.kicad_sch

## KiCad design boards/cpu/cpu-rev2/cpu2/cpu2.kicad_sch (2025-07-11)

Schematic: cpu2.kicad_sch

Parts:
BT1: Battery_Cell; BS-01-A4CJ004
C1: 4u7; C_0805_2012Metric
C2: 2u2; C_0805_2012Metric
C3, C4, C5, C6, C7, C8, C9, C10, C11, C12, C13, C14, C15, C16, C18, C19, C20, C27, C28, C29: 100n; C_0805_2012Metric
C17, C21: 470uF; CP_Radial_D8.0mm_P3.50mm
C22: 100uF; CP_Elec_5x5.4
C23, C24: 220pF; C_0805_2012Metric
C25, C26: 10uF; C_0805_2012Metric
D3: HALT; LED_D3.0mm_FlatTop
D5: PWR; LED_D3.0mm_FlatTop
D8: 32; LED_D3.0mm_FlatTop
D9, D10, D11, D12, D13: 1N4148; D_SOD-123
J1, J2: Conn_02x04_Odd_Even; PinHeader_2x04_P2.54mm_Vertical
J3: TRS80W-header; PinHeader_2x20_P2.54mm_Vertical
J4: Conn_01x06_Male; PinHeader_1x06_P2.54mm_Vertical
M1, M2, M3, M4: 3mm-mounting-hole; MountingHole_3.2mm_M3_DIN965
Q1: 2N3904; TO-92_Inline
R3, R4, R52: 10; R_0805_2012Metric
R5, R6, R7, R9, R10, R15, R16, R17, R18, R19, R20, R21, R22, R23, R24, R25, R26, R27, R28, R29, R30, R31, R32, R33, R34, R35, R36, R37, R38, R39, R40, R41, R42, R43, R44, R45: 4k7; R_0805_2012Metric
R8, R11, R46, R48: 1K; R_0805_2012Metric
R47, R49: 7k5; R_0805_2012Metric
R50: 220K; R_0805_2012Metric
R51: 1.2K; R_0805_2012Metric
R53: 100; R_0805_2012Metric
R54, R61, R63, R65, R66: 470K; R_0805_2012Metric
R55, R59: 360K; R_0805_2012Metric
R56, R57: 1M; R_0805_2012Metric
R58: 560K; R_0805_2012Metric
R60: 1.8M; R_0805_2012Metric
R62: 680K; R_0805_2012Metric
R64: 10K; R_0805_2012Metric
SW1: NMI; SW_PUSH_6mm
SW2: RESET; SW_PUSH_6mm
U1, U20: 74LS175; SOIC-16_3.9x9.9mm_P1.27mm
U2: 74LS132; SOIC-14_3.9x8.7mm_P1.27mm
U3: 74LS163; SOIC-16_3.9x9.9mm_P1.27mm
U4: 74LS74; SOIC-14_3.9x8.7mm_P1.27mm
U5: Z80CPU; DIP-40_W15.24mm_Socket
U6: 74LS32; SOIC-14_3.9x8.7mm_P1.27mm
U8: SST39SF040; DIP-32_W15.24mm_Socket
U9: ATF22V10C; DIP-24_W7.62mm_Socket
U10: 74HC245; SO-20_5.3x12.6mm_P1.27mm
U11: AS6C4008; DIP-32_W15.24mm_Socket
U12, U15, U16: 74HC244; SO-20_5.3x12.6mm_P1.27mm
U13, U14: 74HC670; SOIC-16_3.9x9.9mm_P1.27mm
U17: LM3900D; SOIC-14_3.9x8.7mm_P1.27mm
U18: 74HCT02; SOIC-14_3.9x8.7mm_P1.27mm
U19: 74LS125; SOIC-14_3.9x8.7mm_P1.27mm
U21: SIP-1A05
U22: DS1210; SOIC-8_3.9x4.9mm_P1.27mm
X1: SG-7050CAN; Oscillator_SMD_SeikoEpson_SG8002CA-4Pin_7.0x5.0mm

Notes on the sheet:
WC-80 CPU rev2 - Alan Wilson 2022
rev3 - ~OUT~ can be changed to ~WR~, because ~OUT~ can be derived
